rboyd/fpv-drone-racing-gate/reference/picture_frame/ATTRIBUTION.md

# User-supplied picture-frame reference

Tony Youngblood, **Snap-Together Modular Picture Frame – Fits Any Size Picture**.

Source: https://printables.com/model/150138-snap-together-modular-picture-frame-fits-any-size

License stated in supplied PDF: **Creative Commons Attribution–ShareAlike 4.0 International**.
https://creativecommons.org/licenses/by-sa/4.0/

Extracted from the user-provided `~/Downloads/snap-together-modular-picture-frame-fits-any-size-picture-model_files.zip`. Only the three STL references used in Blender and the supplied documentation PDF are retained here. STL files are unchanged. In the study Blender scene 10, they are converted from millimetres to metres, repositioned, and given a display material. That reference scene/render is shared under CC BY-SA 4.0 with this attribution. The exported gate test coupons use newly constructed geometry; they are not dimensionally compatible with this reference model.

Design observations: repeated snap teeth and lengths, plus a small calibrator. Source print instructions require supports under some frame edges. Therefore the source meshes are reference-only, excluded from our A1 Mini support-free test plates.

The complete unmodified CC BY-SA 4.0 license is included in [LICENSE](LICENSE). The project's CC BY-NC-SA and PolyForm licenses do not restrict the permissions granted for this reference material.
