rboyd/fpv-drone-racing-gate/studies/posterboard_hybrid.html

# Posterboard + printed framing

Same 2700 × 2700 mm gate, 1500 mm opening and existing PVC backing. The two strongest candidates to test are 600 × 450 mm sheets with a middle support rib for low cost, and 300 × 250 mm inserts for smaller replaceable panels. Nominal panel sizes; a few end fillers preserve the exact gate dimensions.

Study, not a finished frame design. Shared rails avoid two separate frames along every seam. PETG figures include a 20% rail allowance for joints/nodes, 250 g for PVC mounts, and 10% printing waste. Existing PVC, brace connectors, bases and anchors are excluded.

Rail plastic cross-section: mm²
Filament price: $/kg
Posterboard price: $/sheet

## Material and effort comparison

Click a size to see its face layout and a verified sheet-cut pattern. Costs are for the new face system only.

Nominal panels | Pieces | Sheets | Rail length | PETG | 1 kg spools | Consumed material | Whole-spool purchase

## One 22 × 28 inch stock sheet

## What changes the result?

Paper size: a 300 mm square is just too wide to get two across the 558.8 mm stock width. A 300 × 250 rectangle yields four per sheet; mixed orientation yields five 300 × 200 rectangles. The true area-only minimum is 13 sheets, but these repeatable layouts need 17–28.

Panel support: smaller bays should flex less, but more rail joints do not automatically make the whole gate stronger. The middle-rib option retains 20 paper pieces while supporting each large panel as two roughly 300 × 450 mm bays. Ribs need light retainers to work under wind from both directions.

Printer size: use rail bodies up to 150 mm long plus compact connectors, within an approximately 170 mm envelope. Several rails can print together; rail piece counts are not print-job counts. One-piece 150 mm panel frames are possible, but duplicate the shared edges and use more material.

Outdoor use: the $0.99 listing describes cardstock and gives no wet-weather rating. Treat it as a replaceable dry-weather insert; framing does not waterproof it. Wind area remains approximately 5.04 m², so existing guying/ballast remains relevant.

Detailed study · Calculation table · Exact layouts and assumptions

Sources: Hobby Lobby $0.99 cardstock (https://www.hobbylobby.com/Art-Supplies/Project-Supplies/Poster-Projects/Poster-Board---22-x-28/p/81118411); PETG density 1.28 g/cm³. Prices exclude tax/shipping and are scenario assumptions except the listed posterboard price. No stiffness or wind rating is claimed.
