rboyd/fpv-drone-racing-gate/output/pvc_paper_gate/index.html

# PVC does the spanning / printed parts do the joining

One outer PVC perimeter and a PVC ring around each opening. Paper conceals the pipes and fittings from the front; magnets sit 18 mm inside the edges. The shared divider enables a 2700 × 4790.4 mm two-level obstacle.

Open Blender · Design and assembly PDF · Full guide · Download kit

Configuration | Pieces | PETG kg | Print h | $6 PVC sticks | Subtotal*
Basic single, long pipes | 64 | 1.370 | 56.6 | 7 | $69.40
Recommended single | 62 | 1.759 | 71.0 | 6 | $71.17
Two-level Split-S | 108 | 2.814 | 114.5 | 10 | $116.27

*PVC + PETG at $20/kg. Face skeleton only; add magnets, cord, paper, adhesive, base, guys and anchoring. Actual local A1 Mini slicing estimates. Five production part types for the recommended single and double.

First print: FIRST_FIT for the A1 Mini — 124.59 g / 4.95 hours. One outer corner, sleeve, cord saddle, bore gauge and optional front pad. Check actual pipe and magnet fit before printing the gate.

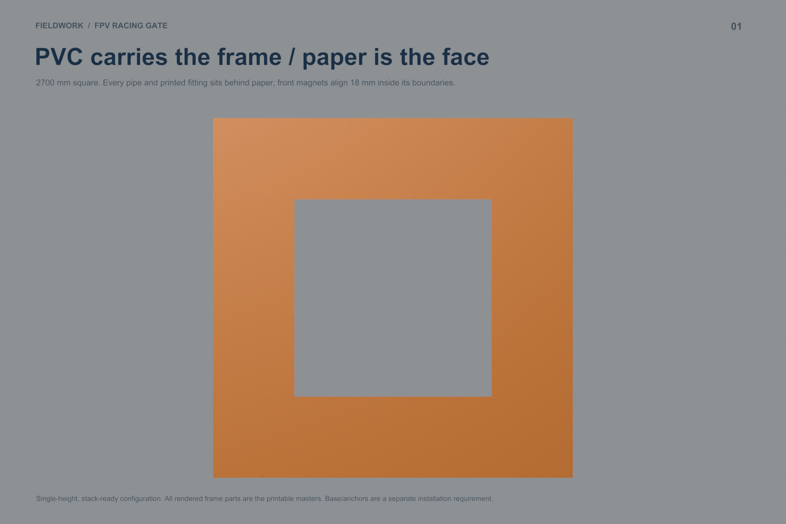
[picture p11: output/pvc_paper_gate/renders/01_SINGLE_FRONT.png]
01_SINGLE_FRONT


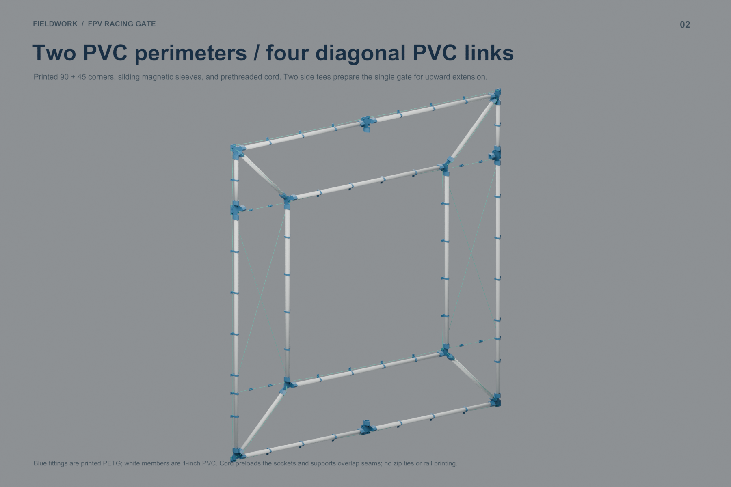
[picture p12: output/pvc_paper_gate/renders/02_SINGLE_BACK.png]
02_SINGLE_BACK


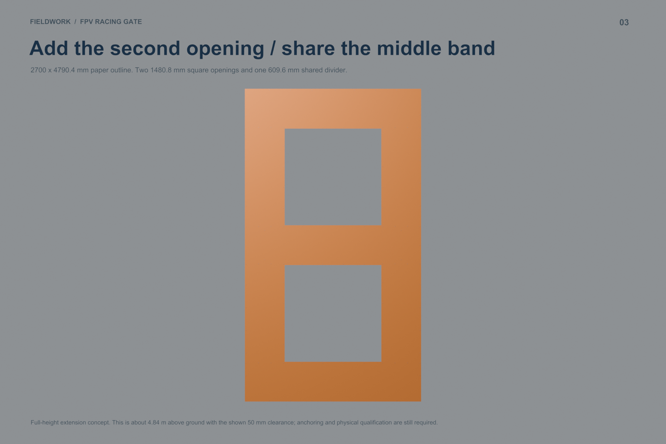
[picture p13: output/pvc_paper_gate/renders/03_SPLIT_S_FRONT.png]
03_SPLIT_S_FRONT


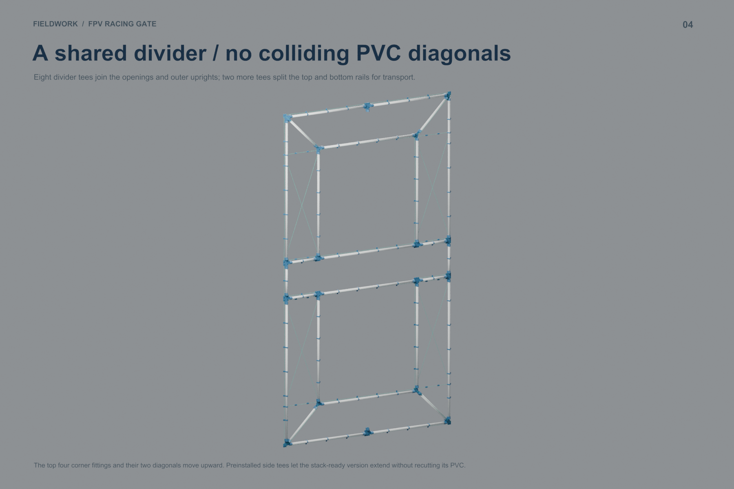
[picture p14: output/pvc_paper_gate/renders/04_SPLIT_S_BACK.png]
04_SPLIT_S_BACK


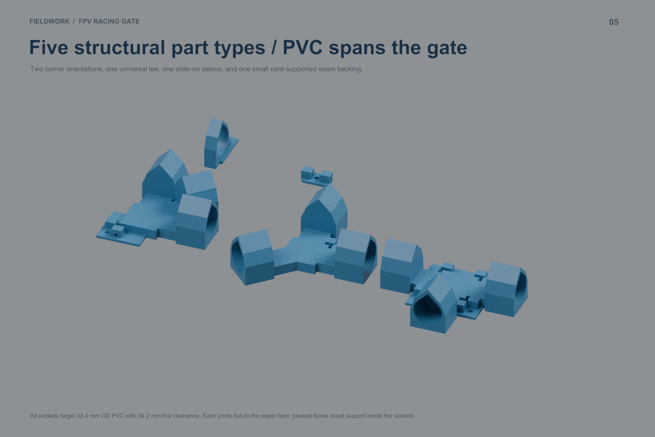
[picture p15: output/pvc_paper_gate/renders/05_PRINTED_PARTS.png]
05_PRINTED_PARTS


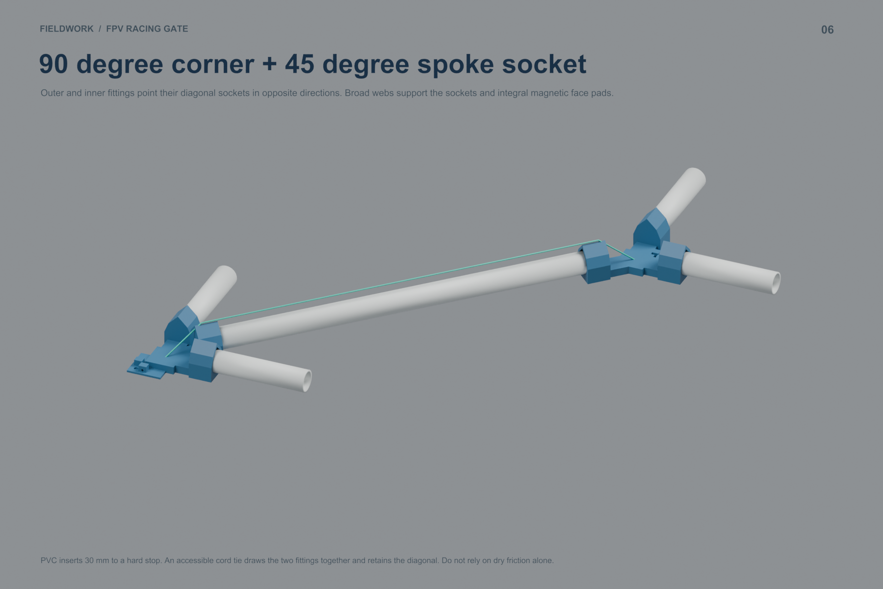
[picture p16: output/pvc_paper_gate/renders/06_CORNER_AND_DIAGONAL.png]
06_CORNER_AND_DIAGONAL


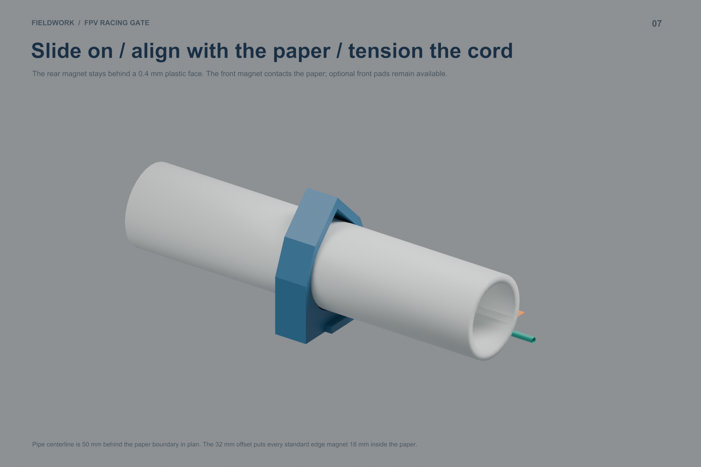
[picture p17: output/pvc_paper_gate/renders/07_MAGNET_SLEEVE.png]
07_MAGNET_SLEEVE


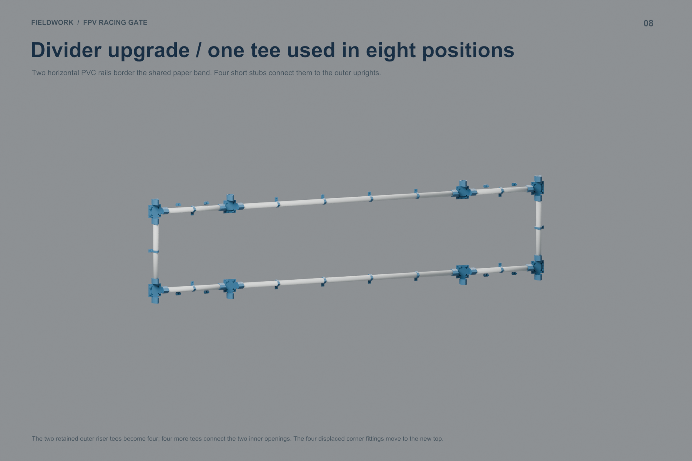
[picture p18: output/pvc_paper_gate/renders/08_SHARED_DIVIDER.png]
08_SHARED_DIVIDER


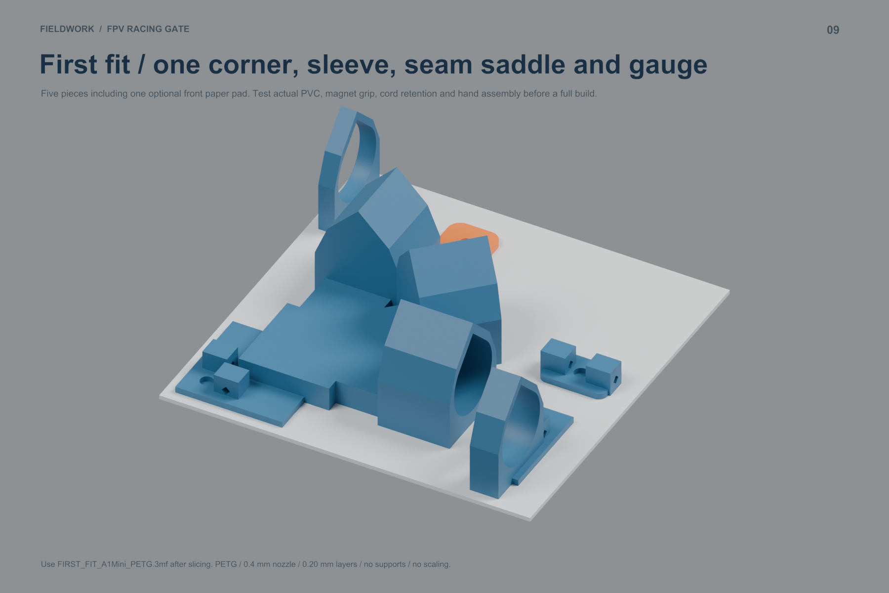
[picture p19: output/pvc_paper_gate/renders/09_FIRST_FIT_PLATE.png]
09_FIRST_FIT_PLATE


## Fabrication ledgers

### stack_ready

Parts · Print queue · PVC cuts · Stock nesting · Sleeve positions · Magnet positions · Paper cuts · Cord cuts · Face map

### split_s

Parts · Print queue · PVC cuts · Stock nesting · Sleeve positions · Magnet positions · Paper cuts · Cord cuts · Face map

### basic

Parts · Print queue · PVC cuts · Stock nesting · Sleeve positions · Magnet positions · Paper cuts · Cord cuts · Face map

Comparison · Upgrade parts · Upgrade PVC · Digital checks

All supplied plates fit with at least 5 mm bed clearance and slice without supports or warnings. Front pads are optional; the frame-side plastic skins and peaked sleeve roofs remain. Physical load testing and a qualified base/anchoring design remain outstanding, particularly at the 4.79 m stacked height. No printer job was submitted.
