rboyd/fpv-drone-racing-gate/output/paper_roll_study/index.html

FPV RACING GATE / EXPERIMENTAL ITERATION

# Paper face, click frame and magnetic clamps

Four identical 2090.4 × 609.6 mm strips. One PVC back. Compare three bracing layouts, reversible joints and diagonal break-apart print stacks.

Open Blender model · Visual study PDF · Assembly and test guide · Download study kit

Preferred trial: mechanical click joints + alternating diagonal webs + magnetic paper pads. Magnets can dominate cost: 336 discs at the pictured spacing. See the guide for wider spacing and magnet-free retention.

Experimental parts, not a production gate kit. Gate rails and full-gate dock sites are schematic. The exact exported interfaces fit the A1 Mini and have been sliced, but physical strength, latch fatigue, magnet grip and PETG stack separation have not been tested. The source picture-frame meshes are reference-only.

## Start with the seven-piece D-lug and PVC dock plate

Use plate 05 for the latest concept. A second optional test is the small stack plate. Do not print all 25 variants: they include clearance comparisons and alternative processes.

Sliced A1 Mini / PETG project | Material | Time | Notes
05_D_MAGNET_AND_DOCK | 33.2 g | 113 min | No slicing warning
01_CLICK_AND_MAGNET_JOINTS | 23.9 g | 65 min | No slicing warning
02_PAPER_CLAMP_TESTS | 32.9 g | 124 min | No slicing warning
03_STACK_SEPARATION_TESTS | 33.3 g | 94 min | No slicing warning
04_PVC_COLLAR_TEST | 23.4 g | 71 min | No slicing warning
DIAGONAL_1x220 | 15.9 g | 43 min | No slicing warning
DIAGONAL_8x220 | 104.3 g | 259 min | No slicing warning
06_OVERNIGHT_26_RAILS | 301.4 g | 714 min | No slicing warning

0.4 mm nozzle, 0.2 mm layers, 3 walls, 15% infill, textured PEI; supports off. No job has been sent to a printer. Source STLs/3MFs: printable folder. Digital checks · Stack findings · Research.

## Explore the Blender views

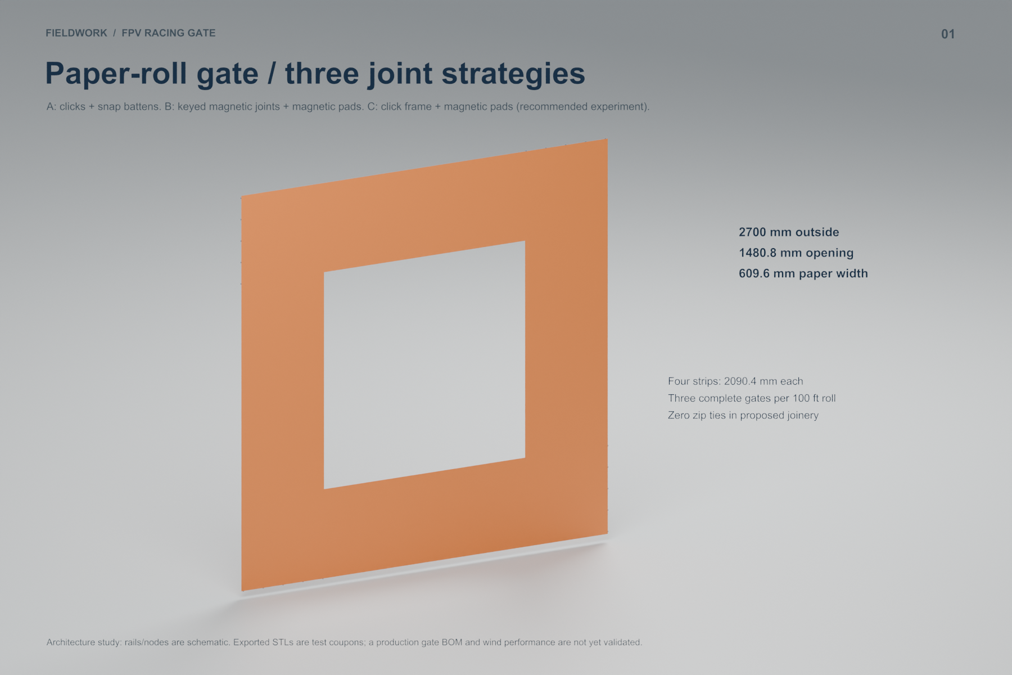
[picture p35: output/paper_roll_study/renders/01_PAPER_GATE.png]
Paper layout and three retention strategies


Paper layout and three retention strategies

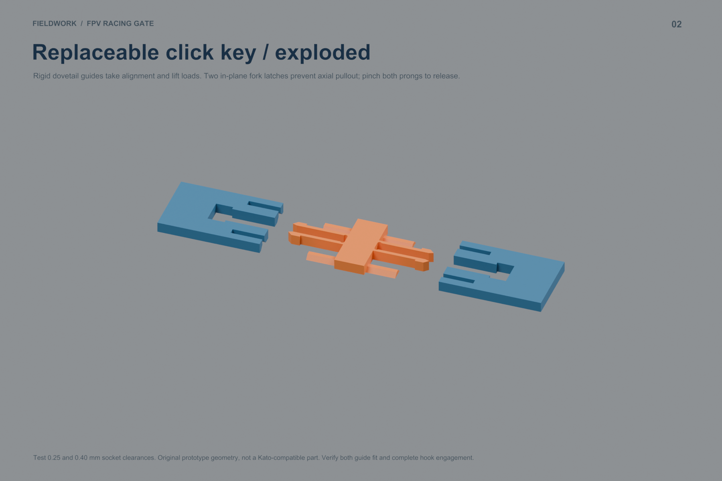
[picture p36: output/paper_roll_study/renders/02_CLICK_JOINT.png]
Replaceable click key and clearance samples


Replaceable click key and clearance samples

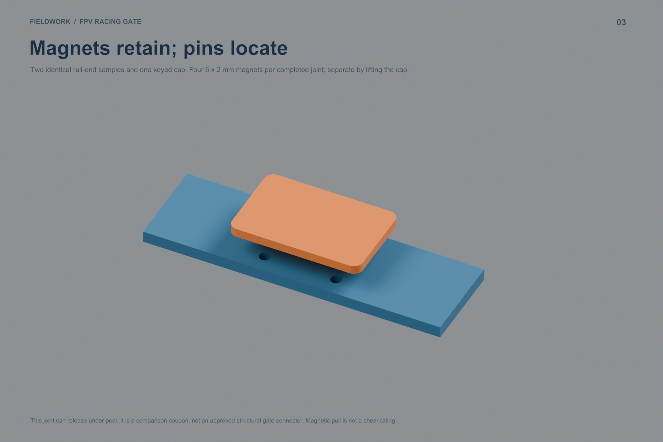
[picture p37: output/paper_roll_study/renders/03_MAGNETIC_SPLICE.png]
Magnet-held structural splice alternative


Magnet-held structural splice alternative

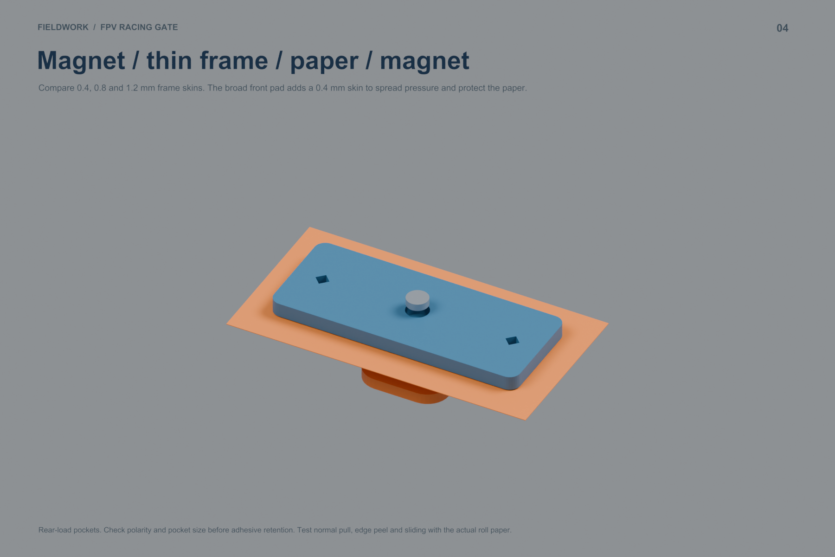
[picture p38: output/paper_roll_study/renders/04_PAPER_MAGNET_STACK.png]
Magnetic paper sandwich and skin thickness


Magnetic paper sandwich and skin thickness

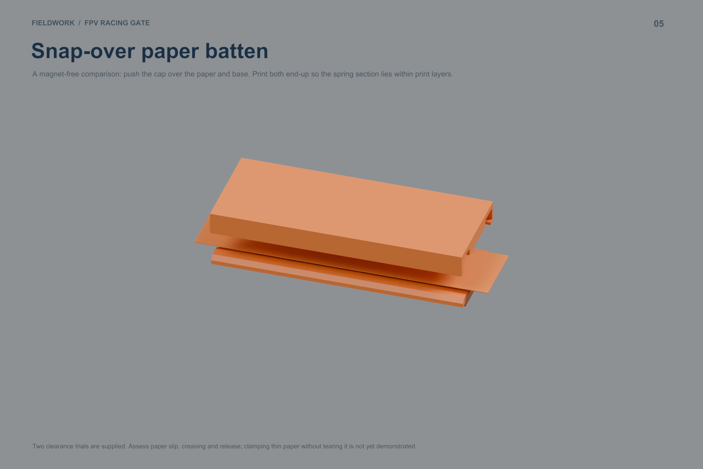
[picture p39: output/paper_roll_study/renders/05_MECHANICAL_PAPER_CLAMP.png]
Magnet-free snap-over batten


Magnet-free snap-over batten

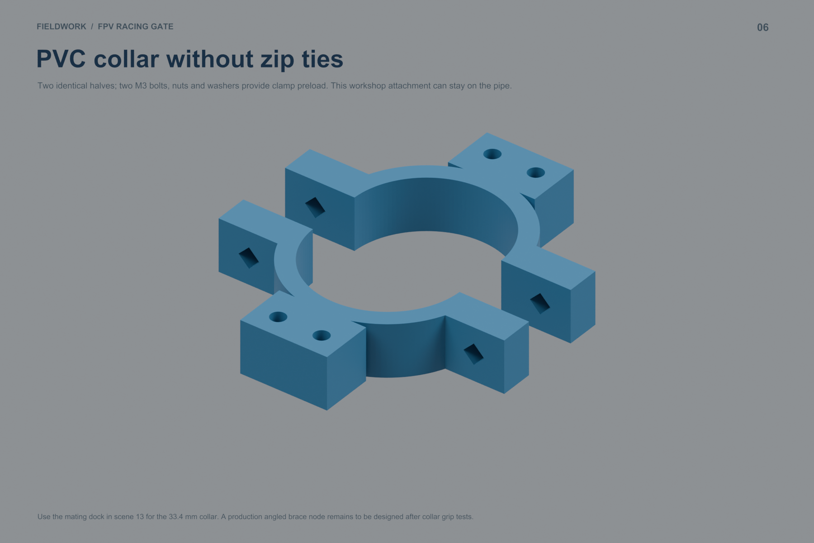
[picture p40: output/paper_roll_study/renders/06_NO_TIE_PVC_COLLAR.png]
Bolted PVC collar halves


Bolted PVC collar halves

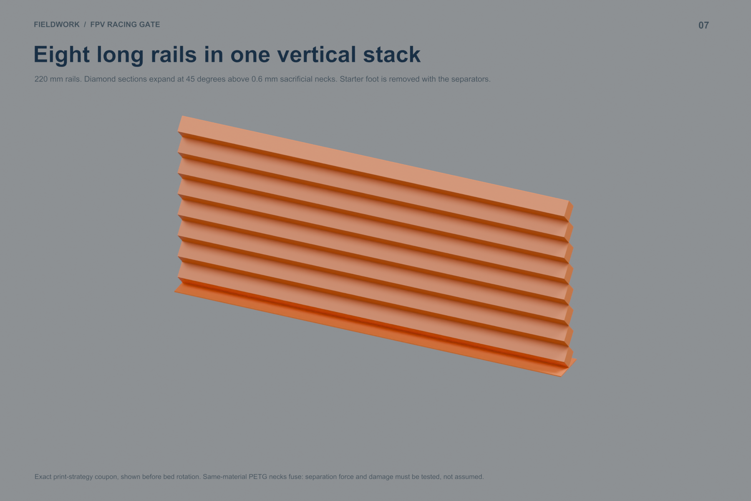
[picture p41: output/paper_roll_study/renders/07_DIAGONAL_STACK.png]
Eight 220 mm rails stacked vertically


Eight 220 mm rails stacked vertically

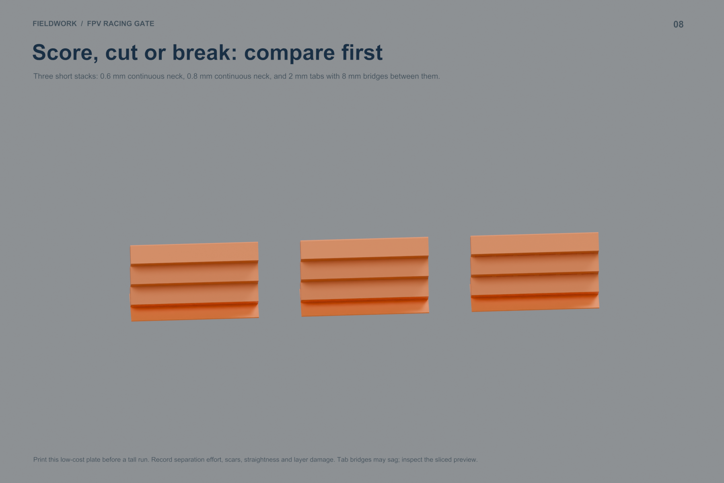
[picture p42: output/paper_roll_study/renders/08_STACK_COUPONS.png]
Short separation tests


Short separation tests

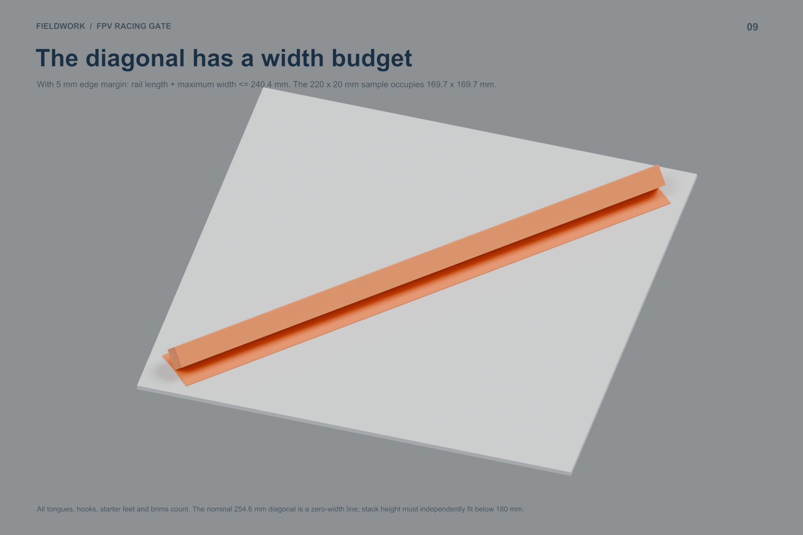
[picture p43: output/paper_roll_study/renders/09_A1_DIAGONAL_ENVELOPE.png]
Diagonal bed-fit calculation


Diagonal bed-fit calculation

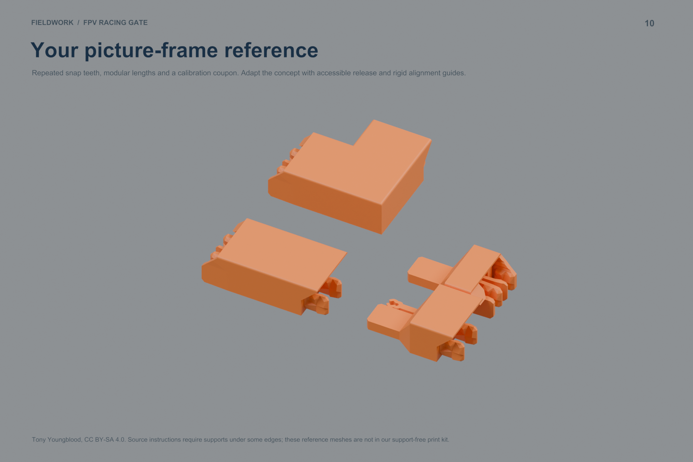
[picture p44: output/paper_roll_study/renders/10_PICTURE_FRAME_REFERENCE.png]
Tony Youngblood picture-frame reference


Tony Youngblood picture-frame reference

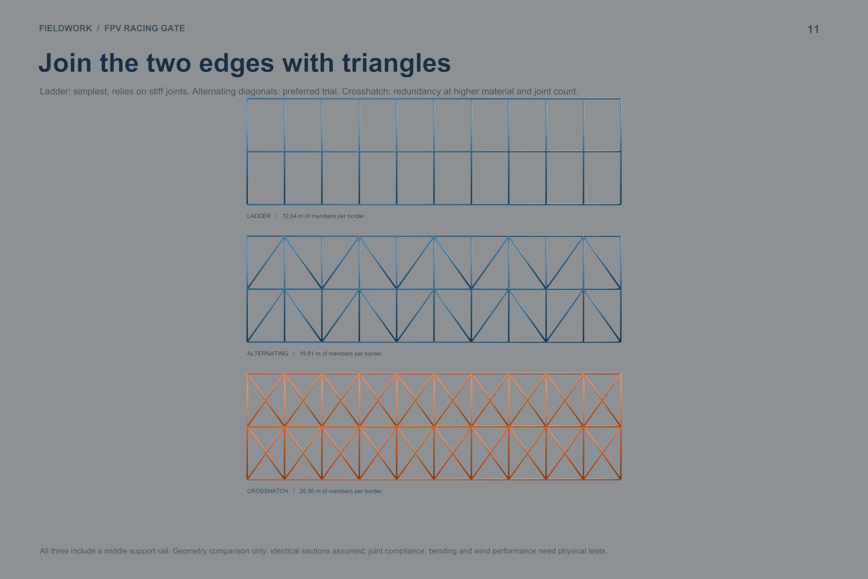
[picture p45: output/paper_roll_study/renders/11_BRACING_COMPARISON.png]
Ladder, alternating diagonals and crosshatch


Ladder, alternating diagonals and crosshatch

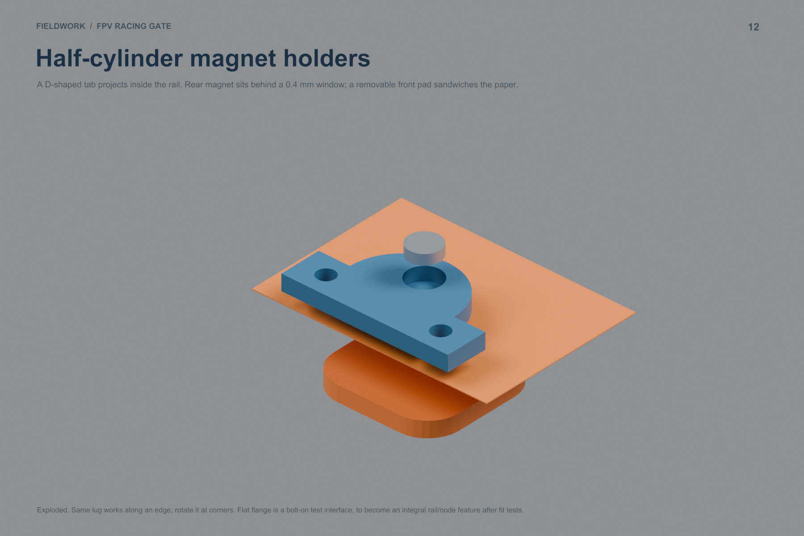
[picture p46: output/paper_roll_study/renders/12_HALF_CYLINDER_LUG.png]
Half-cylinder magnet holder


Half-cylinder magnet holder

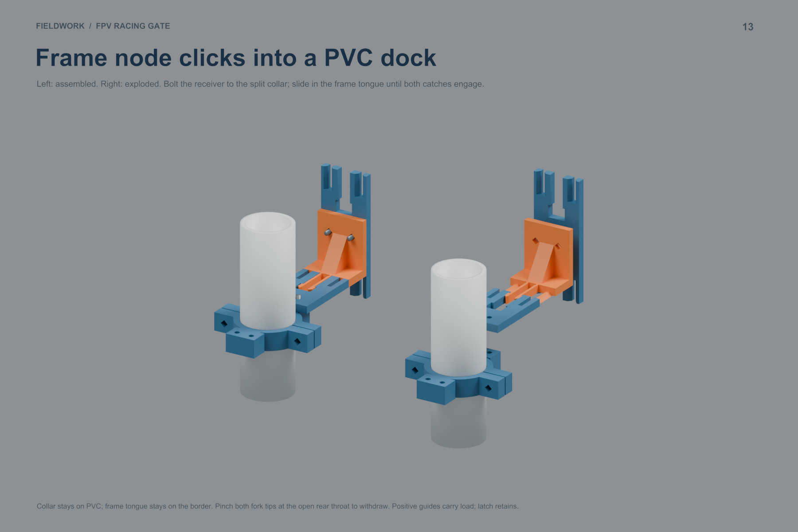
[picture p47: output/paper_roll_study/renders/13_FRAME_TO_PVC.png]
Assembled and exploded PVC quick-release dock


Assembled and exploded PVC quick-release dock

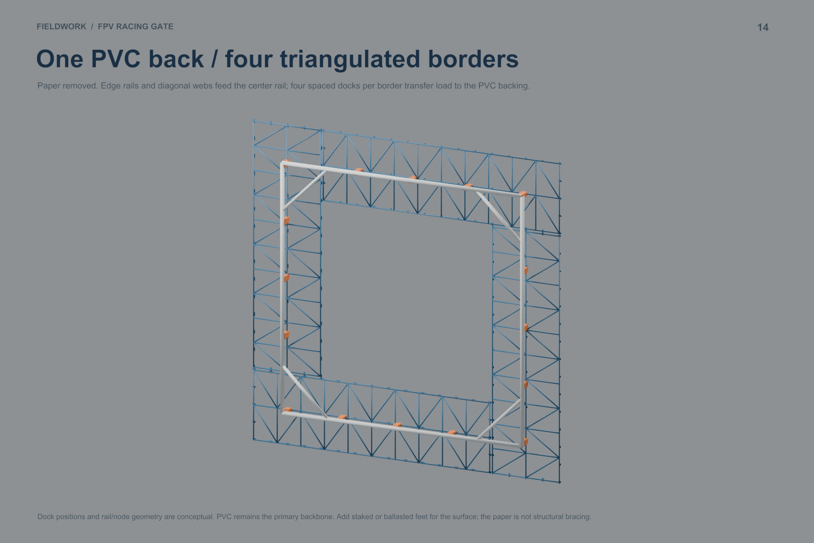
[picture p48: output/paper_roll_study/renders/14_GATE_BACKING_AND_LOAD_PATH.png]
Rear frame, triangulation and proposed docks


Rear frame, triangulation and proposed docks

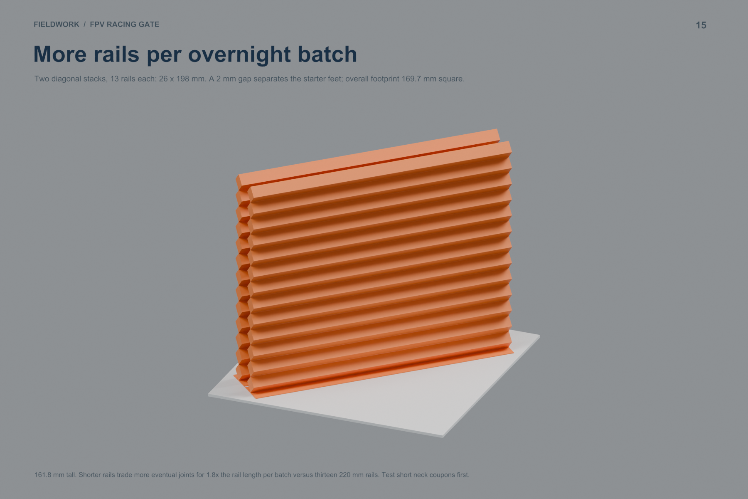
[picture p49: output/paper_roll_study/renders/15_TWO_STACKS_OVERNIGHT.png]
26-rail overnight manufacturing trial


26-rail overnight manufacturing trial

Baseline committed as 732f592; new work on iteration/paper-roll-click-magnet. The embedded picture-frame reference is by Tony Youngblood, CC BY-SA 4.0; attribution and license. Test-coupon geometry is newly modeled.
