rboyd/fpv-drone-racing-gate/output/posterboard_concepts/index.html

# Four folding FPV gate options

Uniform slide-in posterboard. One PVC backing frame. Four loaded face bundles under 1.2 m long.

Recommended: B / half sheets. One cut per 22 × 28 in sheet; 24 identical 14 × 22 in inserts. Four book-fold bundles about 1079 × 563 × 40 mm. Opening 1595 mm; outside 2720 mm.

Option | Insert, mm | Cuts / gate | Folded L × W, mm | PETG | Face materials
A / Quarter sheets | 355.6 × 279.4 | 36 | 1079 × 567 | 3.12 kg | $74
B / Half sheets | 355.6 × 558.8 | 12 | 1079 × 563 | 2.55 kg | $63
C / Whole sheets | 711.2 × 558.8 | 0 | 715 × 563 | 2.37 kg | $59
D / Exact-size metric | 346 × 196 | 90 | 1050 × 600 | 3.82 kg | $94

Planning quantities at $20/kg PETG and $0.99 per sheet; includes joint/waste allowances. Excludes PVC, bases, brace clamps, anchors, labor and tax. These are not slicer-derived bills of materials.

Concept and fit-test package. Seven manifold coupon meshes fit the A1 Mini and target support-free printing. Full rail nodes, twin bridge keys, hinge adapters, PVC keeper and mounting interfaces still require detail and physical fit testing. No wind, fatigue or impact rating is claimed. Posterboard is a dry-weather, replaceable face.

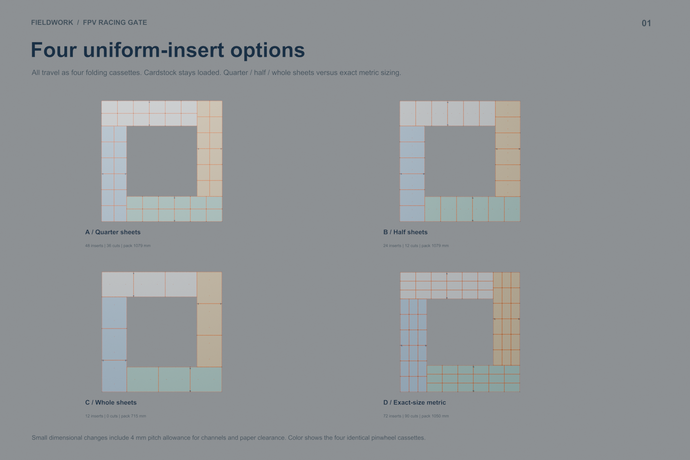
[picture p50: output/posterboard_concepts/renders/01_OPTIONS.png]
01 OPTIONS


Scene 01: Options

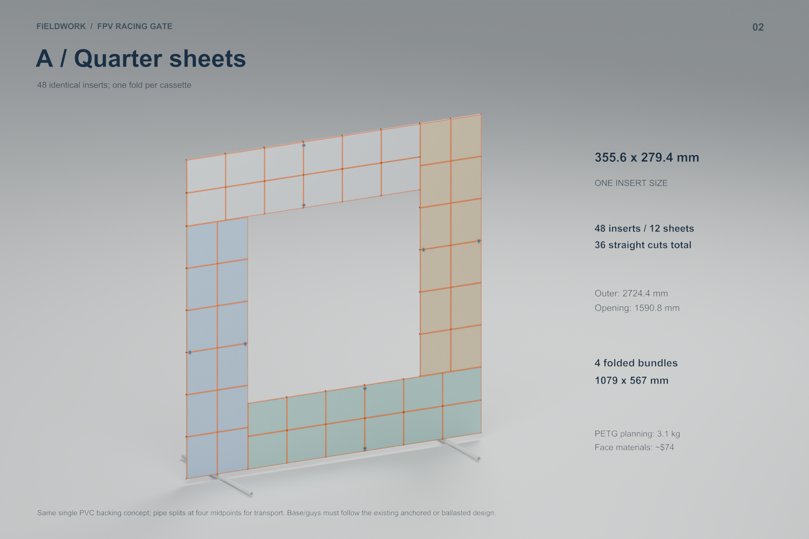
[picture p51: output/posterboard_concepts/renders/02_A_ASSEMBLED.png]
02 A ASSEMBLED


Scene 02: A Assembled

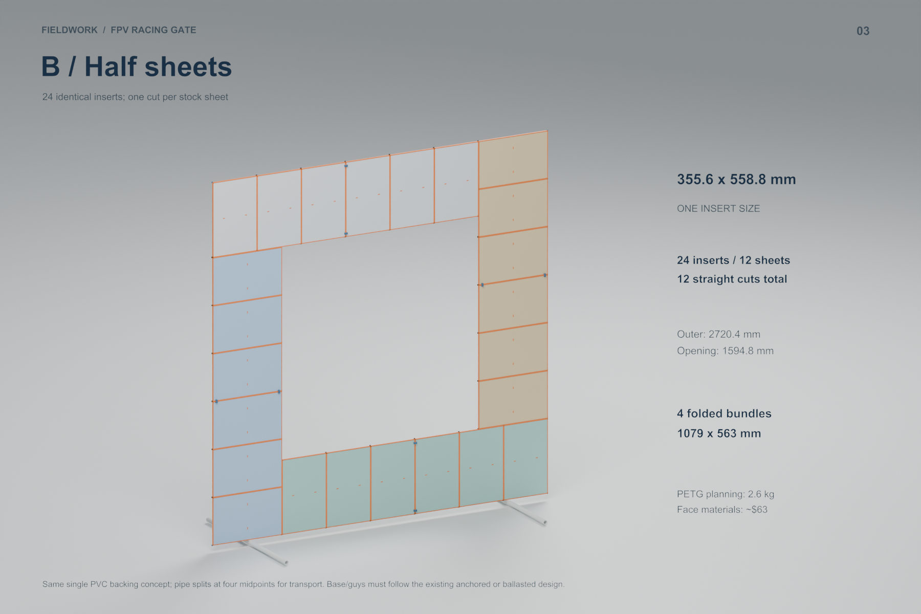
[picture p52: output/posterboard_concepts/renders/03_B_ASSEMBLED.png]
03 B ASSEMBLED


Scene 03: B Assembled

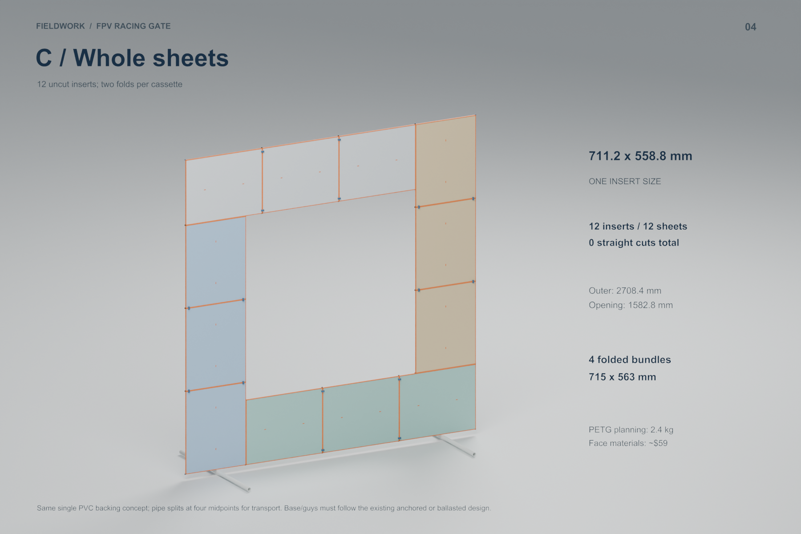
[picture p53: output/posterboard_concepts/renders/04_C_ASSEMBLED.png]
04 C ASSEMBLED


Scene 04: C Assembled

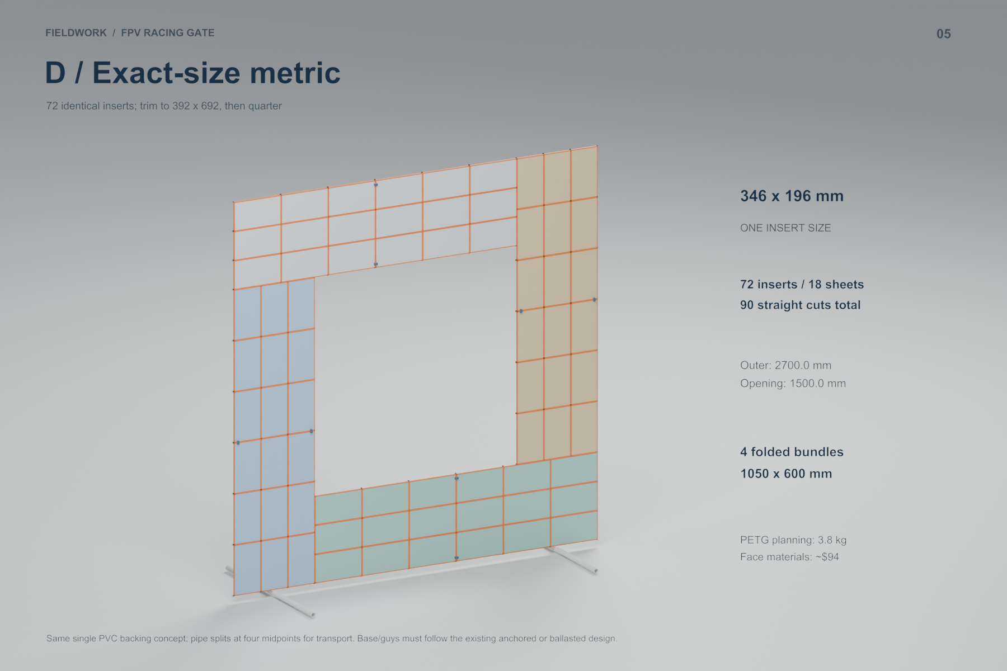
[picture p54: output/posterboard_concepts/renders/05_D_ASSEMBLED.png]
05 D ASSEMBLED


Scene 05: D Assembled

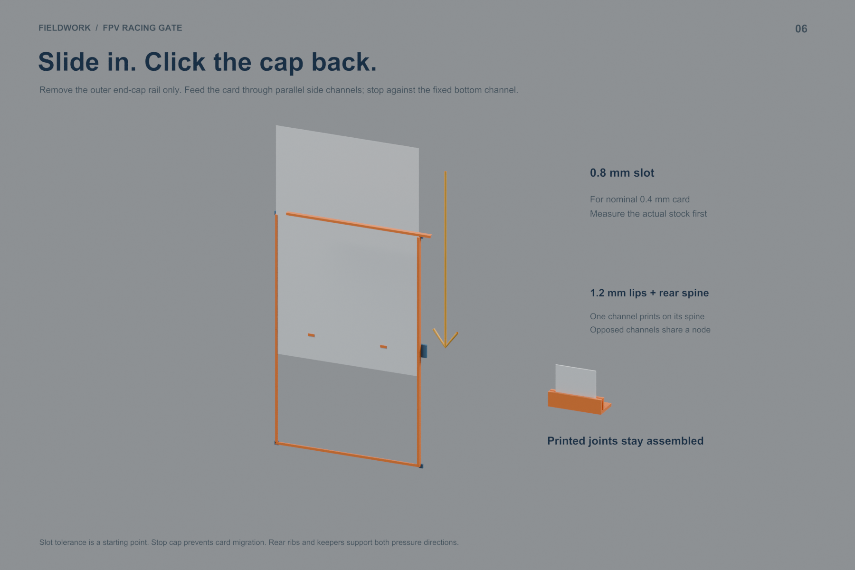
[picture p55: output/posterboard_concepts/renders/06_SLIDE_IN.png]
06 SLIDE IN


Scene 06: Slide In

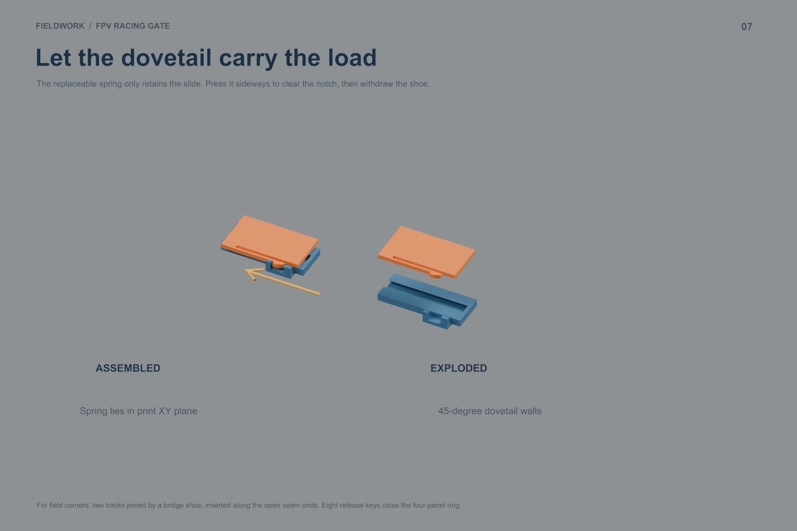
[picture p56: output/posterboard_concepts/renders/07_CLICK_JOINERY.png]
07 CLICK JOINERY


Scene 07: Click Joinery

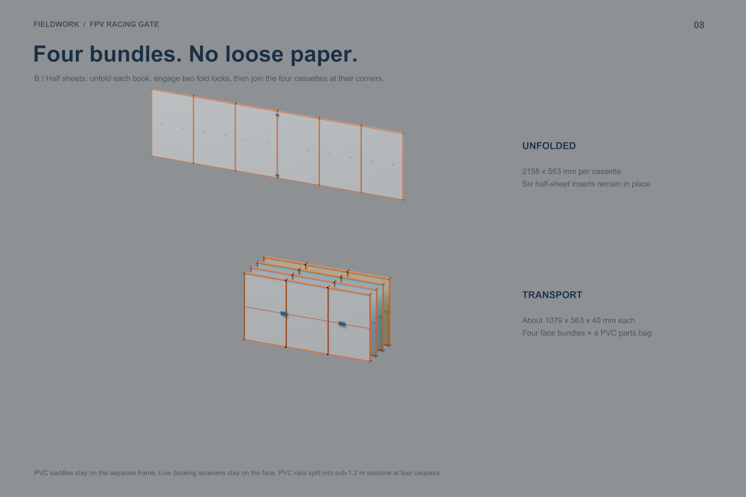
[picture p57: output/posterboard_concepts/renders/08_FOUR_PACKS.png]
08 FOUR PACKS


Scene 08: Four Packs

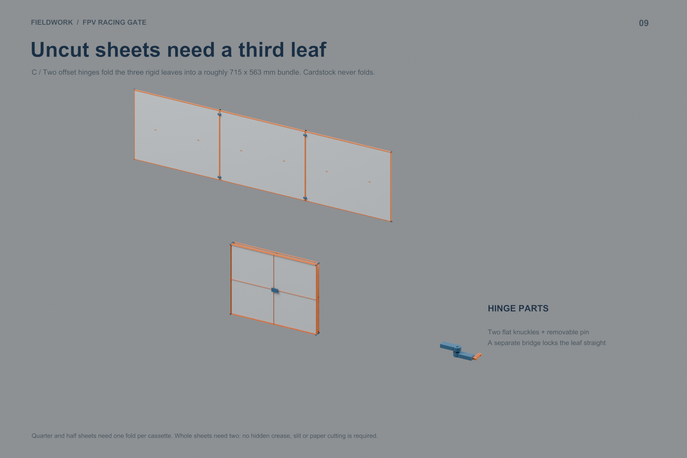
[picture p58: output/posterboard_concepts/renders/09_TRIFOLD_AND_HINGE.png]
09 TRIFOLD AND HINGE


Scene 09: Trifold And Hinge

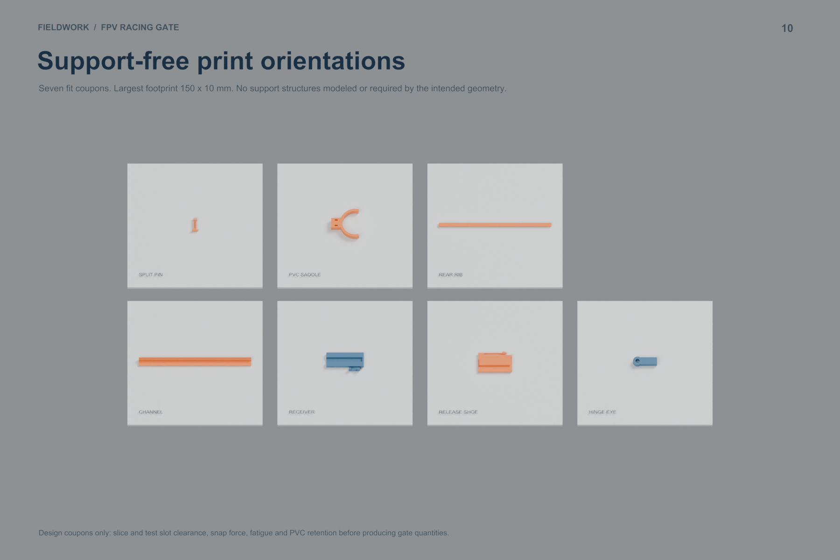
[picture p59: output/posterboard_concepts/renders/10_PRINT_ORIENTATIONS.png]
10 PRINT ORIENTATIONS


Scene 10: Print Orientations

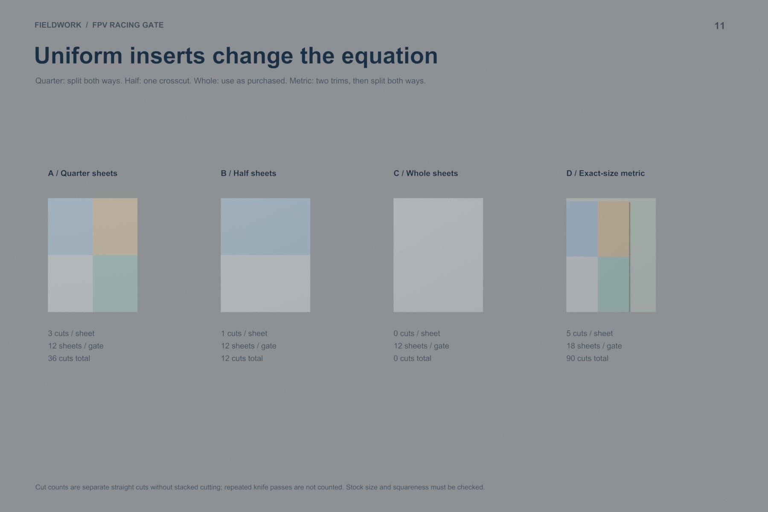
[picture p60: output/posterboard_concepts/renders/11_STOCK_CUTS.png]
11 STOCK CUTS


Scene 11: Stock Cuts

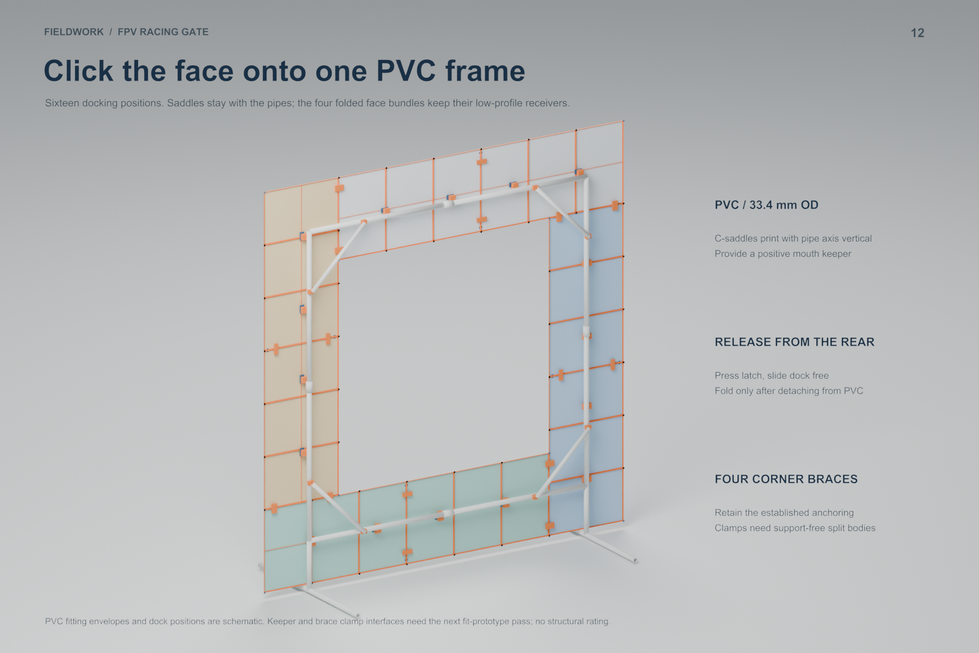
[picture p61: output/posterboard_concepts/renders/12_REAR_DOCKING.png]
12 REAR DOCKING


Scene 12: Rear Docking

## Printable fit coupons

Print and test one joint/channel first. These files do not constitute a complete gate kit.

- PVC_C_saddle_OD33p4_mm.stl
- channel_150_on_spine_mm.stl
- dovetail_receiver_50_mm.stl
- dovetail_shoe_release_spring_mm.stl
- hinge_knuckle_flat_mm.stl
- hinge_split_pin_flat_mm.stl
- support_rib_150_mm.stl

## Review / assembly

Select scenes 01–12 in Blender's scene selector. Objects and collections remain editable; the guide is also embedded in Blender's text blocks. The face docks detach from PVC before folding. The frame splits at its four midpoints, and travels separately.

Model checks: exact ring coverage, non-overlapping stock cuts, uniform inserts, transport leaf lengths, coupon manifoldness and print-bed envelopes. See layout validation and coupon geometry.
