rboyd/fpv-drone-racing-gate/output/paper_roll_study/Paper_Roll_Study.pdf

# Paper-roll gate / design comparison

Baseline commit 732f592 | New experimental branch: iteration/paper-roll-click-magnet

Preferred trial: positive mechanical click joints, alternating diagonal webs, and removable magnetic paper pads. One PVC backing square and four corner braces remain the backbone.

Approved layout: four identical 2090.4 x 609.6 mm paper strips, 2700 mm outside and 1480.8 mm opening. Three gates plus spare paper per 100-foot roll. Four rigid borders travel with their paper attached.

Arrangement | Members per border | Main tradeoff
Ladder | 12.64 m | Lowest material; depends on joint stiffness
Alternating diagonals | 19.81 m | Triangles resist racking; preferred trial
Full crosshatch | 26.98 m | 36% more length than alternating; crossing nodes

Cost caution: at 150 mm maximum edge-pad spacing plus middle pads, the gate uses 168 clamp pairs / 336 magnets. At an assumed $0.20 per magnet that is $67.20, before plastic and PVC. At 300 mm spacing the trial count is 192 magnets. Holding and paper flutter need testing.

The heavy 12 mm diamond sample would use roughly 4.5 kg for all members in the alternating layout, before nodes. Lighter webs and a sparser structure need testing; a one- or two-spool finished gate is not established.

Detailed assembly, costs, sources and limitations: STUDY_AND_TEST_GUIDE.md, RESEARCH.md, PRINT_STRATEGY.md

# Print the interfaces before the gate

25 experimental STL variants, not 25 required production part types. No printer job has been sent.

Start with plate 05: seven pieces test the D-shaped magnetic holder and complete PVC dock. Add a paper scrap, two 6 x 2 mm magnets and actual 33.4 mm OD PVC. The dock needs four M3x25 and two M3x16 bolts, six nuts and twelve washers.

Plate / experiment | PETG | Slicer estimate
05_D_MAGNET_AND_DOCK | 33.2 g | 1 h 53 min
01_CLICK_AND_MAGNET_JOINTS | 23.9 g | 1 h 05 min
03_STACK_SEPARATION_TESTS | 33.3 g | 1 h 34 min
DIAGONAL_8x220 | 104.3 g | 4 h 19 min
06_OVERNIGHT_26_RAILS | 301.4 g | 11 h 54 min

Diagonal batch: two stacks of thirteen 198 mm rails fit 169.7 x 169.7 x 161.8 mm. They are plain manufacturing samples, without final rail-end joints. Test short stacks before the overnight plate.

Stack findings: 0.4 mm necks vanished in the standard slicer profile. Current continuous trials use 0.6 and 0.8 mm; every neck layer has extrusion. End tabs removed an initial cantilever warning. All current slices have supports off and no warnings; physical bridging and PETG separation remain untested.

Verified digitally: 25 manifold masters, 31 actual A1 Mini/PETG slices and 20 assembled-pair interference checks. The gate overview is schematic; production corner/diagonal nodes and brace interfaces remain to be integrated after measured fit tests.

Source picture-frame scene: Tony Youngblood, CC BY-SA 4.0. See reference/picture_frame/ATTRIBUTION.md.
