rboyd/fpv-drone-racing-gate/output/drone_clearance_study/Drone_Clearance_Study.pdf

# One drone, four opening sizes

The imported MK4 assembly has a 401.3 mm full propeller-sweep width. A 1000 mm opening is the suggested next trial, with 299 mm per side on a centered straight approach. The current opening gives 540 mm per side. The 800 mm option is tighter at 199 mm per side.

Opening (mm) | Outer (mm) | Side gap (mm) | Vertical gap (mm)
1480.8 | 2700.0 | 540 | 656
1200.0 | 2419.2 | 399 | 515
1000.0 | 2219.2 | 299 | 415
800.0 | 2019.2 | 199 | 315

All gaps are per edge, at 20-degree forward pitch, zero yaw and roll. The projected envelope is centered. Battery dimensions (110 x 40 x 45 mm) are assumed; confirm against your build. These are geometric gaps, not guaranteed flight margins.

Keep the existing printed fittings and 24-inch paper bands. Replace eight long PVC members: 1560.8 mm current, 1280 mm for 1200 opening, 1080 mm for 1000, or 880 mm for 800. Sixteen short 389.6 mm members remain. Dry-fit before batch cutting. Full methods and paper cuts: accompanying README.md.

Drone reference: Dendy / Printables 1515387, CC BY-NC 4.0; the uploader disclaims original authorship of the included MK4 frame. Original gate material retains the separate project license. Cyan rings are prop-sweep envelopes, not physical guards.

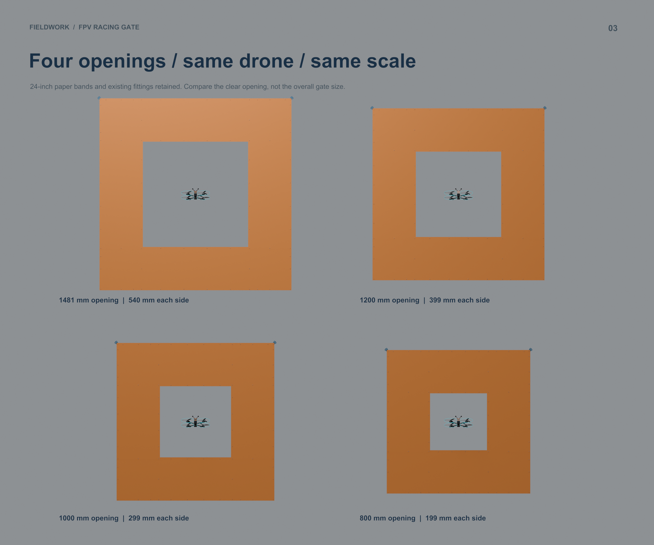
[picture p64: page 4]

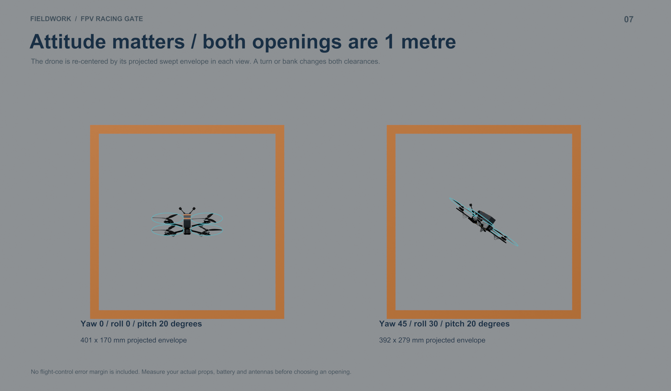
[picture p65: page 8]
