rboyd/fpv-drone-racing-gate/LICENSING.md

# Licensing and commercial permissions

Copyright © 2026 Robert Boyd ([@rboyd](https://github.com/rboyd)) for original project material, to the extent the relevant rights subsist and are held by the licensor. These are public licenses, not a transfer of ownership or a public-domain dedication of the project.

## Designs, documentation and other original project content

Original gate designs, CAD geometry, drawings, STL models, model content in 3MF projects, Blender scenes, renders, PDFs, assembly guides, original tables and other original non-software content are licensed under **Creative Commons Attribution-NonCommercial-ShareAlike 4.0 International (CC BY-NC-SA 4.0)**, except for the third-party material identified below.

The complete, unmodified license is in [LICENSE](LICENSE); the [official summary](https://creativecommons.org/licenses/by-nc-sa/4.0/) explains its main terms. This scope includes original project content in earlier iteration directories; embedded third-party components remain separately licensed.

You may copy, share and adapt the licensed material for noncommercial purposes. When sharing, credit the creator, retain applicable notices, link the license and indicate changes. Shared adaptations must use CC BY-NC-SA 4.0 or another license allowed by its ShareAlike clause. The public license does not authorize commercial exploitation of protected project material; request separate permission for uses such as selling copies of the design files or selling printed copies that require the licensor's permission.

[NOTICE](NOTICE) supplies the attribution details. Reasonable attribution appropriate to the medium is sufficient; no particular logo, label placement or physical engraving is required by this notice.

## Python scripts and other original project software

Original source code in `scripts/` is licensed under **PolyForm Noncommercial License 1.0.0**. Read the complete, unmodified [scripts/LICENSE](scripts/LICENSE) and retain [scripts/NOTICE](scripts/NOTICE) when distributing it as required by that license.

PolyForm permits use, modification and distribution for its permitted purposes. Its text defines noncommercial purposes and expressly permits certain personal and noncommercial-organization uses. It is not a software ShareAlike license. It grants the software patent rights described in its Patent License clause; this notice does not take those rights back.

This software-specific license was selected because [Creative Commons recommends against using CC licenses for software](https://creativecommons.org/faq/#can-i-apply-a-creative-commons-license-to-software). It does not replace the separate license on the design assets generated or processed by the scripts. These noncommercial releases are source-available, rather than unrestricted open-source/open-hardware releases.

## Third-party material is excluded from these grants

The repository's default license does **not** relicense rights belonging to others:

- **Tony Youngblood's picture-frame model:** the three source STLs and supplied PDF in `reference/picture_frame/`, together with their adapted reference presentation in `output/paper_roll_study/Paper_Roll_Joinery_Study.blend` scene `10_PICTURE_FRAME_REFERENCE` and its render, retain **CC BY-SA 4.0**. Reproductions of that reference scene in study PDFs retain those terms too. See [the attribution](reference/picture_frame/ATTRIBUTION.md) and [full license](reference/picture_frame/LICENSE). The noncommercial restriction on the original gate designs does not apply to these separately licensed components.
- **GEPRC MK4 drone reference:** the user-supplied Dendy / Printables model 1515387 and imported drone geometry in the clearance and compact-gate studies retain **CC BY-NC 4.0**, with the original frame authorship qualification. See [its attribution](reference/geprc_mk4/ATTRIBUTION.md). This exception includes the reference geometry embedded in Blender and reproduced in study renders/PDFs.
- **Fonts, manufacturer presets and application data:** third-party fonts embedded in Blender/PDF files, Bambu Studio machine/filament/process settings in `slicer_profiles/` or 3MF files, and other third-party components retain their respective rights and applicable terms. Neither project license grants ownership of or additional rights to those components.
- **Supplied reference content:** third-party contributions in `WIP-design.md`, source screenshots, logos and other reference material remain subject to their owners' rights. Inclusion is not a claim of ownership or a new license from those owners.

For a file containing both original and third-party material, each grant applies only to the components within its stated scope. Existing third-party permissions, including commercial permissions under CC BY-SA, remain intact.

## Commercial permission and retained rights

For commercial use beyond the public licenses, contact **Robert Boyd via [@rboyd](https://github.com/rboyd)** or [open a commercial-licensing request](https://github.com/rboyd/fpv-drone-racing-gate/issues/new?title=Commercial%20licensing%20request). No commercial permission is granted merely by making a request or by receiving no response. A separate agreement can specify the permitted products, services, compensation and other terms.

The licensor retains the ability to use and commercially license the rights they own. Rights not granted by the applicable public license are reserved. CC BY-NC-SA does not grant patent or trademark rights; the software patent grant is governed by PolyForm as described above. No endorsement is implied.

The CC grant is irrevocable for recipients who comply with it; a later license change cannot withdraw rights already granted to those recipients. License conditions apply only where the licensor holds rights that the proposed use requires. They do not create exclusive rights over unprotected functional ideas, dimensions or independently created designs, and they do not override statutory exceptions. Accordingly, this is not a guarantee against every possible commercial manufacture of a functional object. Warranty and liability terms are in the full licenses.

## License text provenance

The standard license texts were copied without alteration from:

- [Creative Commons CC BY-NC-SA 4.0 plain text](https://creativecommons.org/licenses/by-nc-sa/4.0/legalcode.txt)
- [PolyForm Project's official Noncommercial 1.0.0 text](https://github.com/polyformproject/polyform-licenses/blob/1.0.0/PolyForm-Noncommercial-1.0.0.md)
- [Creative Commons CC BY-SA 4.0 plain text](https://creativecommons.org/licenses/by-sa/4.0/legalcode.txt)

This document identifies scope and summarizes the licenses. It does not modify their legal text or impose extra restrictions on permissions they grant.
