rboyd/fpv-drone-racing-gate/output/a1_full_size/renders/01_FULL_GATE.png

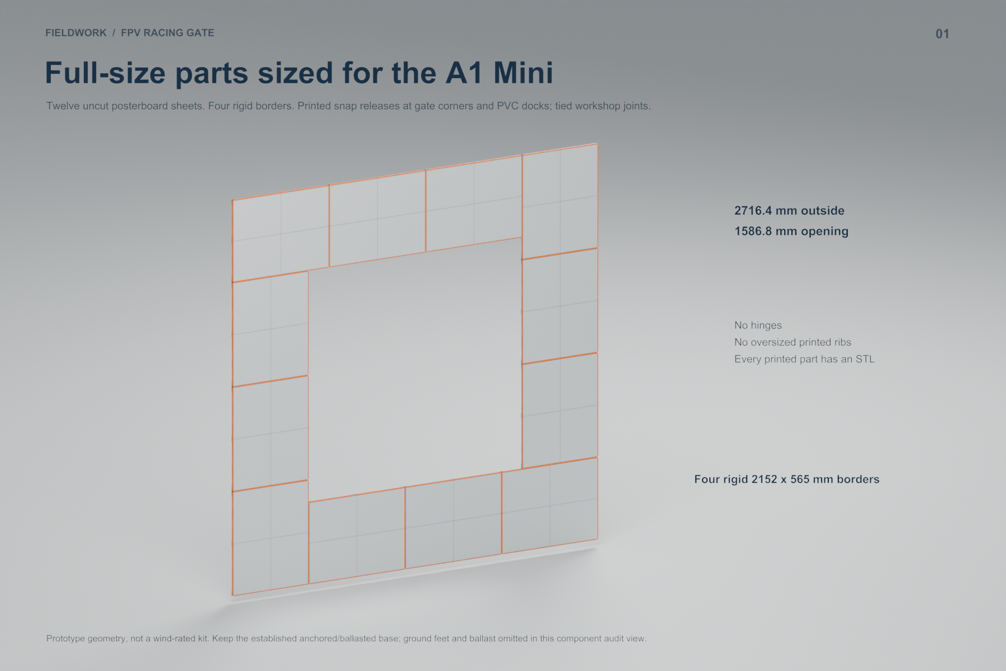
output/a1_full_size/renders/01_FULL_GATE.png
