rboyd/fpv-drone-racing-gate/output/a1_full_size/renders/05_TWO_CHANNELS.png

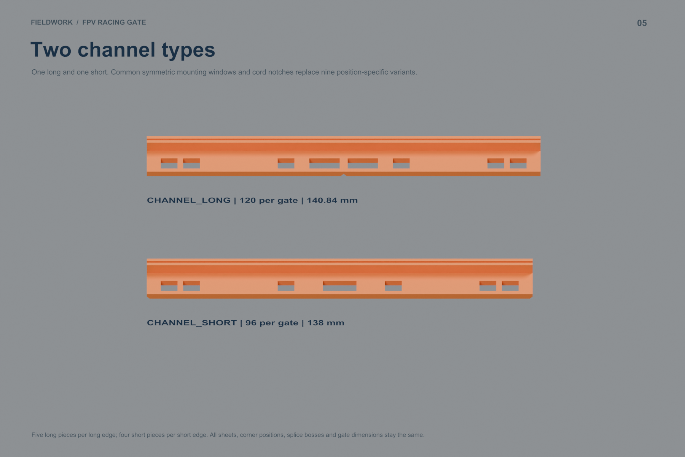
output/a1_full_size/renders/05_TWO_CHANNELS.png
