rboyd/fpv-drone-racing-gate/output/a1_full_size/renders/06_REAR_FRAME.png

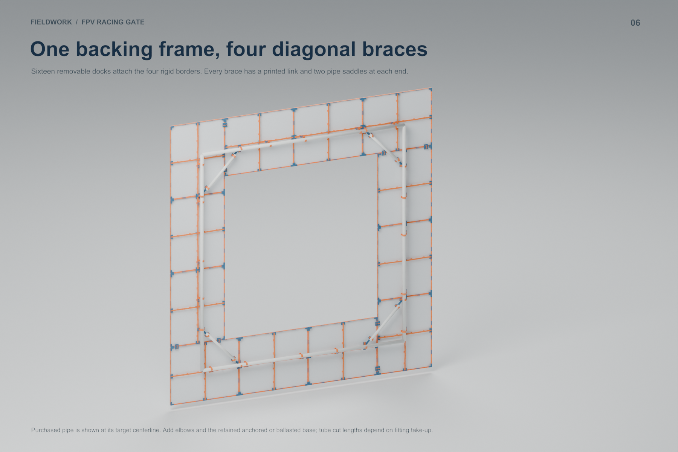
output/a1_full_size/renders/06_REAR_FRAME.png
