rboyd/fpv-drone-racing-gate/output/a1_full_size/renders/07_CHANNEL_JOINT.png

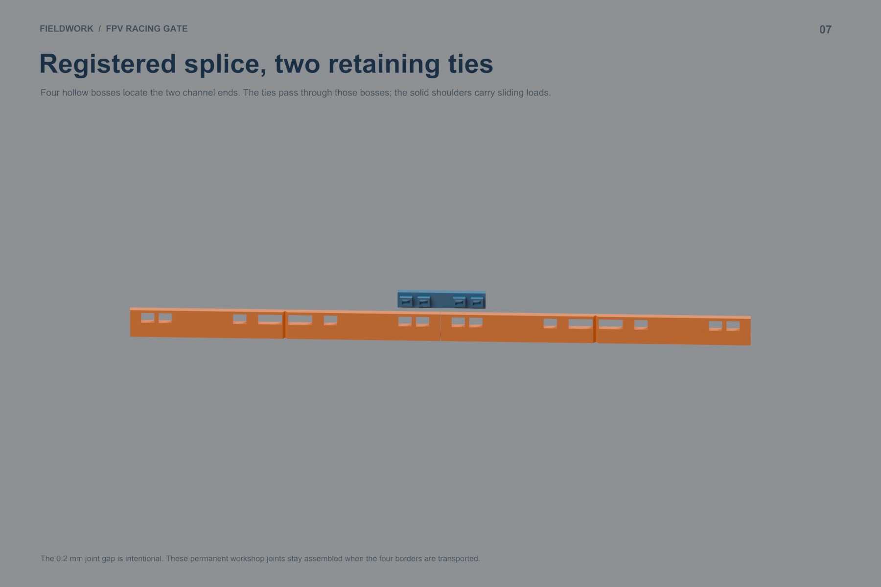
output/a1_full_size/renders/07_CHANNEL_JOINT.png
