rboyd/fpv-drone-racing-gate/output/a1_full_size/renders/08_SNAP_RELEASE.png

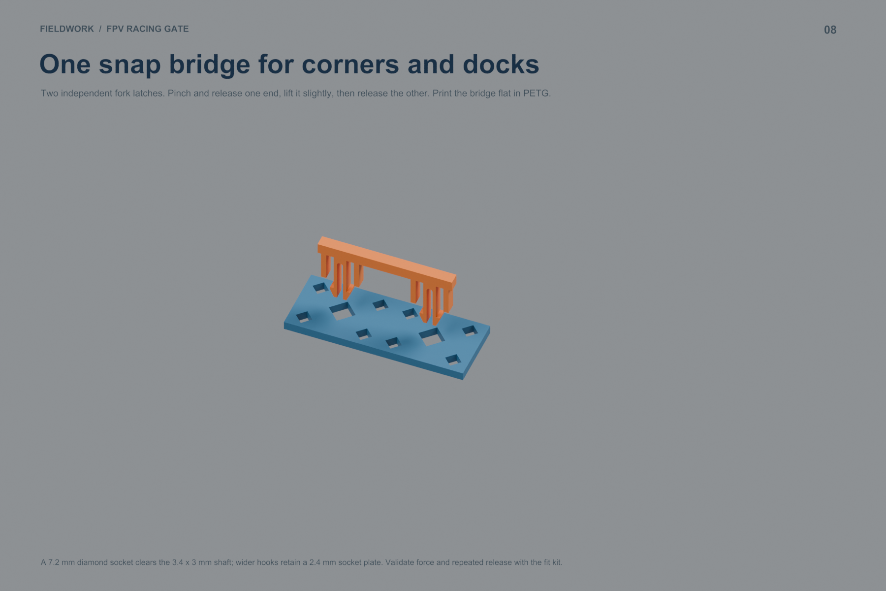
output/a1_full_size/renders/08_SNAP_RELEASE.png
