rboyd/fpv-drone-racing-gate/output/a1_full_size/renders/09_REAR_BAY.png

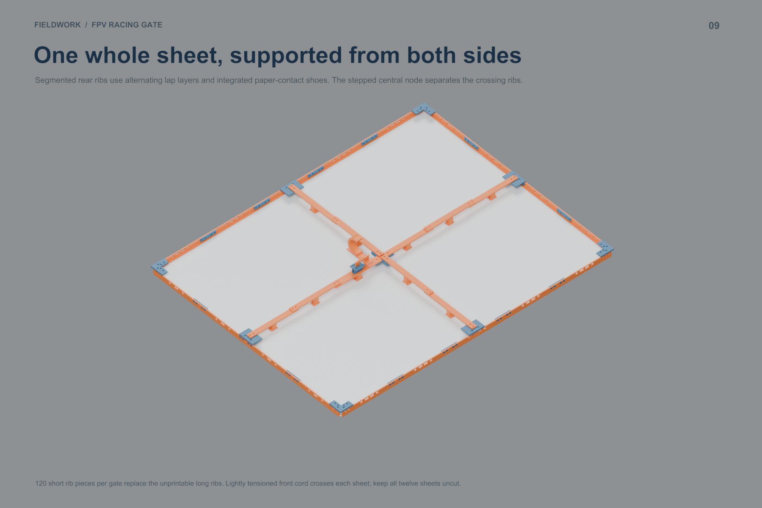
output/a1_full_size/renders/09_REAR_BAY.png
