rboyd/fpv-drone-racing-gate/output/a1_full_size/renders/10_DOCK_AND_BRACE.png

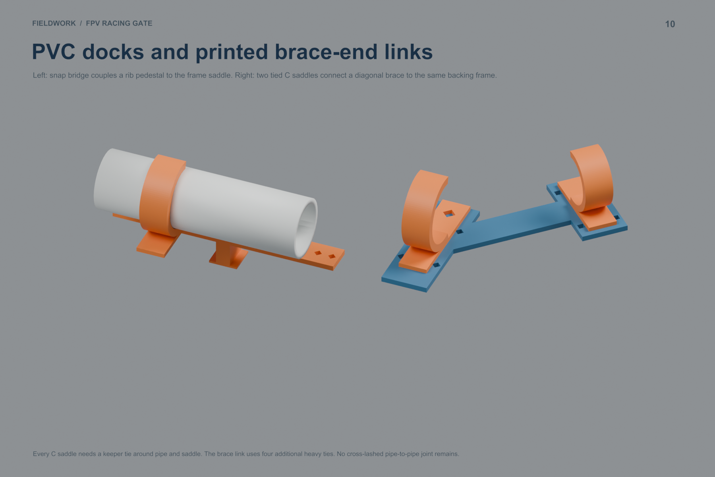
output/a1_full_size/renders/10_DOCK_AND_BRACE.png
