rboyd/fpv-drone-racing-gate/output/drone_clearance_study/renders/02_CURRENT_CLEARANCE.png

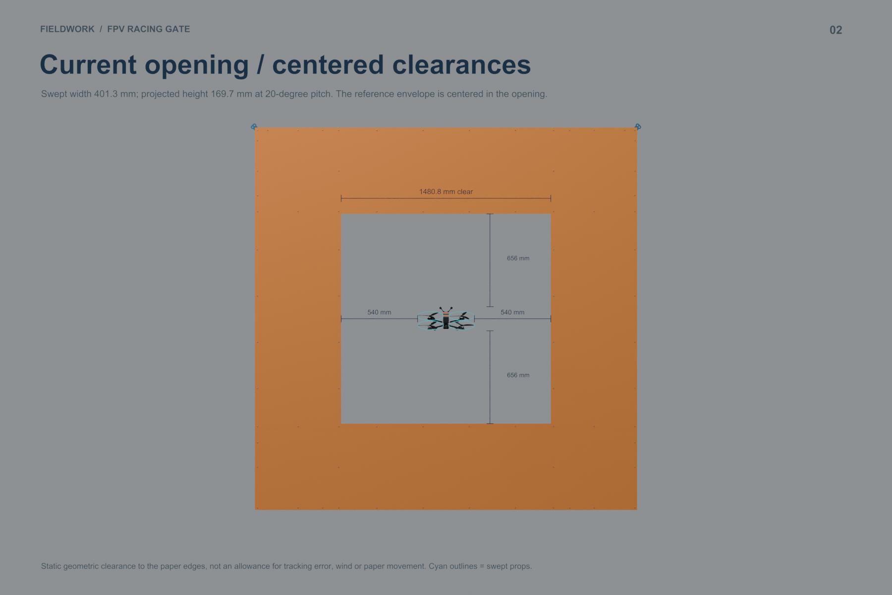
output/drone_clearance_study/renders/02_CURRENT_CLEARANCE.png
