rboyd/fpv-drone-racing-gate/output/drone_clearance_study/renders/05_DRONE_REFERENCE.png

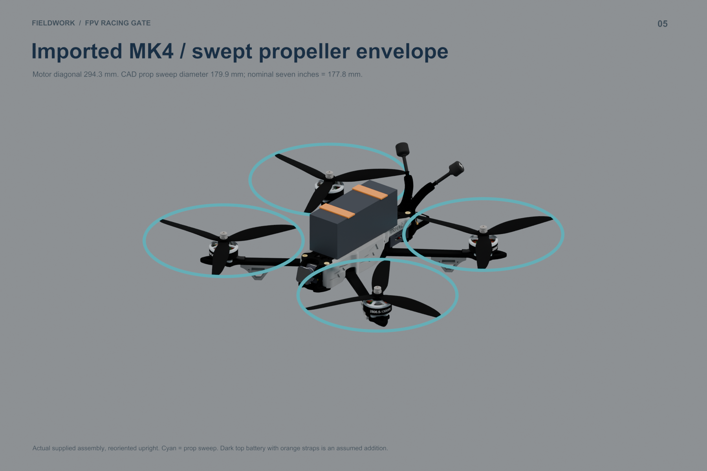
output/drone_clearance_study/renders/05_DRONE_REFERENCE.png
