rboyd/fpv-drone-racing-gate/output/drone_clearance_study/renders/06_SMALLER_GATE_PASS.png

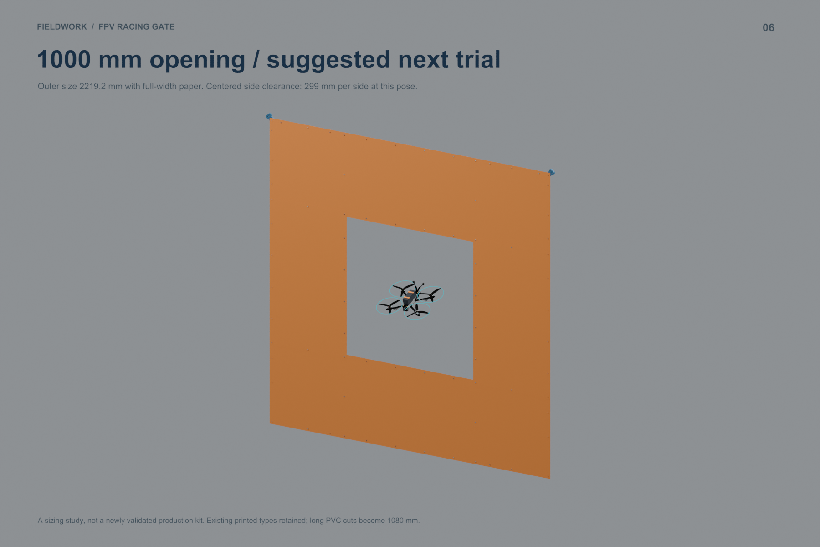
output/drone_clearance_study/renders/06_SMALLER_GATE_PASS.png
