rboyd/fpv-drone-racing-gate/output/dual_guy_gate/renders/01_DUAL_GUY_PART.png

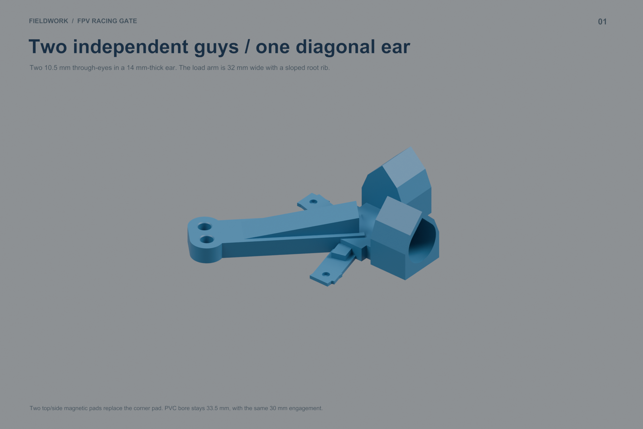
output/dual_guy_gate/renders/01_DUAL_GUY_PART.png
