rboyd/fpv-drone-racing-gate/output/dual_guy_gate/renders/02_FRONT_AND_REAR.png

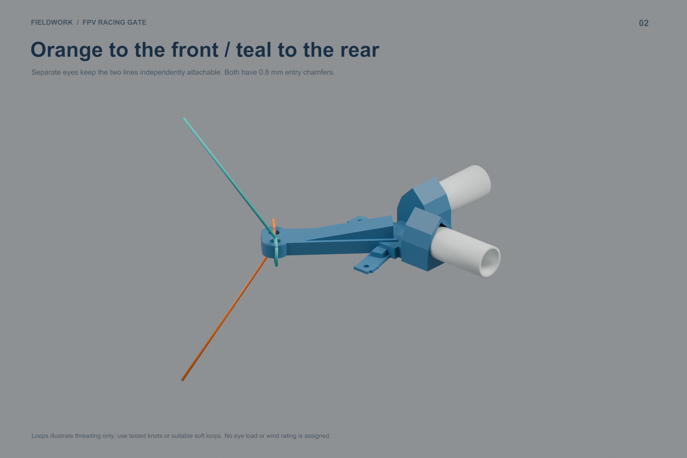
output/dual_guy_gate/renders/02_FRONT_AND_REAR.png
