rboyd/fpv-drone-racing-gate/output/dual_guy_gate/renders/03_PAPER_FRONT.png

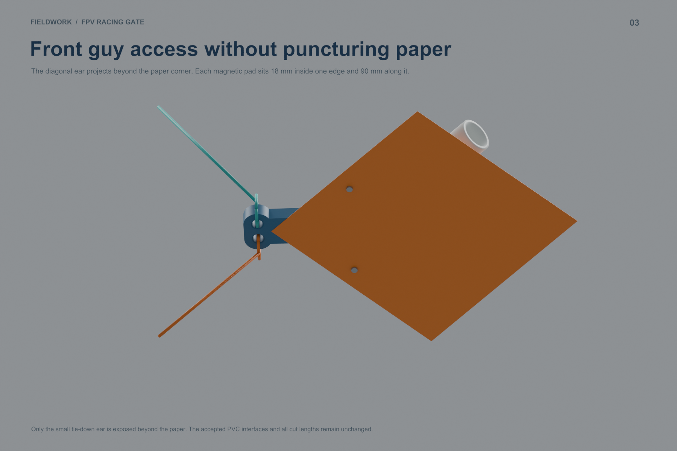
output/dual_guy_gate/renders/03_PAPER_FRONT.png
