rboyd/fpv-drone-racing-gate/output/dual_guy_gate/renders/04_PAPER_REAR.png

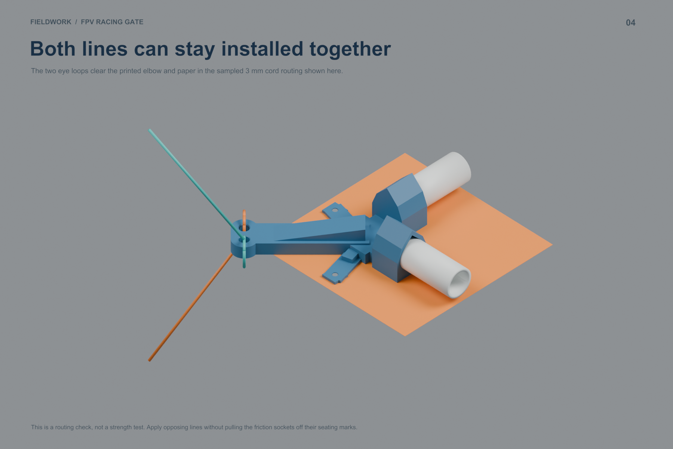
output/dual_guy_gate/renders/04_PAPER_REAR.png
