rboyd/fpv-drone-racing-gate/output/dual_guy_gate/renders/05_SINGLE_FRONT.png

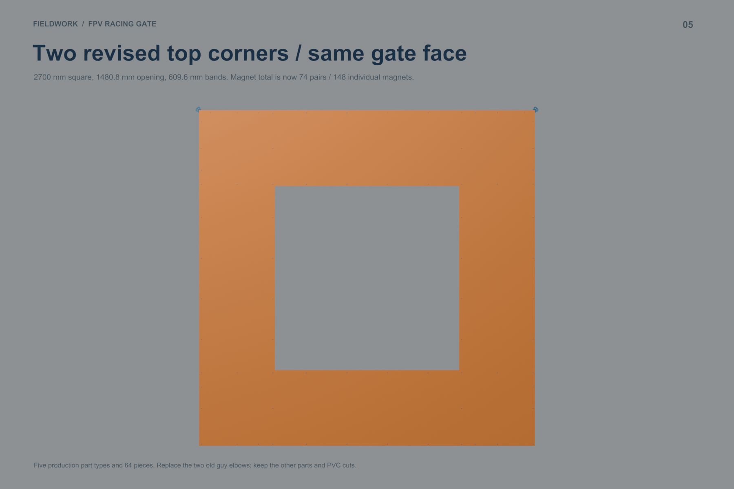
output/dual_guy_gate/renders/05_SINGLE_FRONT.png
