rboyd/fpv-drone-racing-gate/output/dual_guy_gate/renders/07_A1_MINI_PLATE.png

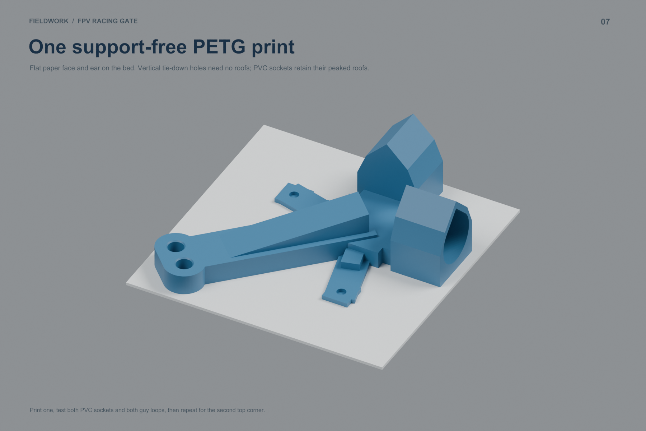
output/dual_guy_gate/renders/07_A1_MINI_PLATE.png
