rboyd/fpv-drone-racing-gate/output/full_width_demo/renders/01_FULL_WIDTH_FRAME.png

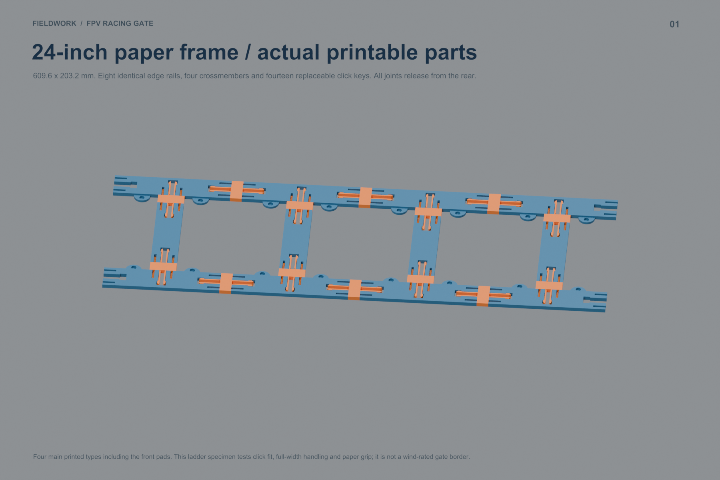
output/full_width_demo/renders/01_FULL_WIDTH_FRAME.png
