rboyd/fpv-drone-racing-gate/output/full_width_demo/renders/02_PAPER_AND_MAGNETS.png

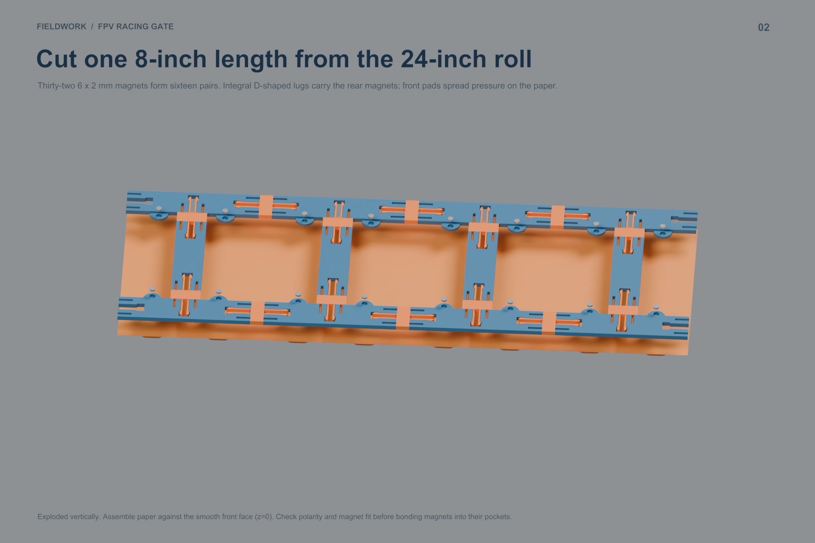
output/full_width_demo/renders/02_PAPER_AND_MAGNETS.png
