rboyd/fpv-drone-racing-gate/output/orthogonal_pvc_gate/renders/01_SINGLE_FRONT.png

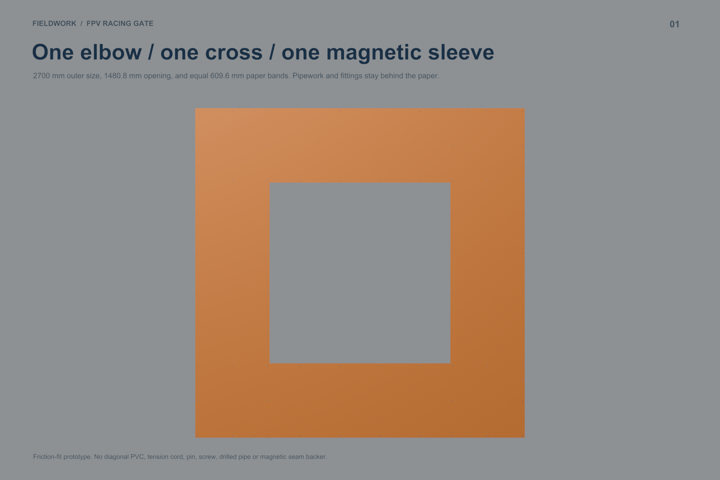
output/orthogonal_pvc_gate/renders/01_SINGLE_FRONT.png
