rboyd/fpv-drone-racing-gate/output/orthogonal_pvc_gate/renders/02_SINGLE_FRAME.png

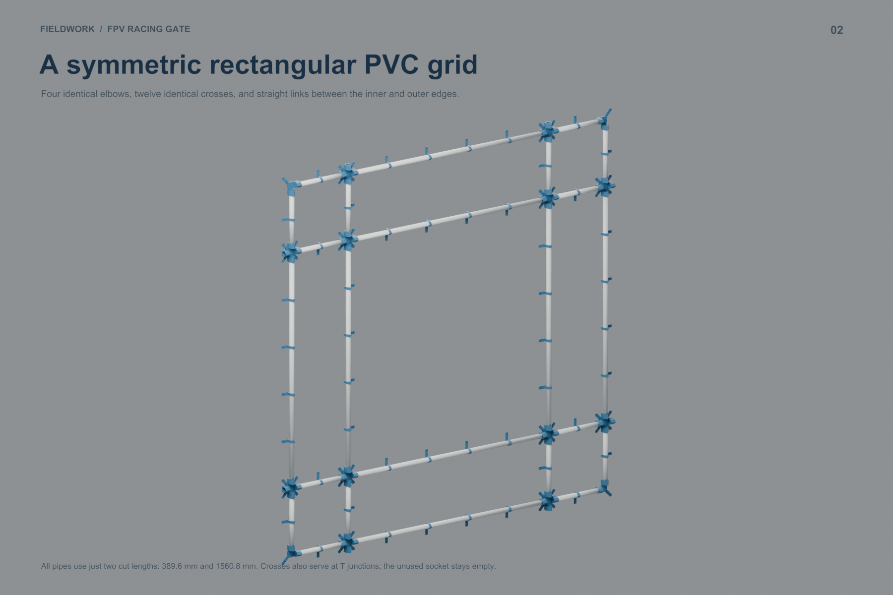
output/orthogonal_pvc_gate/renders/02_SINGLE_FRAME.png
