rboyd/fpv-drone-racing-gate/output/orthogonal_pvc_gate/renders/03_SPLIT_S_FRONT.png

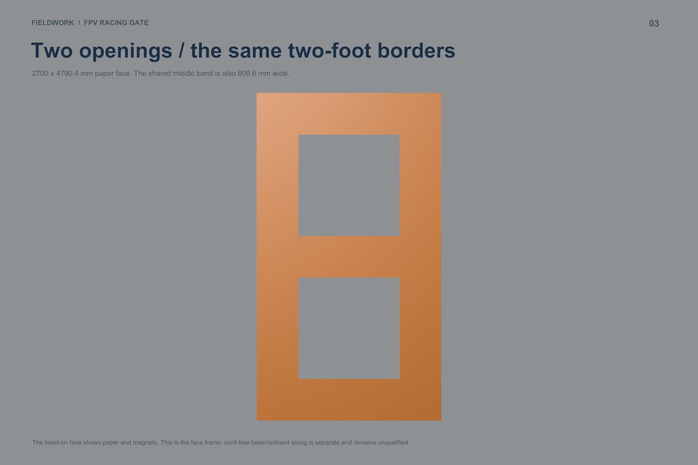
output/orthogonal_pvc_gate/renders/03_SPLIT_S_FRONT.png
