rboyd/fpv-drone-racing-gate/output/orthogonal_pvc_gate/renders/05_THREE_PART_TYPES.png

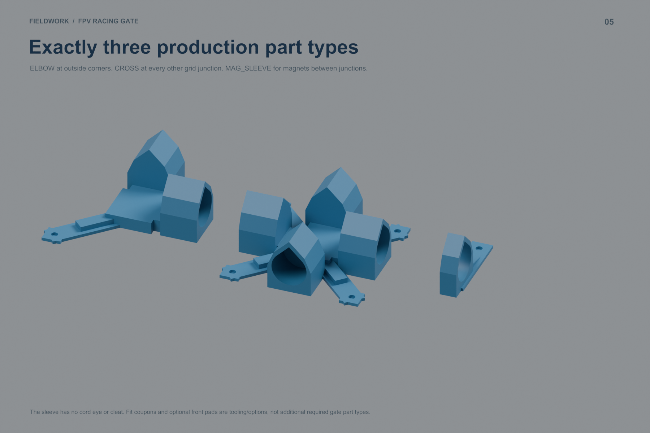
output/orthogonal_pvc_gate/renders/05_THREE_PART_TYPES.png
