rboyd/fpv-drone-racing-gate/output/orthogonal_pvc_gate/renders/06_ELBOW_CROSS_DETAIL.png

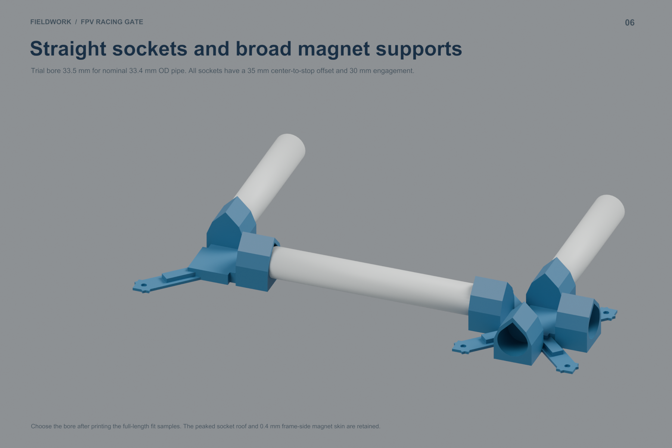
output/orthogonal_pvc_gate/renders/06_ELBOW_CROSS_DETAIL.png
