rboyd/fpv-drone-racing-gate/output/orthogonal_pvc_gate/renders/07_SLEEVE_AND_PAPER.png

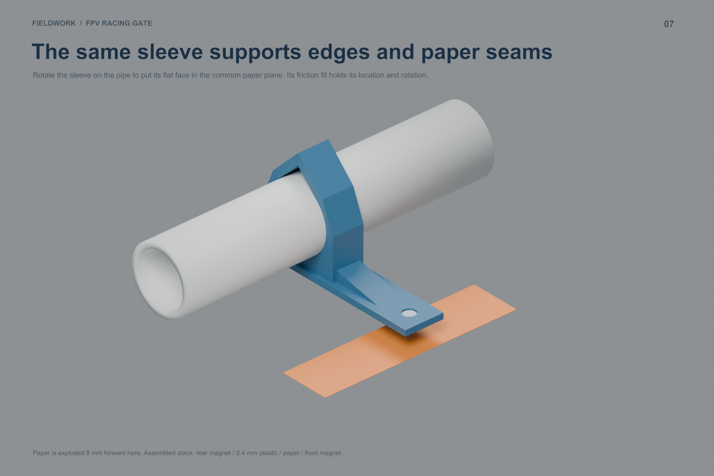
output/orthogonal_pvc_gate/renders/07_SLEEVE_AND_PAPER.png
