rboyd/fpv-drone-racing-gate/output/orthogonal_pvc_gate/renders/08_FIRST_FRICTION_FIT.png

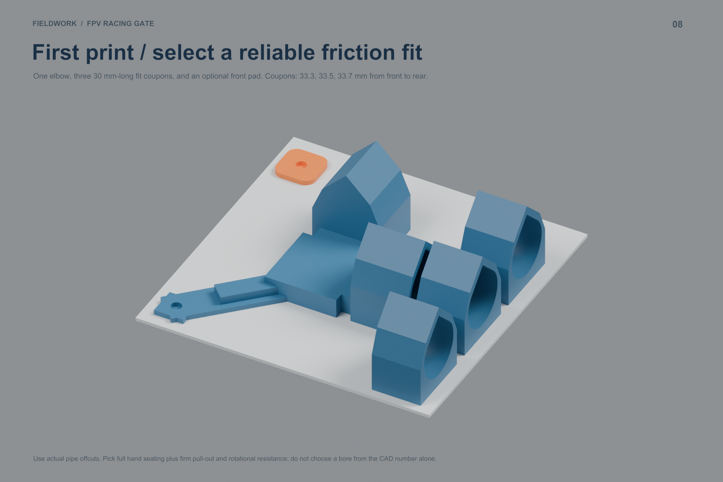
output/orthogonal_pvc_gate/renders/08_FIRST_FRICTION_FIT.png
