rboyd/fpv-drone-racing-gate/output/orthogonal_pvc_gate/renders/09_SHARED_MIDDLE.png

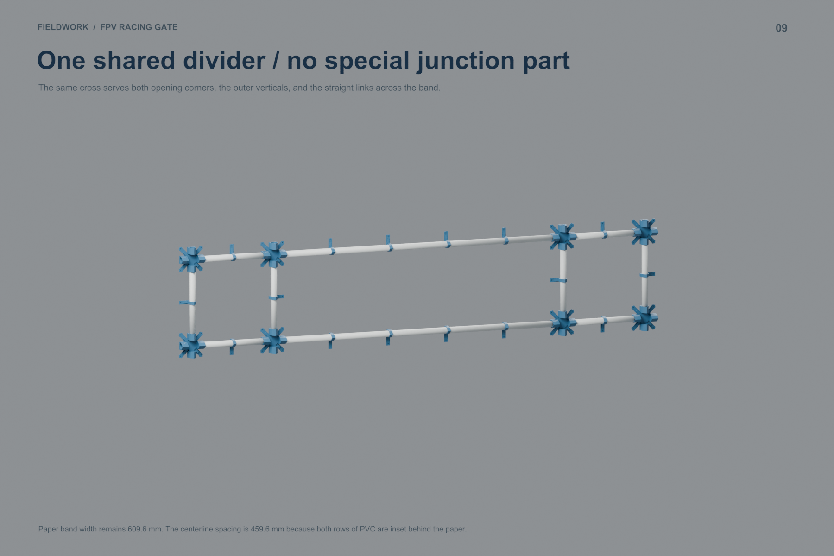
output/orthogonal_pvc_gate/renders/09_SHARED_MIDDLE.png
