rboyd/fpv-drone-racing-gate/output/pvc_paper_gate/renders/10_SPLIT_S_ANCHORING.png

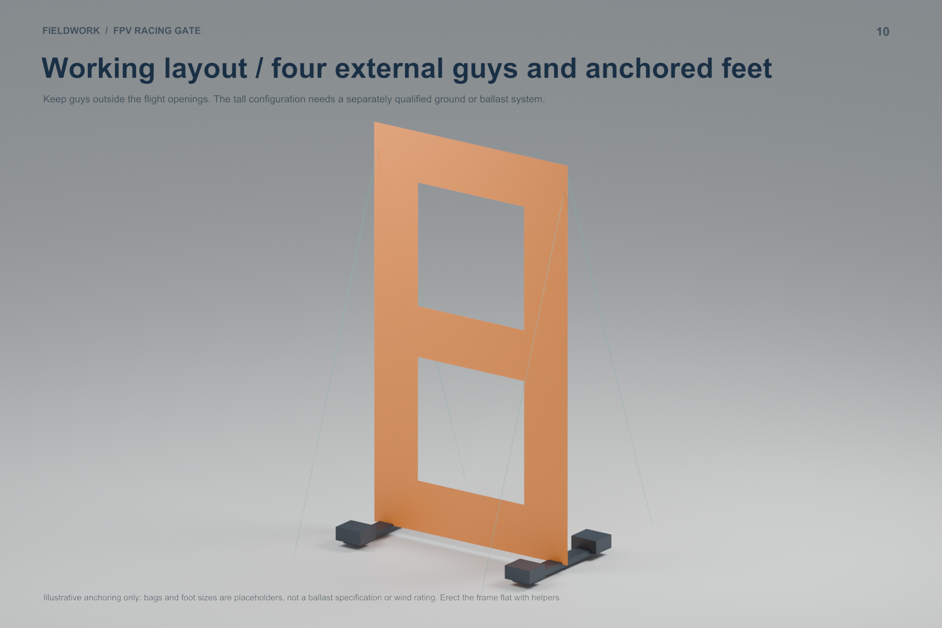
output/pvc_paper_gate/renders/10_SPLIT_S_ANCHORING.png
