rboyd/fpv-drone-racing-gate/output/renders/02_REAR_STRUCTURE.png

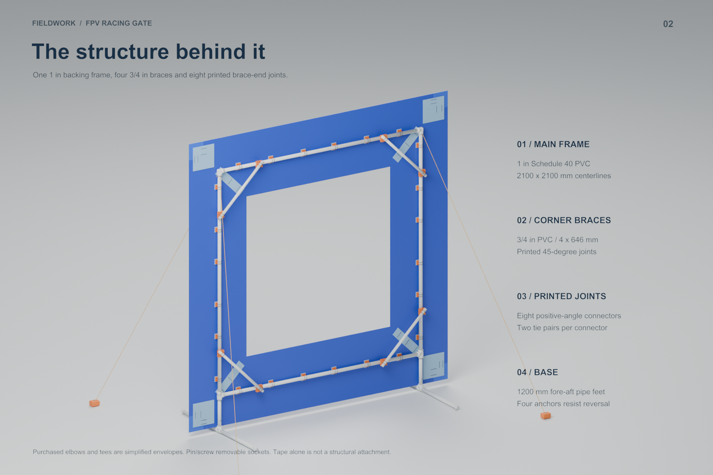
output/renders/02_REAR_STRUCTURE.png
