rboyd/fpv-drone-racing-gate/output/renders/03_EXPLODED.png

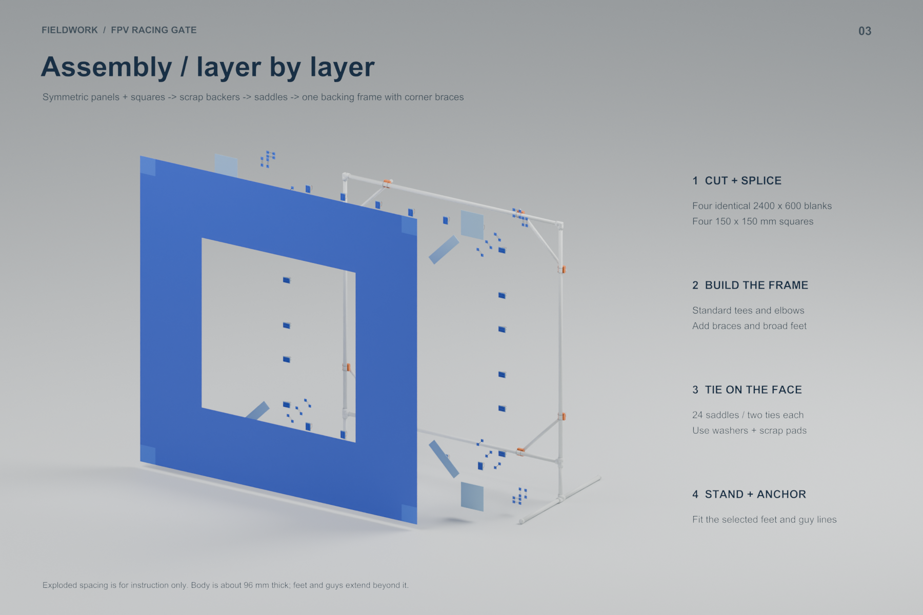
output/renders/03_EXPLODED.png
