rboyd/fpv-drone-racing-gate/output/renders/04_SHEET_LAYOUT.png

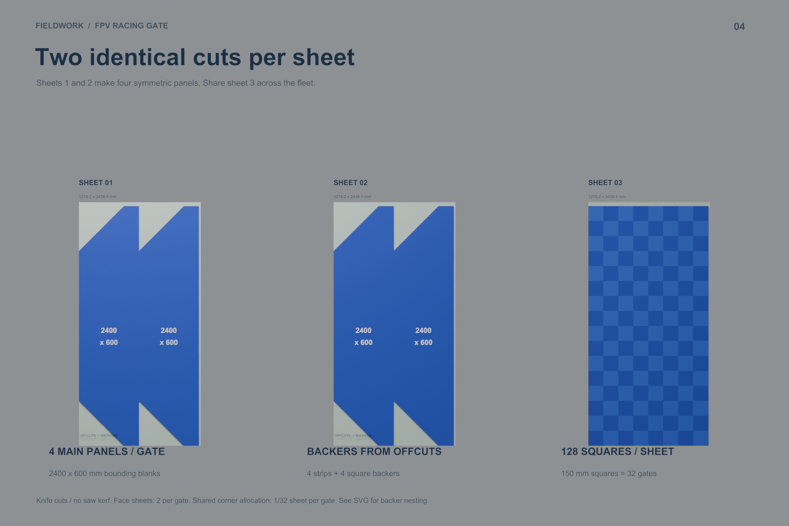
output/renders/04_SHEET_LAYOUT.png
