rboyd/fpv-drone-racing-gate/output/renders/05_CLIP_DETAIL.png

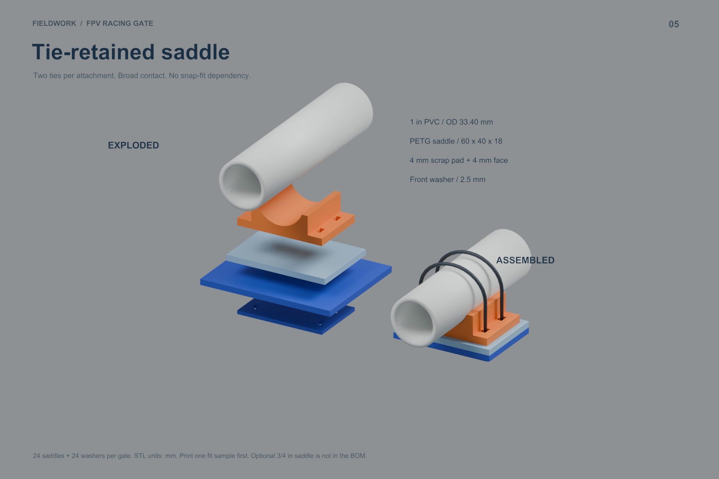
output/renders/05_CLIP_DETAIL.png
