rboyd/fpv-drone-racing-gate/output/renders/06_DIMENSIONS.png

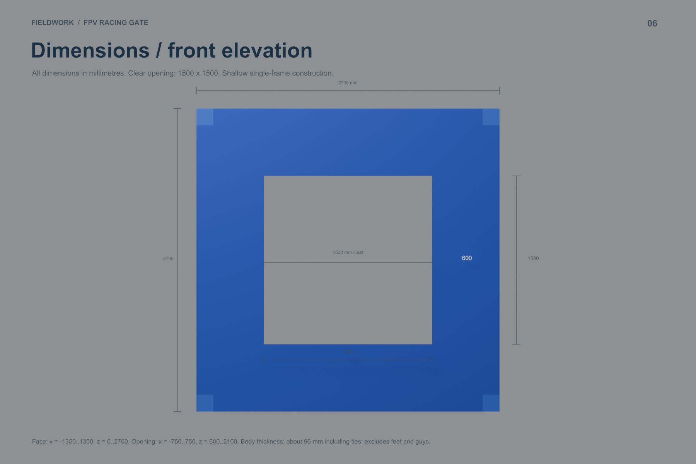
output/renders/06_DIMENSIONS.png
