rboyd/fpv-drone-racing-gate/output/renders/07_HARD_SURFACE.png

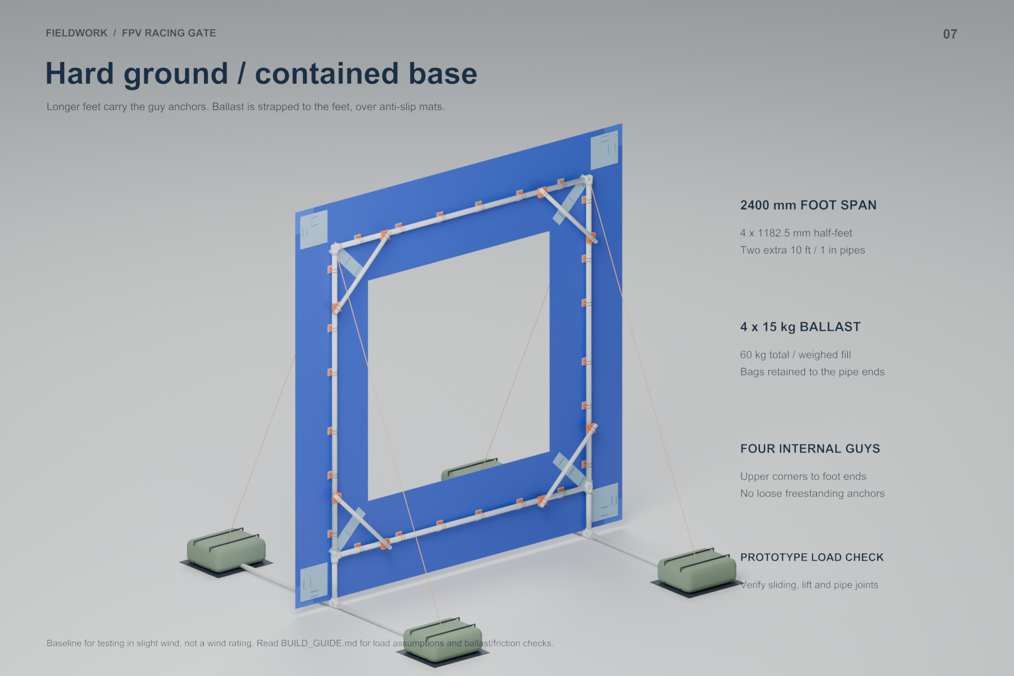
output/renders/07_HARD_SURFACE.png
