rboyd/fpv-drone-racing-gate/output/renders/08_BRACE_JOINT.png

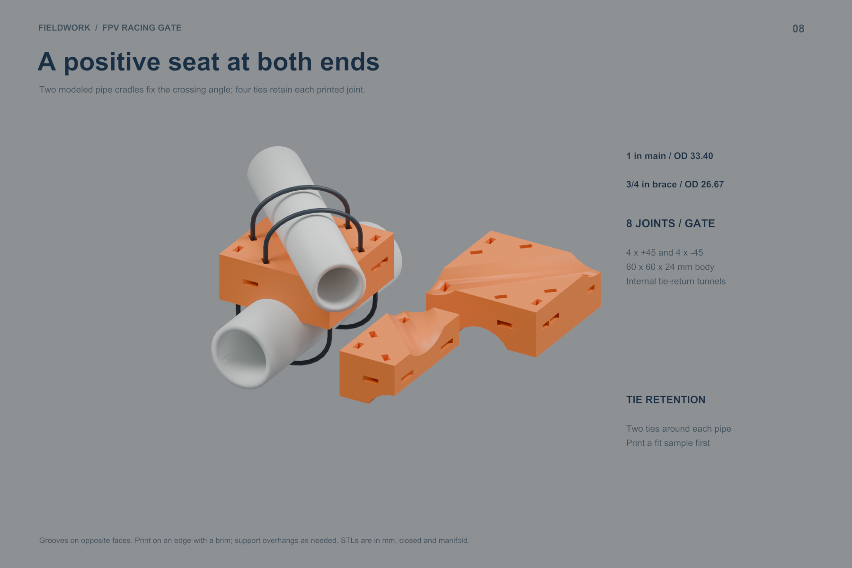
output/renders/08_BRACE_JOINT.png
