rboyd/fpv-drone-racing-gate/output/renders/10_CUTTING_JIGS.png

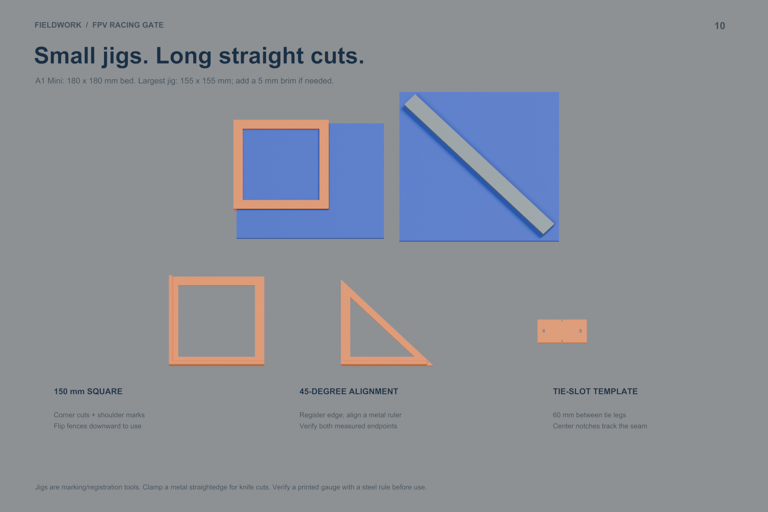
output/renders/10_CUTTING_JIGS.png
