rboyd/fpv-drone-racing-gate/output/rigid_whole_sheet/renders/01_RIGID_GATE.png

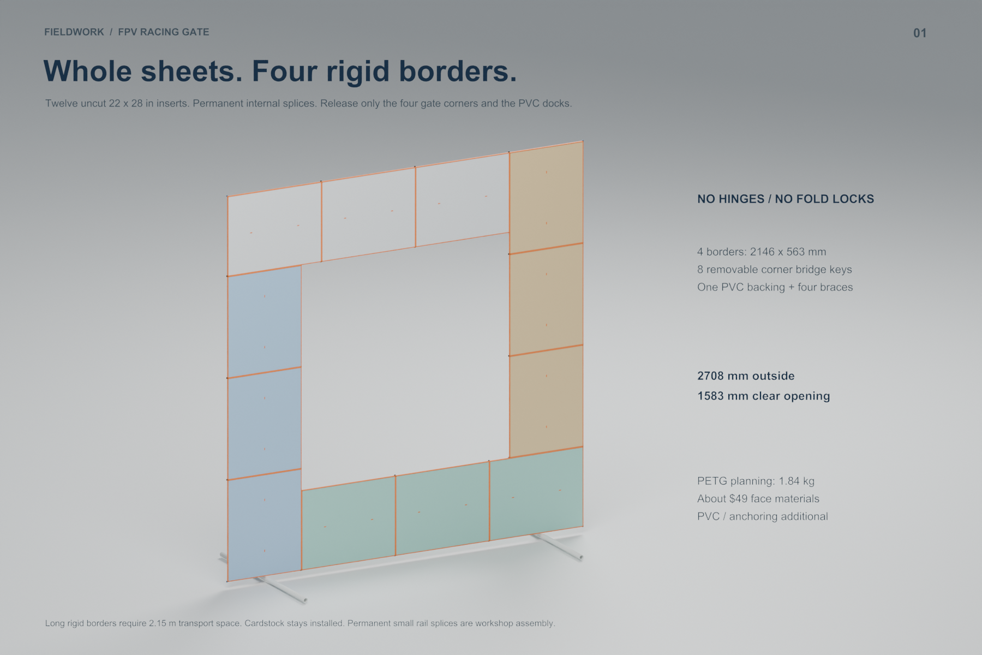
output/rigid_whole_sheet/renders/01_RIGID_GATE.png
