rboyd/fpv-drone-racing-gate/output/rigid_whole_sheet/renders/02_FOUR_RIGID_BORDERS.png

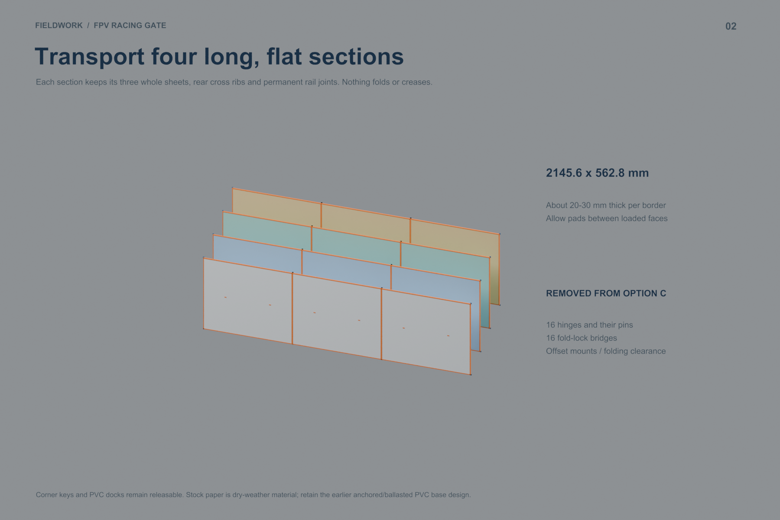
output/rigid_whole_sheet/renders/02_FOUR_RIGID_BORDERS.png
