rboyd/fpv-drone-racing-gate/output/rigid_whole_sheet/renders/03_RIGID_SPLICES.png

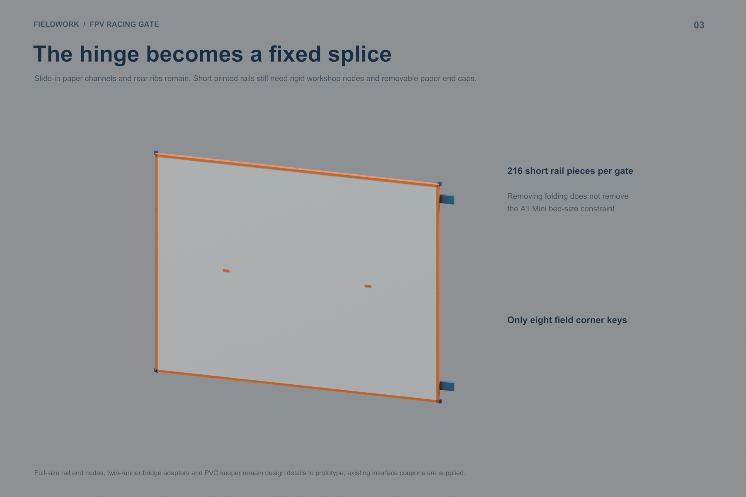
output/rigid_whole_sheet/renders/03_RIGID_SPLICES.png
