rboyd/fpv-drone-racing-gate/output/sleeve_paper_gate/renders/03_ONE_BORDER.png

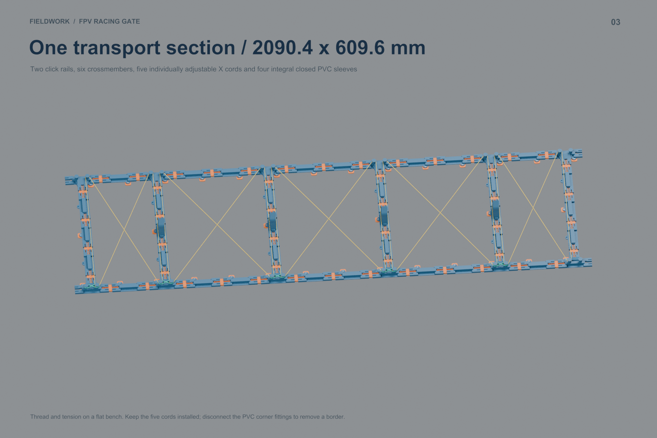
output/sleeve_paper_gate/renders/03_ONE_BORDER.png
