rboyd/fpv-drone-racing-gate/output/tee_pvc_gate/renders/01_SINGLE_FRONT.png

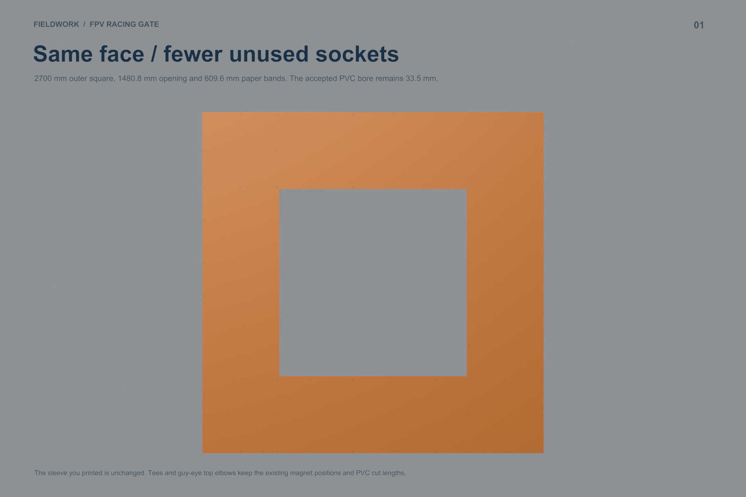
output/tee_pvc_gate/renders/01_SINGLE_FRONT.png
