rboyd/fpv-drone-racing-gate/output/tee_pvc_gate/renders/02_SINGLE_FRAME.png

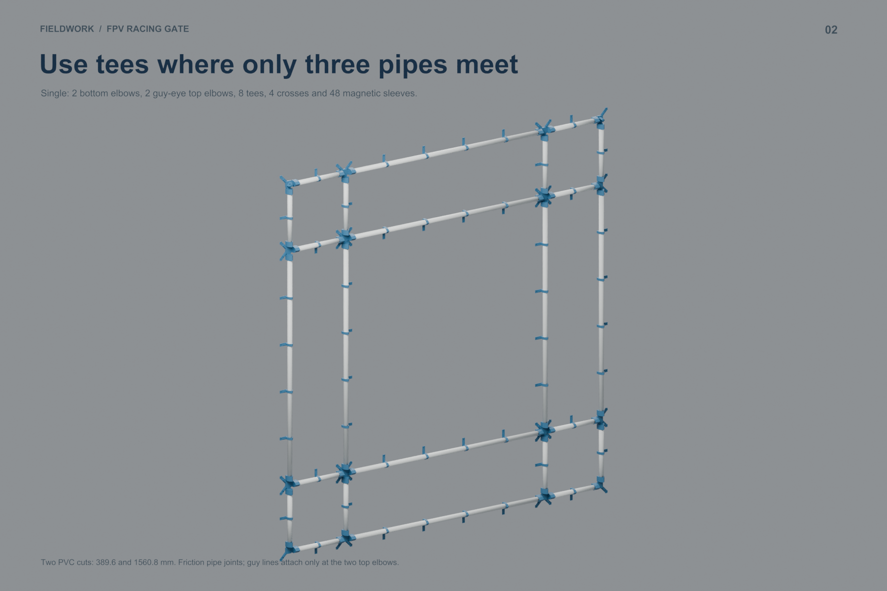
output/tee_pvc_gate/renders/02_SINGLE_FRAME.png
