rboyd/fpv-drone-racing-gate/output/tee_pvc_gate/renders/05_PART_FAMILY.png

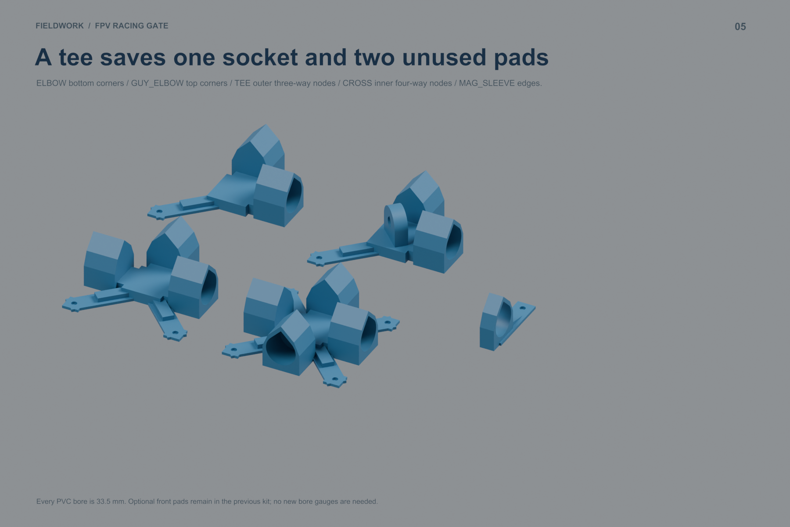
output/tee_pvc_gate/renders/05_PART_FAMILY.png
