rboyd/fpv-drone-racing-gate/output/tee_pvc_gate/renders/06_TEE_DETAIL.png

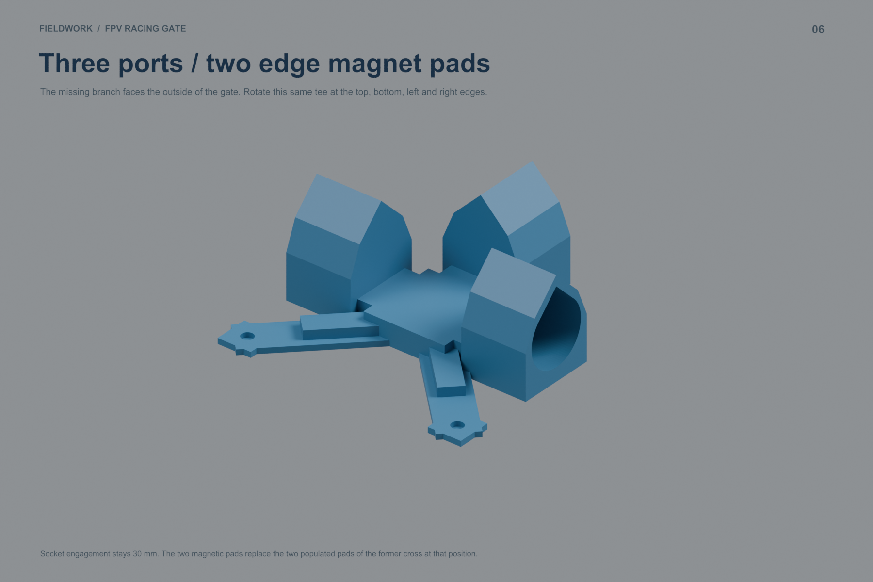
output/tee_pvc_gate/renders/06_TEE_DETAIL.png
