rboyd/fpv-drone-racing-gate/output/tee_pvc_gate/renders/07_GUY_ELBOW.png

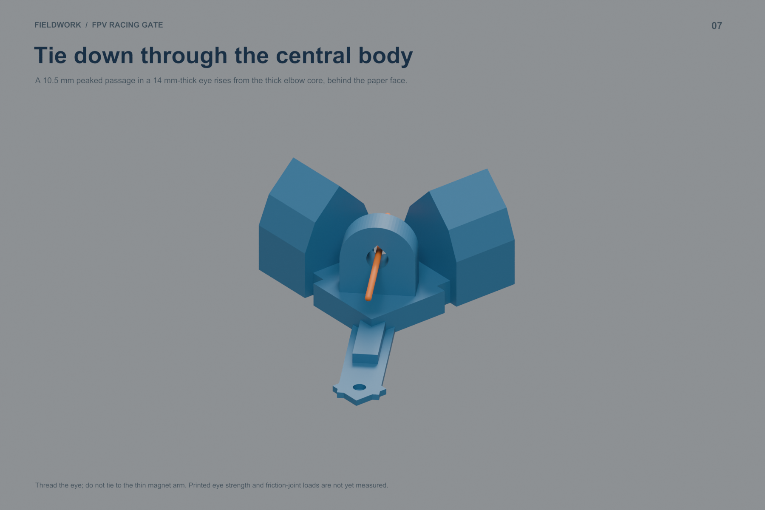
output/tee_pvc_gate/renders/07_GUY_ELBOW.png
