rboyd/fpv-drone-racing-gate/output/tee_pvc_gate/renders/08_MEASURING_HEADS.png

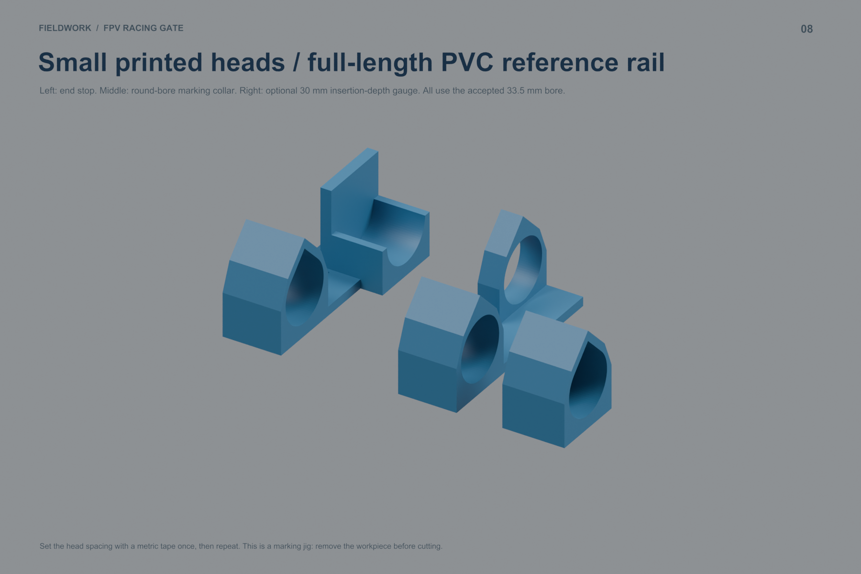
output/tee_pvc_gate/renders/08_MEASURING_HEADS.png
