rboyd/fpv-drone-racing-gate/output/tee_pvc_gate/renders/09_LONG_LENGTH_JIG.png

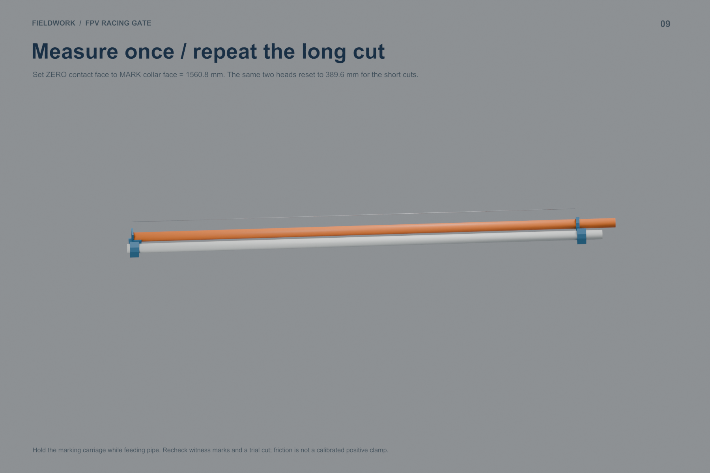
output/tee_pvc_gate/renders/09_LONG_LENGTH_JIG.png
