rboyd/fpv-drone-racing-gate/output/tee_pvc_gate/renders/10_JIG_DATUM_DETAIL.png

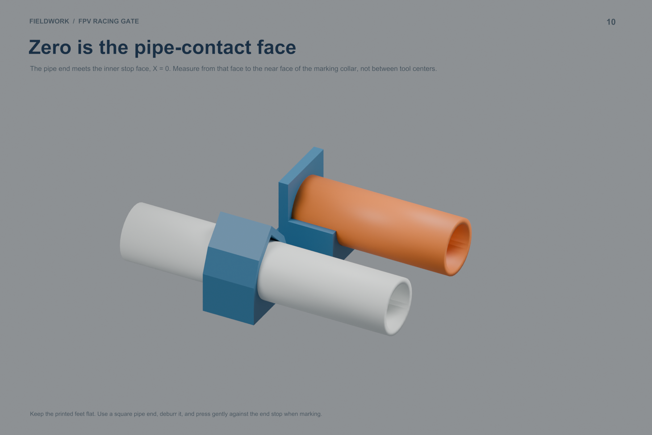
output/tee_pvc_gate/renders/10_JIG_DATUM_DETAIL.png
