rboyd/fpv-drone-racing-gate/output/tee_pvc_gate/renders/11_MEASURING_KIT.png

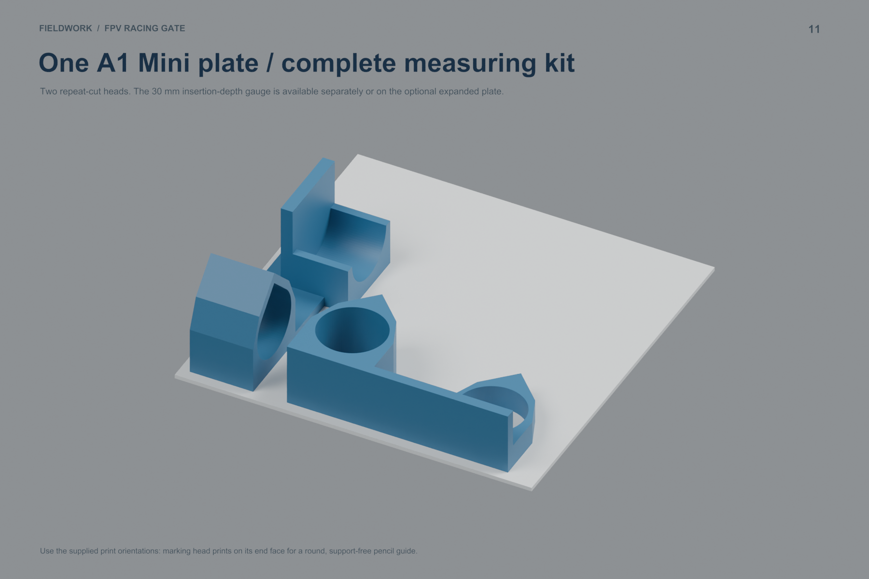
output/tee_pvc_gate/renders/11_MEASURING_KIT.png
