rboyd/fpv-drone-racing-gate/output/a1_full_size/MINIMAL_TEST_PARTS.csv

part | quantity
CHANNEL_LONG | 1
CHANNEL_SHORT | 1
SPLINT | 1
SNAP_BRIDGE | 1
DOCK_CAP | 1
PIPE_33 | 1
CORNER_NODE | 1
DOCK_PEDESTAL | 1
RIB_H_LOW_DOCK | 1
