rboyd/fpv-drone-racing-gate/output/a1_full_size/renders/02_PRINT_PARTS_1.png

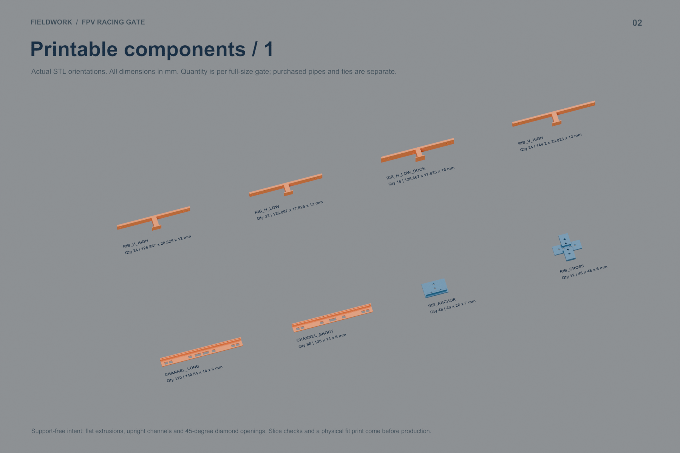
output/a1_full_size/renders/02_PRINT_PARTS_1.png
