rboyd/fpv-drone-racing-gate/output/a1_full_size/renders/03_PRINT_PARTS_2.png

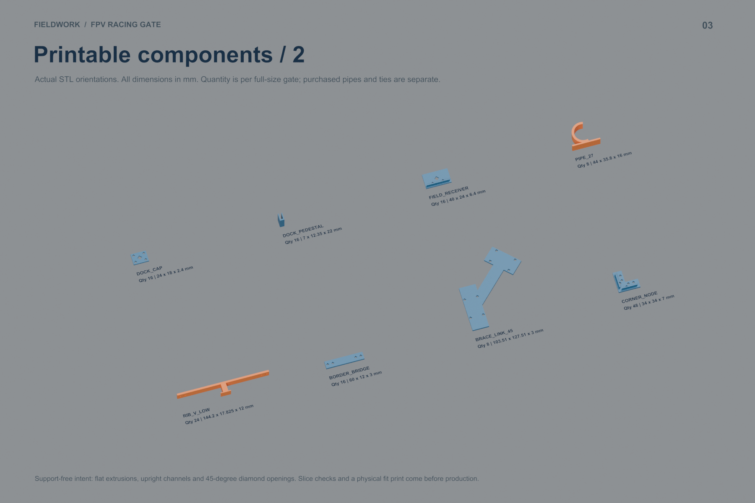
output/a1_full_size/renders/03_PRINT_PARTS_2.png
