rboyd/fpv-drone-racing-gate/output/a1_full_size/renders/04_PRINT_PARTS_3.png

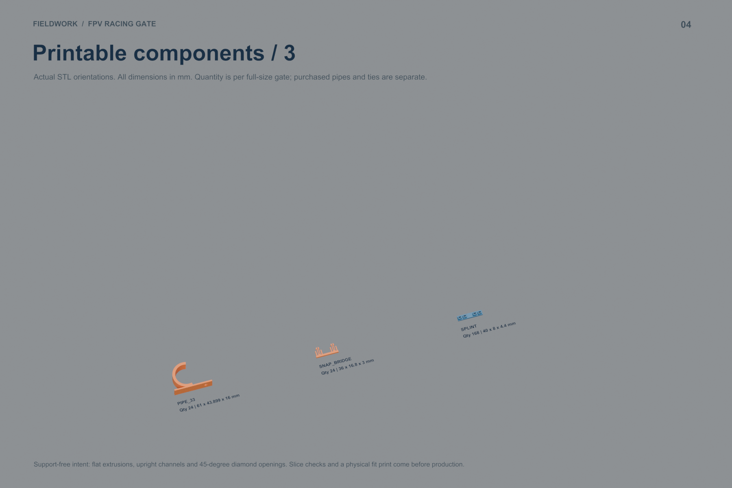
output/a1_full_size/renders/04_PRINT_PARTS_3.png
