rboyd/fpv-drone-racing-gate/output/full_paper_gate/printable/Q_CLICK_KEY_FULL.3mf

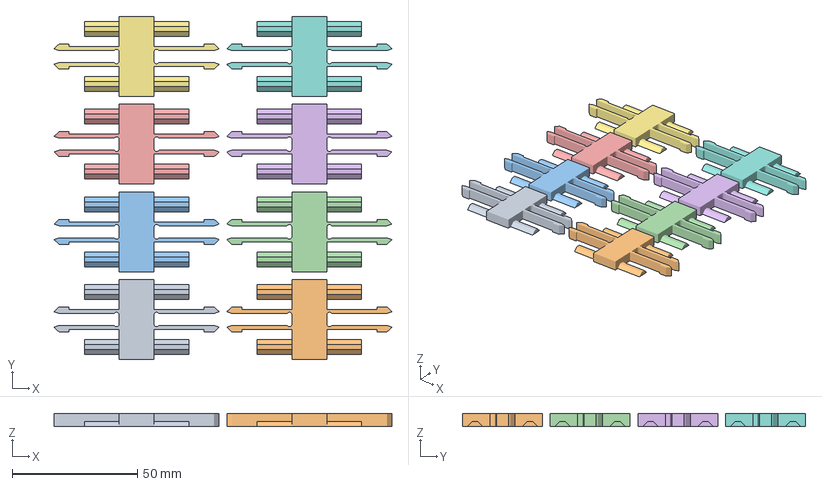
[picture p131: CAD file, 2026-09-18]
output/full_paper_gate/printable/Q_CLICK_KEY_FULL.3mf
135.0 x 137.0 x 5.00 mm
CLICK_KEY x 8
