rboyd/fpv-drone-racing-gate/output/a1_full_size/printable/RIB_H_HIGH.3mf

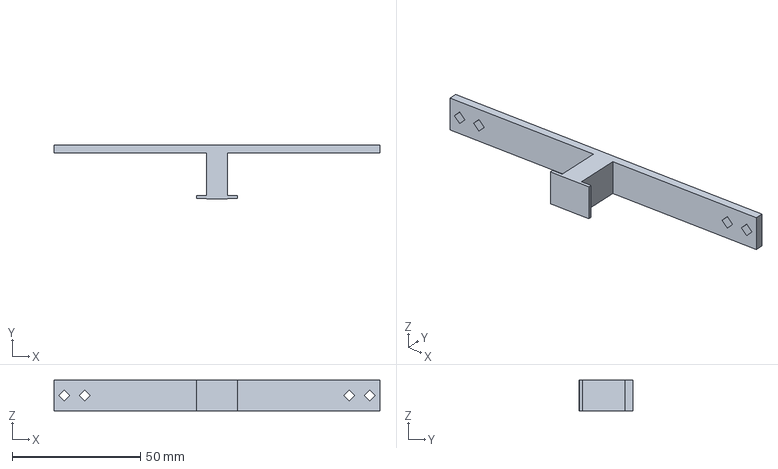
[picture p132: CAD file, 2026-09-18]
output/a1_full_size/printable/RIB_H_HIGH.3mf
126.9 x 20.8 x 12.0 mm
