rboyd/fpv-drone-racing-gate/output/a1_full_size/sliced/BORDER_BRIDGE/BORDER_BRIDGE_A1Mini_PETG.3mf

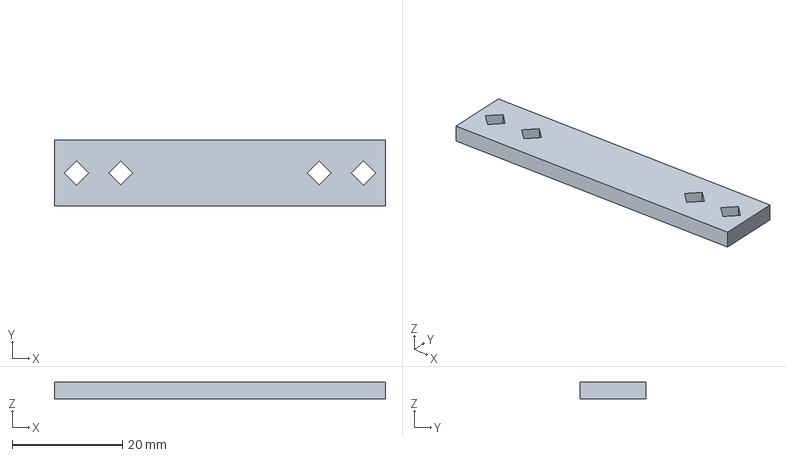
[picture p133: CAD file, 2026-09-18]
output/a1_full_size/sliced/BORDER_BRIDGE/BORDER_BRIDGE_A1Mini_PETG.3mf
60.0 x 12.0 x 3.00 mm
