rboyd/fpv-drone-racing-gate/output/a1_full_size/sliced/BRACE_LINK_45/BRACE_LINK_45_A1Mini_PETG.3mf

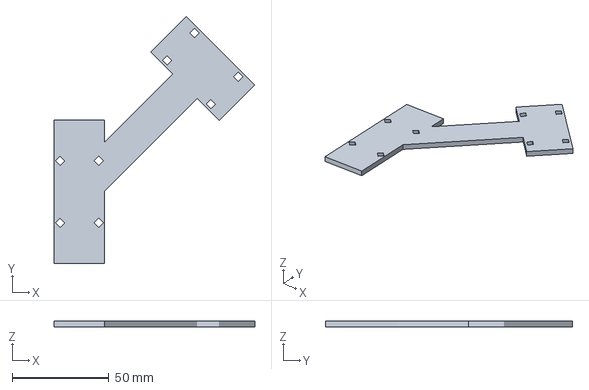
[picture p134: CAD file, 2026-09-18]
output/a1_full_size/sliced/BRACE_LINK_45/BRACE_LINK_45_A1Mini_PETG.3mf
103.5 x 127.5 x 3.00 mm
