rboyd/fpv-drone-racing-gate/output/a1_full_size/sliced/CHANNEL_LONG/CHANNEL_LONG_A1Mini_PETG.3mf

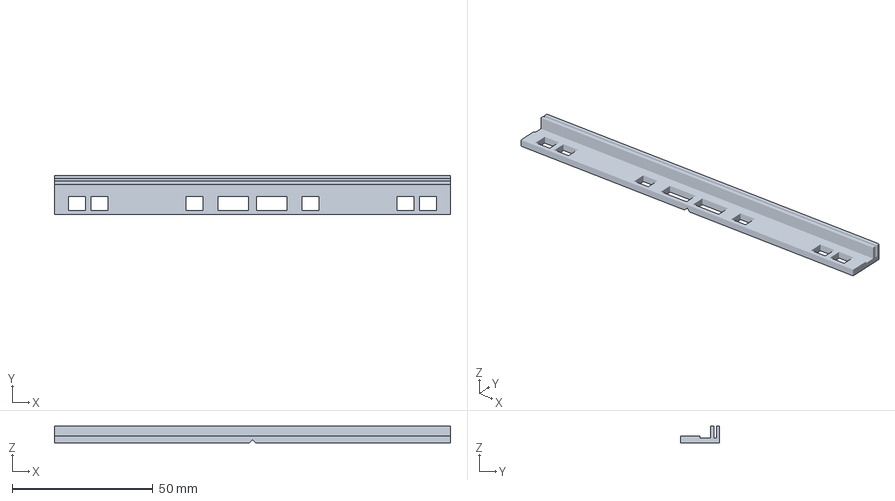
[picture p135: CAD file, 2026-09-18]
output/a1_full_size/sliced/CHANNEL_LONG/CHANNEL_LONG_A1Mini_PETG.3mf
140.8 x 14.0 x 6.00 mm
