rboyd/fpv-drone-racing-gate/output/a1_full_size/sliced/CORNER_NODE/CORNER_NODE_A1Mini_PETG.3mf

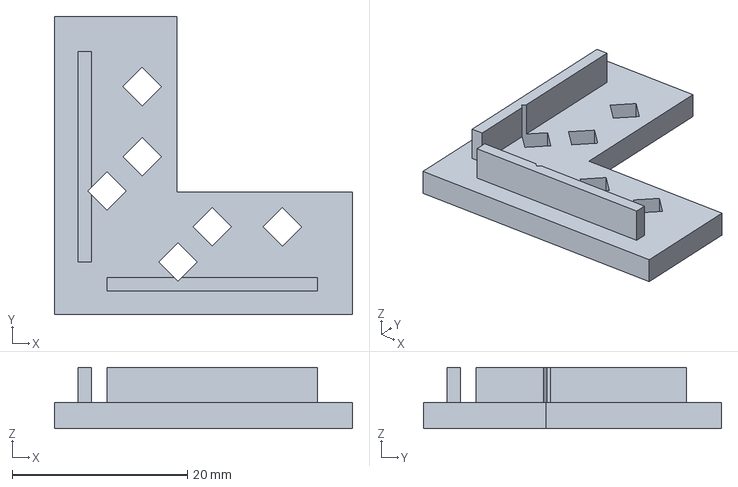
[picture p137: CAD file, 2026-09-18]
output/a1_full_size/sliced/CORNER_NODE/CORNER_NODE_A1Mini_PETG.3mf
34.0 x 34.0 x 7.00 mm
