rboyd/fpv-drone-racing-gate/output/a1_full_size/sliced/DOCK_CAP/DOCK_CAP_A1Mini_PETG.3mf

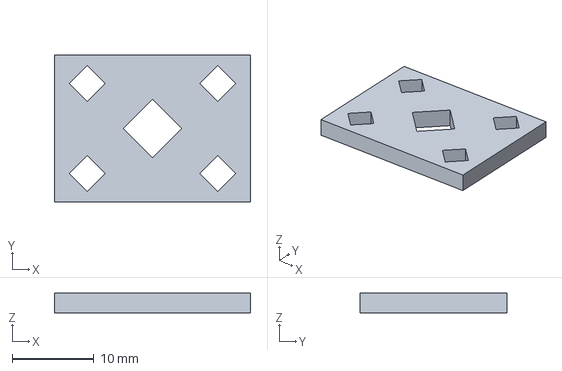
[picture p138: CAD file, 2026-09-18]
output/a1_full_size/sliced/DOCK_CAP/DOCK_CAP_A1Mini_PETG.3mf
24.0 x 18.0 x 2.40 mm
