rboyd/fpv-drone-racing-gate/output/a1_full_size/sliced/DOCK_PEDESTAL/DOCK_PEDESTAL_A1Mini_PETG.3mf

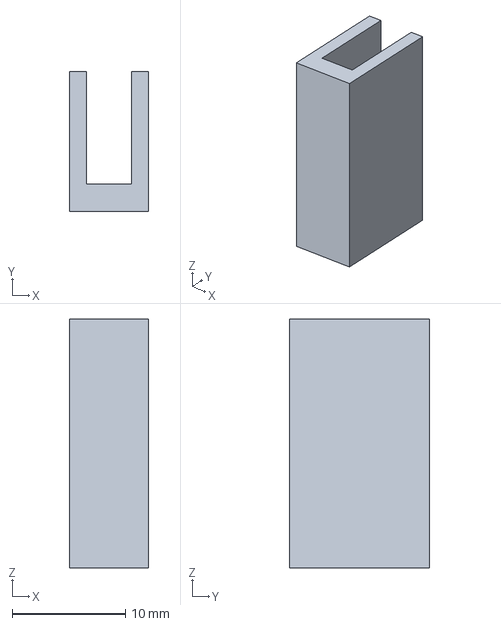
[picture p139: CAD file, 2026-09-18]
output/a1_full_size/sliced/DOCK_PEDESTAL/DOCK_PEDESTAL_A1Mini_PETG.3mf
7.00 x 12.4 x 22.0 mm
