rboyd/fpv-drone-racing-gate/output/a1_full_size/sliced/FIELD_RECEIVER/FIELD_RECEIVER_A1Mini_PETG.3mf

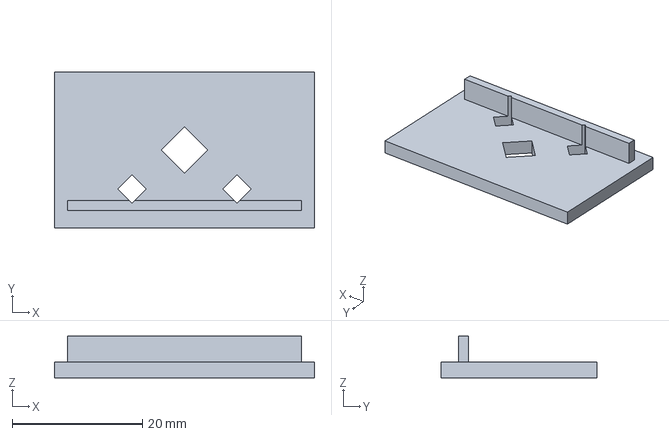
[picture p140: CAD file, 2026-09-18]
output/a1_full_size/sliced/FIELD_RECEIVER/FIELD_RECEIVER_A1Mini_PETG.3mf
40.0 x 24.0 x 6.40 mm
