rboyd/fpv-drone-racing-gate/output/a1_full_size/sliced/Fit_Kit_1to1_LAYOUT/Fit_Kit_1to1_LAYOUT_A1Mini_PETG.3mf

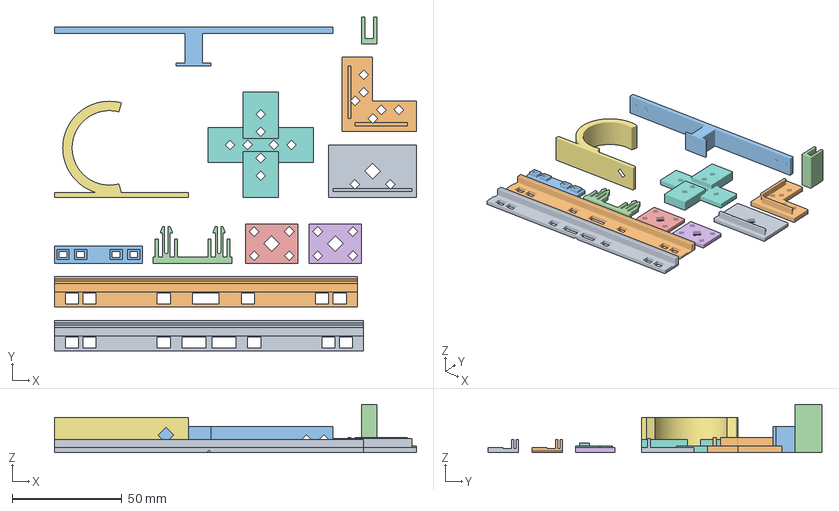
[picture p141: CAD file, 2026-09-18]
output/a1_full_size/sliced/Fit_Kit_1to1_LAYOUT/Fit_Kit_1to1_LAYOUT_A1Mini_PETG.3mf
165.0 x 152.4 x 22.0 mm
CHANNEL_LONG
CHANNEL_SHORT
SPLINT
SNAP_BRIDGE
DOCK_CAP x 2
PIPE_33
RIB_CROSS
FIELD_RECEIVER
CORNER_NODE
RIB_H_LOW
DOCK_PEDESTAL
