rboyd/fpv-drone-racing-gate/output/a1_full_size/sliced/Minimal_Concept_Test_9_Parts/Minimal_Concept_Test_9_Parts_A1Mini_PETG.3mf

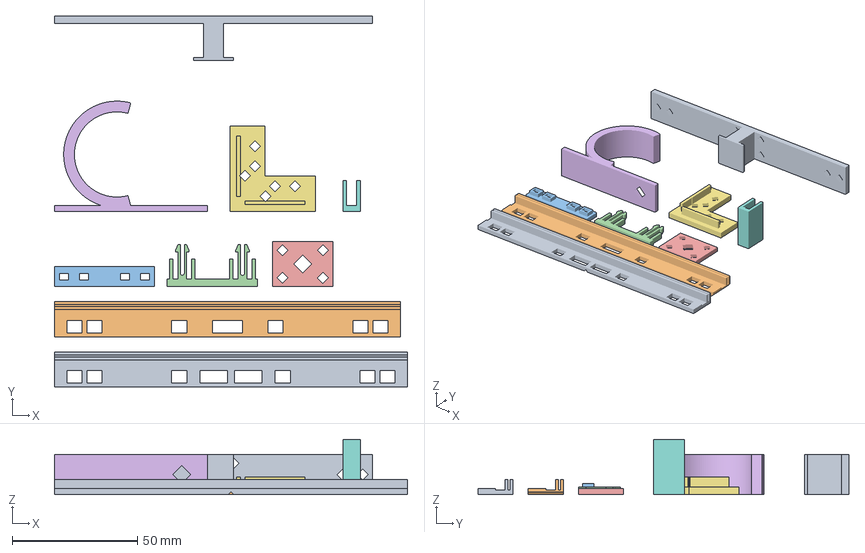
[picture p142: CAD file, 2026-09-18]
output/a1_full_size/sliced/Minimal_Concept_Test_9_Parts/Minimal_Concept_Test_9_Parts_A1Mini_PETG.3mf
140.8 x 147.8 x 22.0 mm
CHANNEL_LONG
CHANNEL_SHORT
SPLINT
SNAP_BRIDGE
DOCK_CAP
PIPE_33
CORNER_NODE
DOCK_PEDESTAL
RIB_H_LOW_DOCK
