rboyd/fpv-drone-racing-gate/output/a1_full_size/sliced/PIPE_27/PIPE_27_A1Mini_PETG.3mf

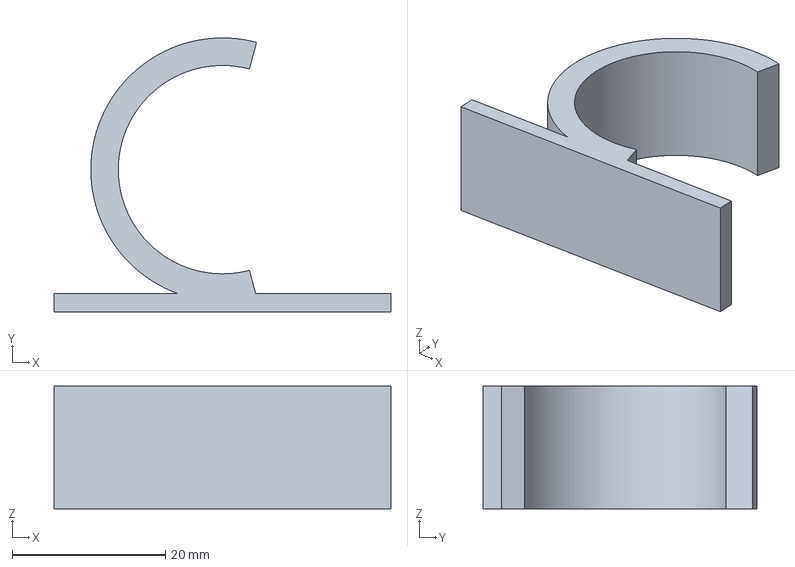
[picture p143: CAD file, 2026-09-18]
output/a1_full_size/sliced/PIPE_27/PIPE_27_A1Mini_PETG.3mf
44.0 x 35.8 x 16.0 mm
