rboyd/fpv-drone-racing-gate/output/a1_full_size/sliced/PIPE_33/PIPE_33_A1Mini_PETG.3mf

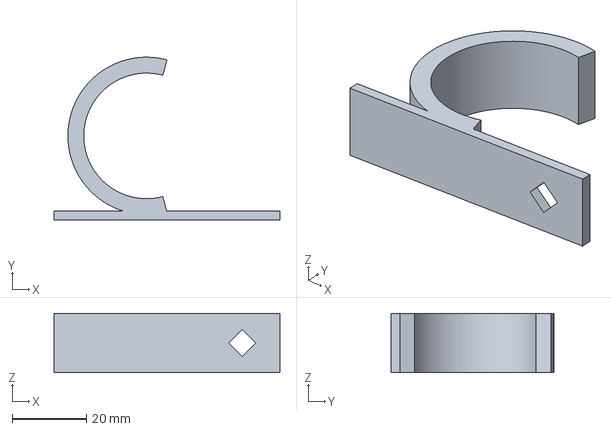
[picture p144: CAD file, 2026-09-18]
output/a1_full_size/sliced/PIPE_33/PIPE_33_A1Mini_PETG.3mf
61.0 x 43.9 x 16.0 mm
