rboyd/fpv-drone-racing-gate/output/a1_full_size/sliced/RIB_ANCHOR/RIB_ANCHOR_A1Mini_PETG.3mf

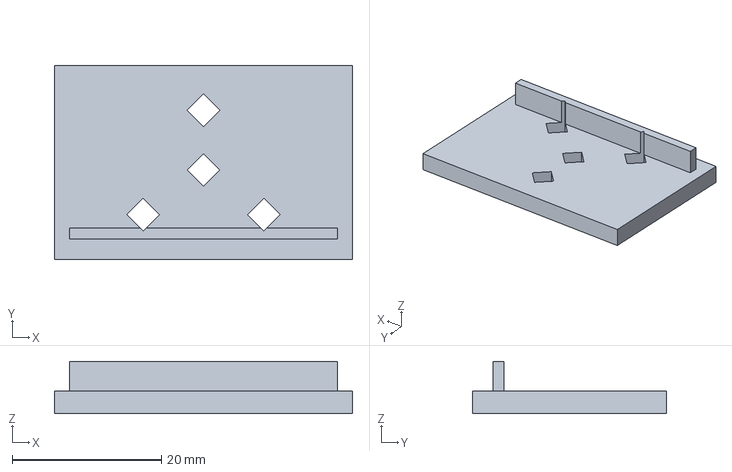
[picture p145: CAD file, 2026-09-18]
output/a1_full_size/sliced/RIB_ANCHOR/RIB_ANCHOR_A1Mini_PETG.3mf
40.0 x 26.0 x 7.00 mm
