rboyd/fpv-drone-racing-gate/output/a1_full_size/sliced/RIB_CROSS/RIB_CROSS_A1Mini_PETG.3mf

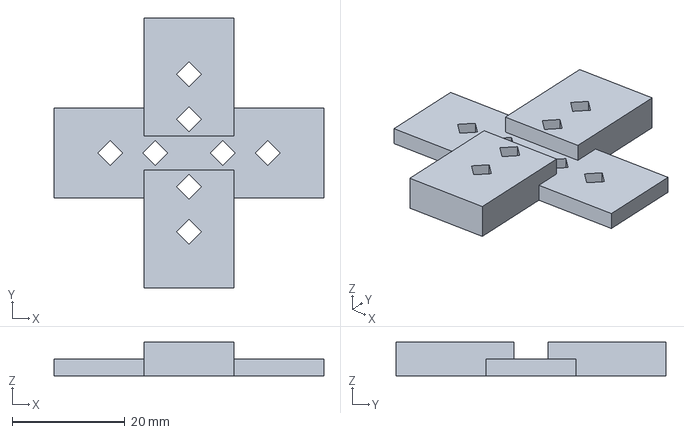
[picture p146: CAD file, 2026-09-18]
output/a1_full_size/sliced/RIB_CROSS/RIB_CROSS_A1Mini_PETG.3mf
48.0 x 48.0 x 6.00 mm
