rboyd/fpv-drone-racing-gate/output/a1_full_size/sliced/RIB_H_LOW_DOCK/RIB_H_LOW_DOCK_A1Mini_PETG.3mf

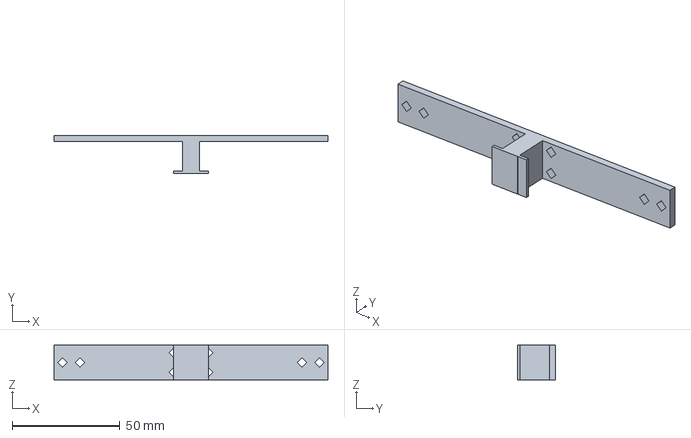
[picture p148: CAD file, 2026-09-18]
output/a1_full_size/sliced/RIB_H_LOW_DOCK/RIB_H_LOW_DOCK_A1Mini_PETG.3mf
126.9 x 17.8 x 16.0 mm
