rboyd/fpv-drone-racing-gate/output/a1_full_size/sliced/RIB_V_HIGH/RIB_V_HIGH_A1Mini_PETG.3mf

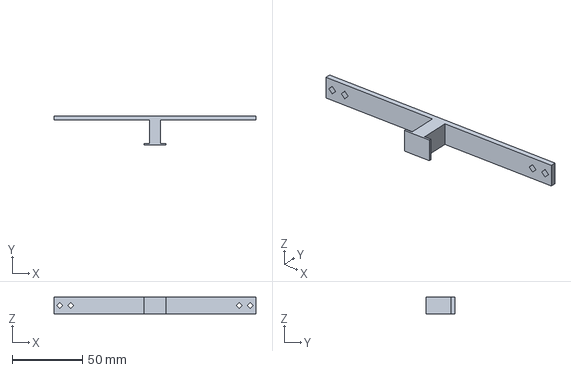
[picture p149: CAD file, 2026-09-18]
output/a1_full_size/sliced/RIB_V_HIGH/RIB_V_HIGH_A1Mini_PETG.3mf
144.2 x 20.8 x 12.0 mm
