rboyd/fpv-drone-racing-gate/output/a1_full_size/sliced/SNAP_BRIDGE/SNAP_BRIDGE_A1Mini_PETG.3mf

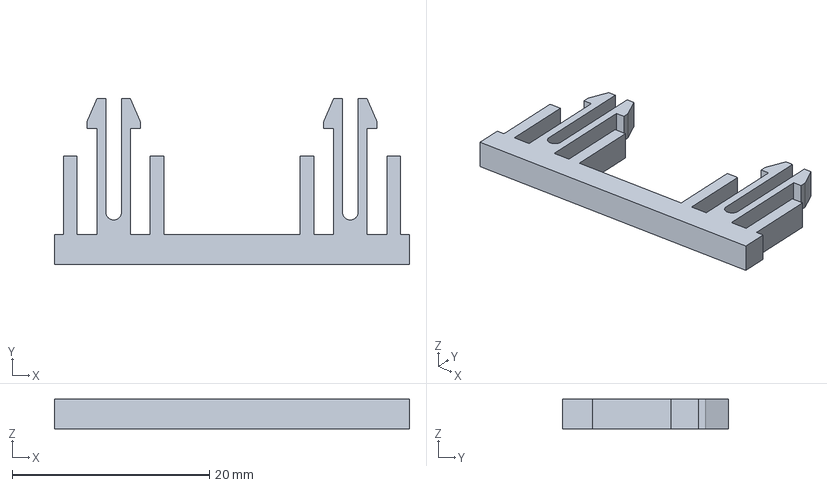
[picture p151: CAD file, 2026-09-18]
output/a1_full_size/sliced/SNAP_BRIDGE/SNAP_BRIDGE_A1Mini_PETG.3mf
36.0 x 16.8 x 3.00 mm
