rboyd/fpv-drone-racing-gate/output/a1_full_size/sliced/SPLINT/SPLINT_A1Mini_PETG.3mf

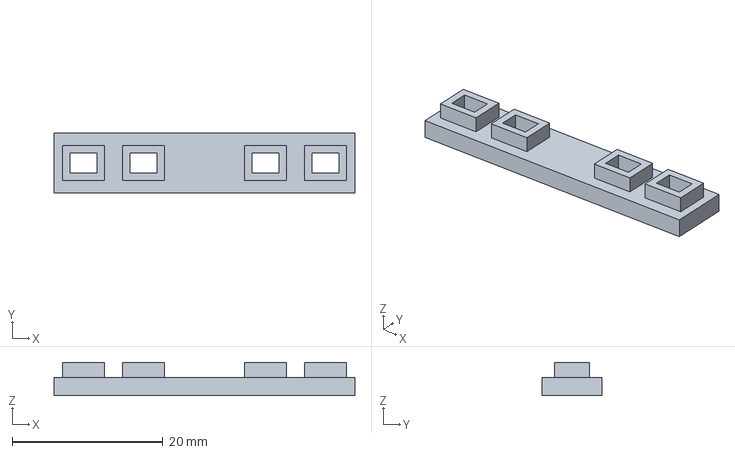
[picture p152: CAD file, 2026-09-18]
output/a1_full_size/sliced/SPLINT/SPLINT_A1Mini_PETG.3mf
40.0 x 8.00 x 4.40 mm
