rboyd/fpv-drone-racing-gate/output/compact_gate_study/printable/TAIL_MAG_SLEEVE_2.3mf

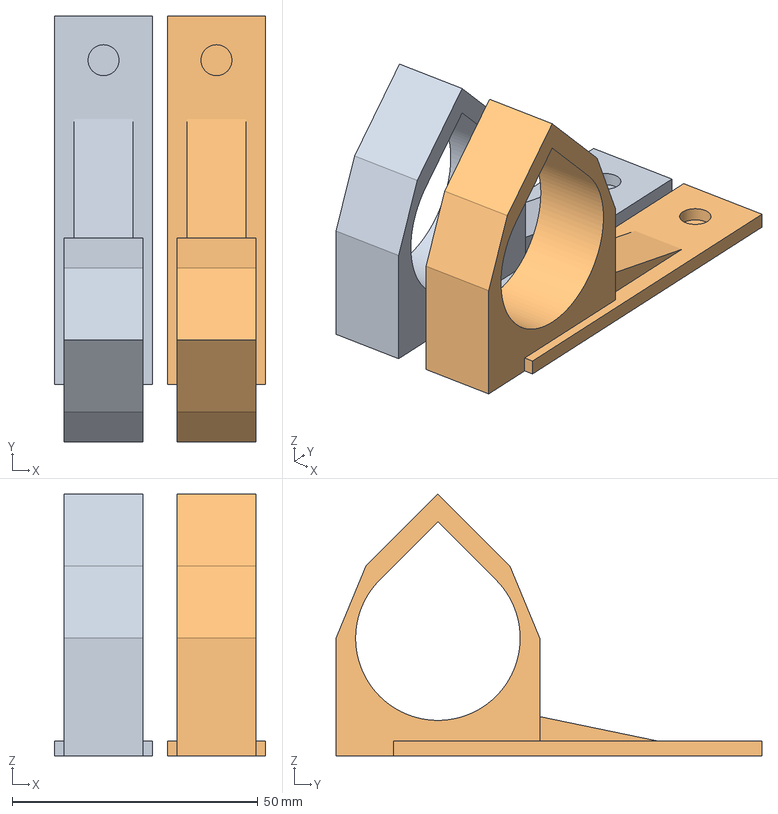
[picture p153: CAD file, 2026-09-19]
output/compact_gate_study/printable/TAIL_MAG_SLEEVE_2.3mf
43.0 x 86.8 x 53.3 mm
MAG_SLEEVE x 2
