rboyd/fpv-drone-racing-gate/output/compact_gate_study/sliced/TAIL_MAG_SLEEVE_4/TAIL_MAG_SLEEVE_4_A1Mini_PETG.3mf

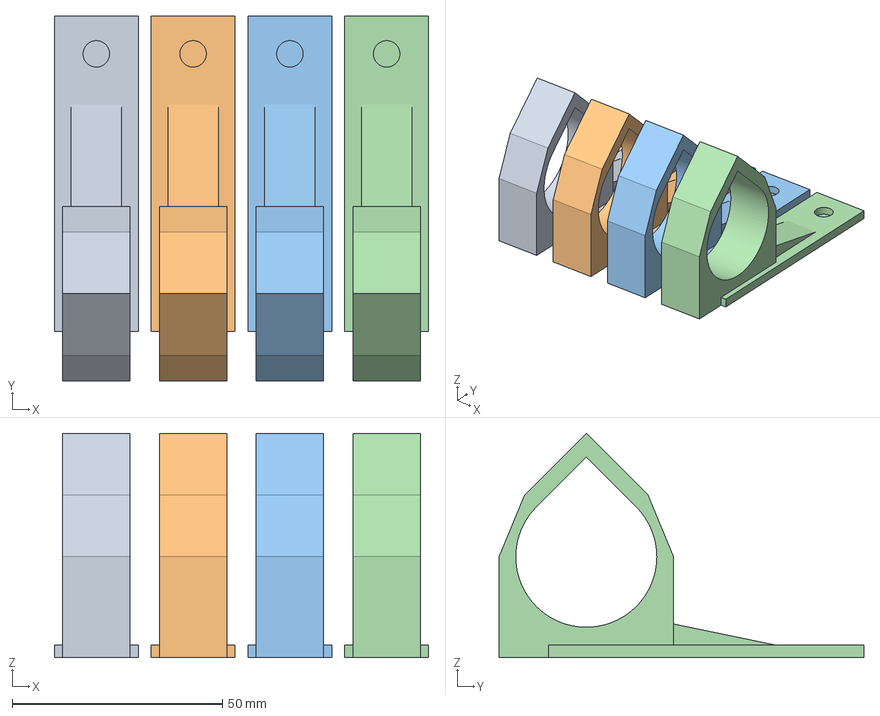
[picture p154: CAD file, 2026-09-19]
output/compact_gate_study/sliced/TAIL_MAG_SLEEVE_4/TAIL_MAG_SLEEVE_4_A1Mini_PETG.3mf
89.0 x 86.8 x 53.3 mm
MAG_SLEEVE x 4
