rboyd/fpv-drone-racing-gate/output/corner_guide_elbow/printable/ONE_DUAL_GUY_ELBOW.3mf

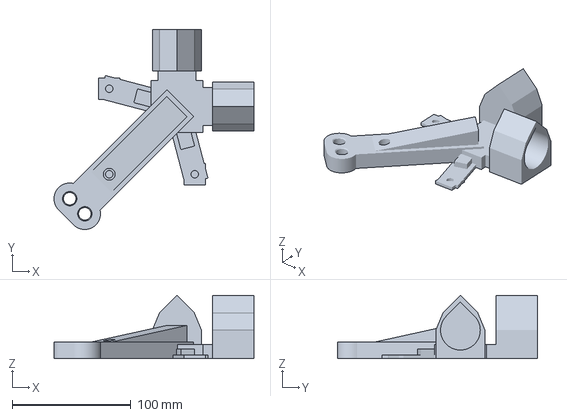
[picture p155: CAD file, 2026-09-19]
output/corner_guide_elbow/printable/ONE_DUAL_GUY_ELBOW.3mf
168.6 x 168.6 x 53.3 mm
