rboyd/fpv-drone-racing-gate/output/corner_guide_elbow/sliced/BATCH_MAG_SLEEVE/BATCH_MAG_SLEEVE_A1Mini_PETG.3mf

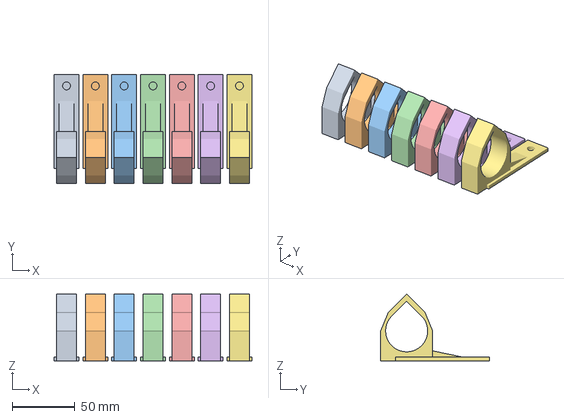
[picture p156: CAD file, 2026-09-19]
output/corner_guide_elbow/sliced/BATCH_MAG_SLEEVE/BATCH_MAG_SLEEVE_A1Mini_PETG.3mf
158.0 x 86.8 x 53.3 mm
MAG_SLEEVE x 7
