rboyd/fpv-drone-racing-gate/output/corner_guide_elbow/sliced/ONE_CROSS/ONE_CROSS_A1Mini_PETG.3mf

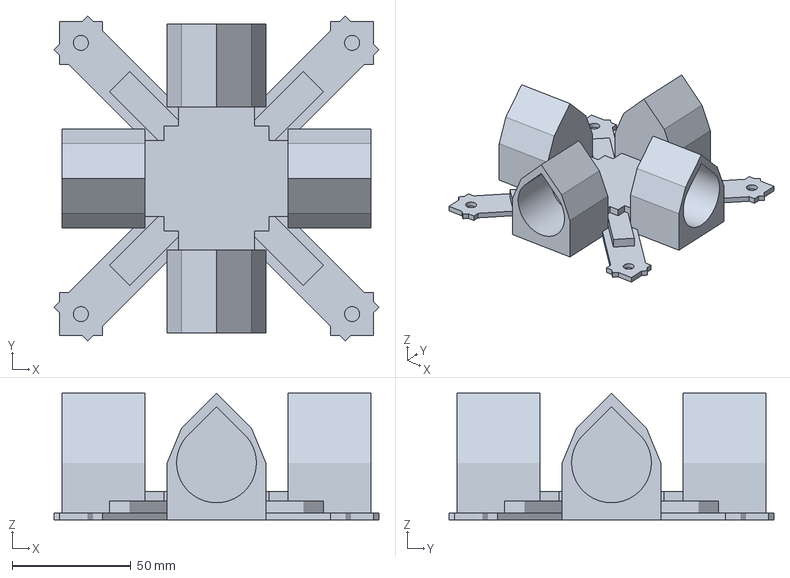
[picture p157: CAD file, 2026-09-19]
output/corner_guide_elbow/sliced/ONE_CROSS/ONE_CROSS_A1Mini_PETG.3mf
136.6 x 136.6 x 53.3 mm
