rboyd/fpv-drone-racing-gate/output/corner_guide_elbow/sliced/ONE_ELBOW/ONE_ELBOW_A1Mini_PETG.3mf

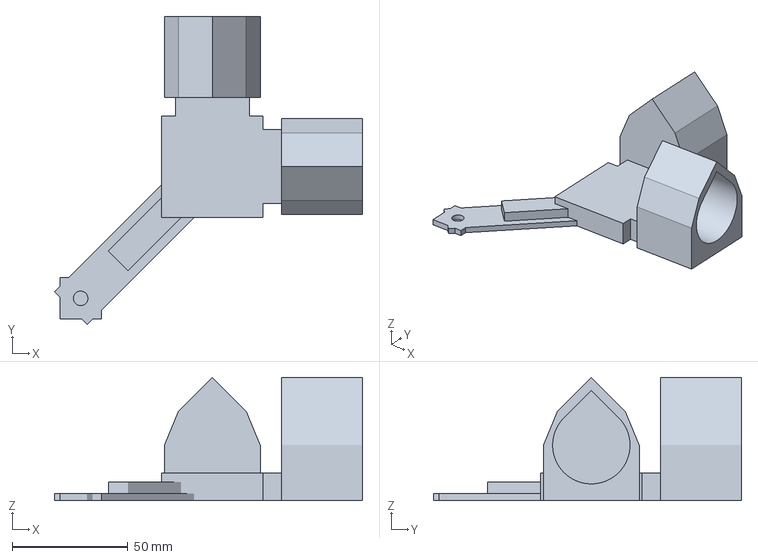
[picture p158: CAD file, 2026-09-19]
output/corner_guide_elbow/sliced/ONE_ELBOW/ONE_ELBOW_A1Mini_PETG.3mf
133.3 x 133.3 x 53.3 mm
