rboyd/fpv-drone-racing-gate/output/corner_guide_elbow/sliced/ONE_MAG_SLEEVE/ONE_MAG_SLEEVE_A1Mini_PETG.3mf

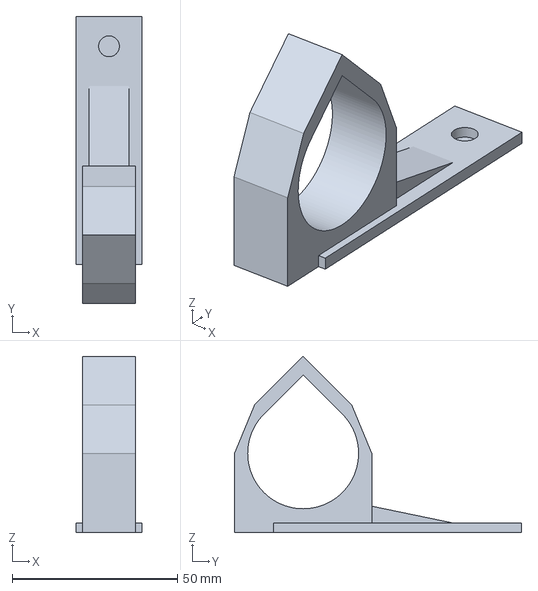
[picture p159: CAD file, 2026-09-19]
output/corner_guide_elbow/sliced/ONE_MAG_SLEEVE/ONE_MAG_SLEEVE_A1Mini_PETG.3mf
20.0 x 86.8 x 53.3 mm
