rboyd/fpv-drone-racing-gate/output/corner_guide_elbow/sliced/TAIL_MAG_SLEEVE_3/TAIL_MAG_SLEEVE_3_A1Mini_PETG.3mf

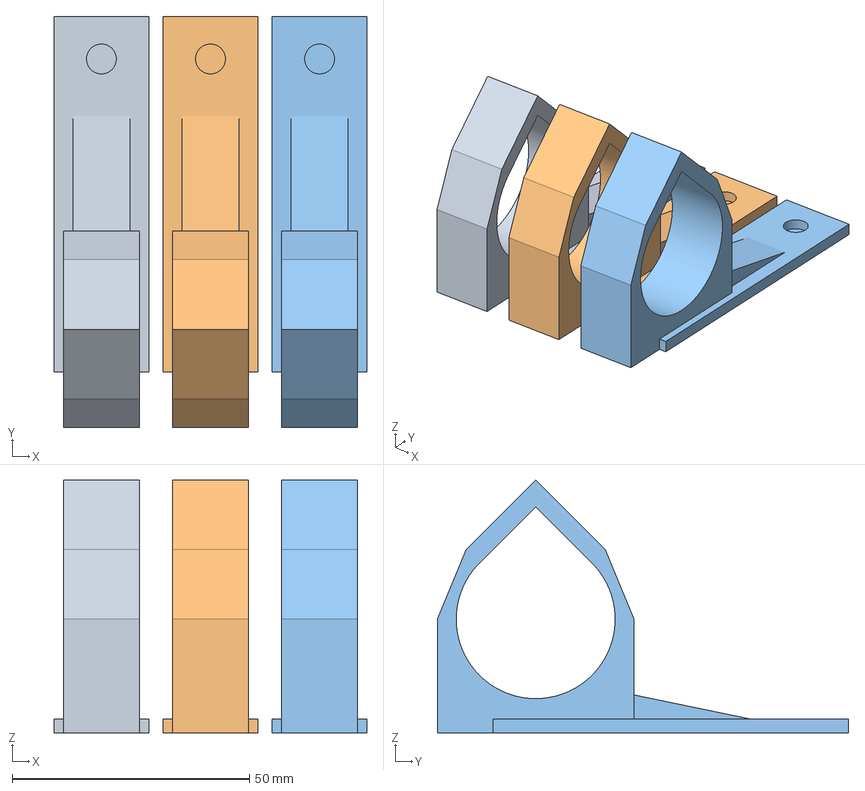
[picture p161: CAD file, 2026-09-19]
output/corner_guide_elbow/sliced/TAIL_MAG_SLEEVE_3/TAIL_MAG_SLEEVE_3_A1Mini_PETG.3mf
66.0 x 86.8 x 53.3 mm
MAG_SLEEVE x 3
