rboyd/fpv-drone-racing-gate/output/dual_guy_gate/printable/ONE_DUAL_GUY_ELBOW.3mf

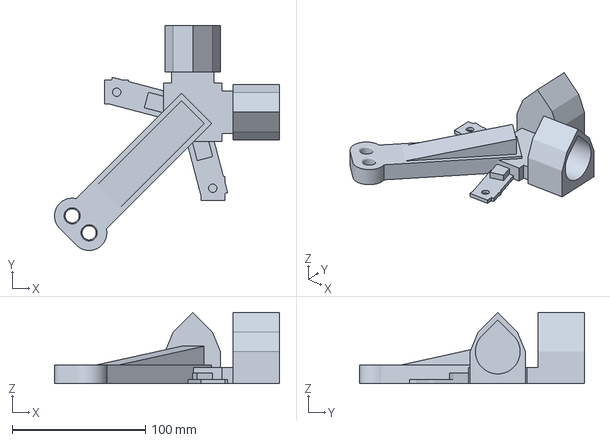
[picture p163: CAD file, 2026-09-19]
output/dual_guy_gate/printable/ONE_DUAL_GUY_ELBOW.3mf
168.6 x 168.6 x 53.3 mm
