rboyd/fpv-drone-racing-gate/output/first_frame_print/printable/FIRST_FRAME_TEST.3mf

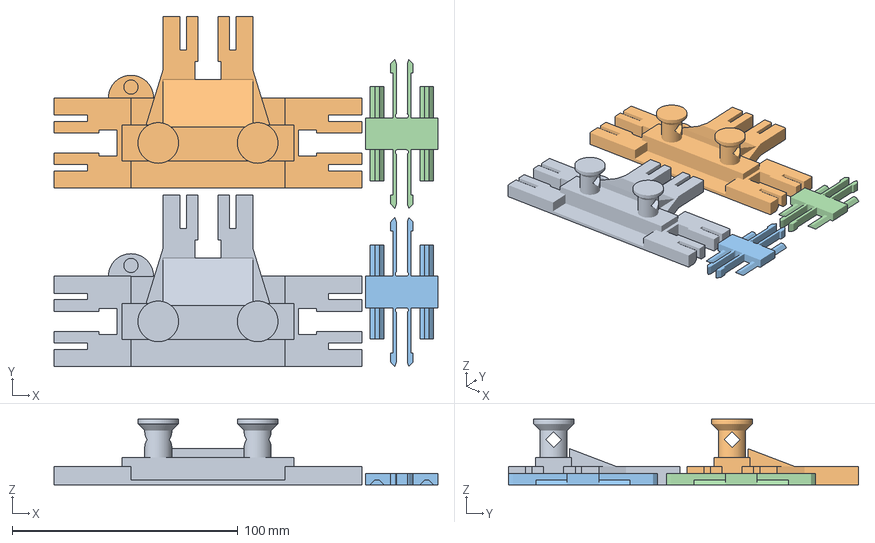
[picture p164: CAD file, 2026-09-18]
output/first_frame_print/printable/FIRST_FRAME_TEST.3mf
170.0 x 155.0 x 29.0 mm
01_EDGE_BRANCH
02_EDGE_BRANCH
03_CLICK_KEY
04_CLICK_KEY
