rboyd/fpv-drone-racing-gate/output/first_frame_print/sliced/FIRST_FRAME_TEST_WITH_PAD/FIRST_FRAME_TEST_WITH_PAD_A1Mini_PETG.3mf

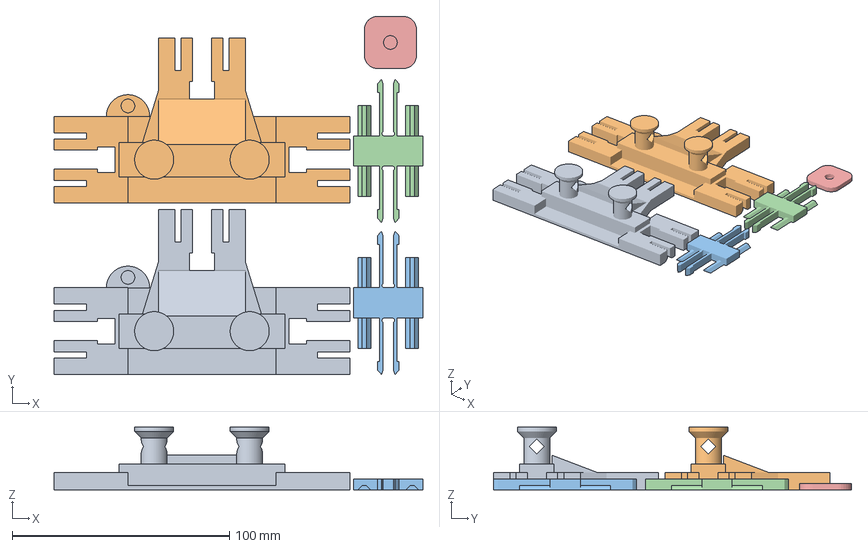
[picture p165: CAD file, 2026-09-18]
output/first_frame_print/sliced/FIRST_FRAME_TEST_WITH_PAD/FIRST_FRAME_TEST_WITH_PAD_A1Mini_PETG.3mf
170.0 x 165.0 x 29.0 mm
01_EDGE_BRANCH
02_EDGE_BRANCH
03_CLICK_KEY
04_CLICK_KEY
05_PAPER_PAD_OPTIONAL
