rboyd/fpv-drone-racing-gate/output/full_paper_gate/sliced/Q_DOCK_SOCKET_TAIL/Q_DOCK_SOCKET_TAIL_A1Mini_PETG.3mf

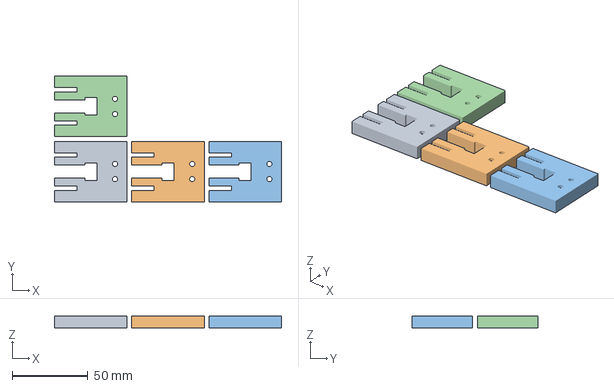
[picture p166: CAD file, 2026-09-18]
output/full_paper_gate/sliced/Q_DOCK_SOCKET_TAIL/Q_DOCK_SOCKET_TAIL_A1Mini_PETG.3mf
150.0 x 83.0 x 8.00 mm
DOCK_SOCKET x 4
