rboyd/fpv-drone-racing-gate/output/full_paper_gate/sliced/Q_DOCK_TONGUE_TAIL/Q_DOCK_TONGUE_TAIL_A1Mini_PETG.3mf

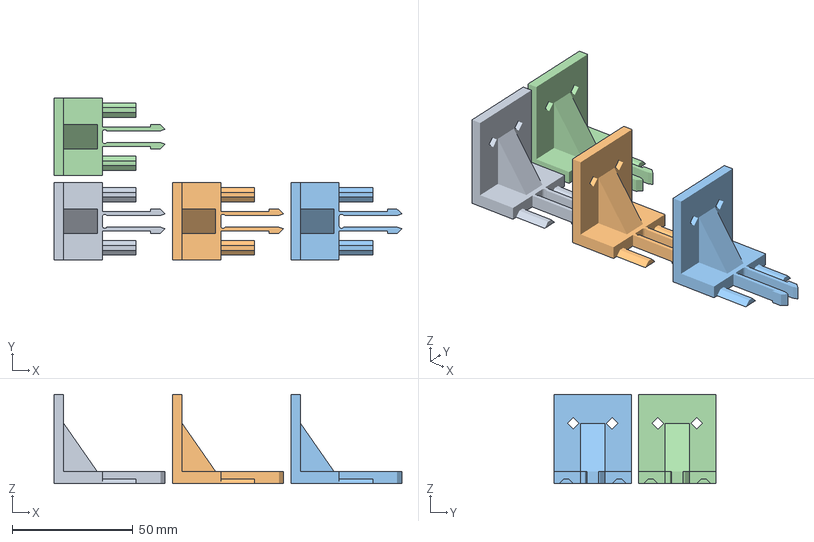
[picture p167: CAD file, 2026-09-18]
output/full_paper_gate/sliced/Q_DOCK_TONGUE_TAIL/Q_DOCK_TONGUE_TAIL_A1Mini_PETG.3mf
144.0 x 67.0 x 37.0 mm
DOCK_TONGUE x 4
