rboyd/fpv-drone-racing-gate/output/full_paper_gate/sliced/Q_EDGE_PLAIN_TAIL/Q_EDGE_PLAIN_TAIL_A1Mini_PETG.3mf

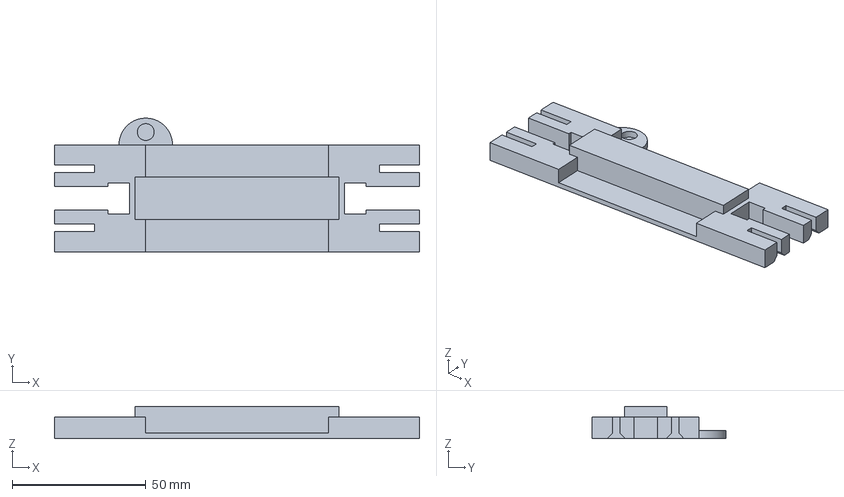
[picture p168: CAD file, 2026-09-18]
output/full_paper_gate/sliced/Q_EDGE_PLAIN_TAIL/Q_EDGE_PLAIN_TAIL_A1Mini_PETG.3mf
136.3 x 50.0 x 12.0 mm
