rboyd/fpv-drone-racing-gate/output/full_paper_gate/sliced/Q_PAPER_PAD_TAIL/Q_PAPER_PAD_TAIL_A1Mini_PETG.3mf

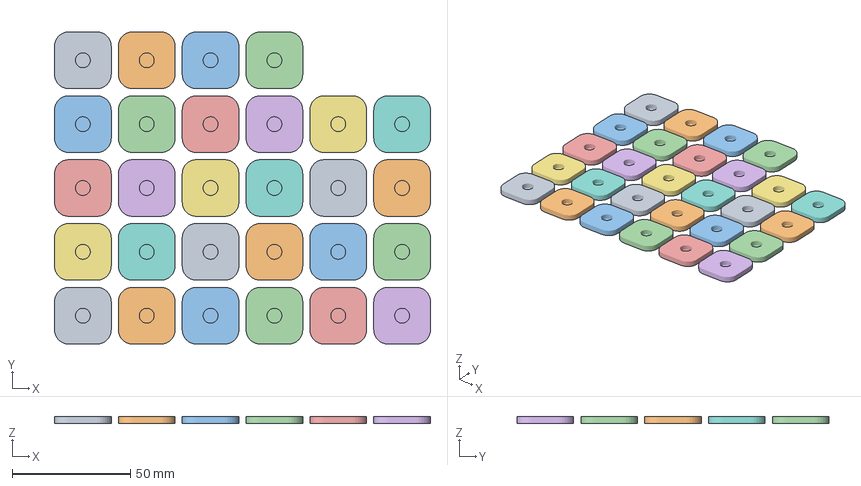
[picture p169: CAD file, 2026-09-18]
output/full_paper_gate/sliced/Q_PAPER_PAD_TAIL/Q_PAPER_PAD_TAIL_A1Mini_PETG.3mf
159.0 x 132.0 x 3.00 mm
PAPER_PAD x 28
