rboyd/fpv-drone-racing-gate/output/full_paper_gate/sliced/Q_PVC_HALF_33_TAIL/Q_PVC_HALF_33_TAIL_A1Mini_PETG.3mf

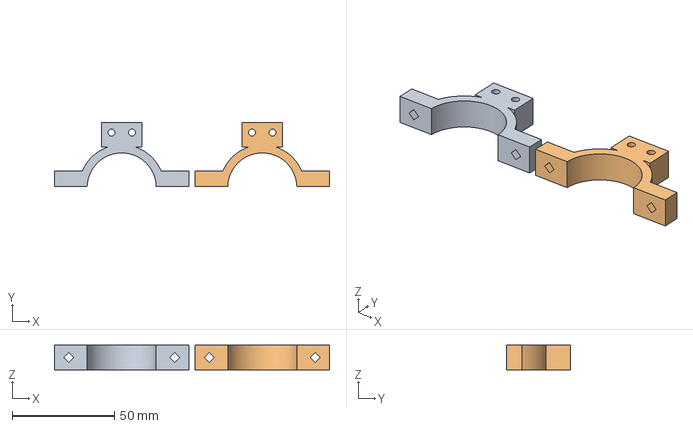
[picture p170: CAD file, 2026-09-18]
output/full_paper_gate/sliced/Q_PVC_HALF_33_TAIL/Q_PVC_HALF_33_TAIL_A1Mini_PETG.3mf
134.6 x 31.5 x 12.0 mm
PVC_HALF_33 x 2
