rboyd/fpv-drone-racing-gate/output/full_paper_gate/sliced/Q_V_BLOCK_TAIL/Q_V_BLOCK_TAIL_A1Mini_PETG.3mf

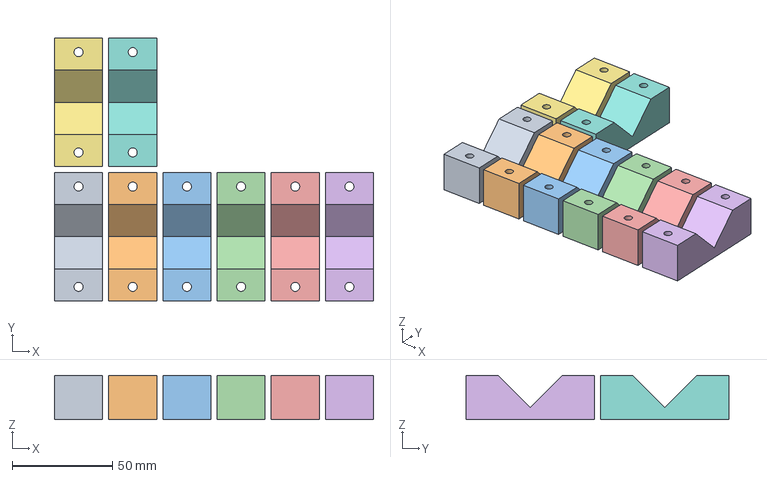
[picture p171: CAD file, 2026-09-18]
output/full_paper_gate/sliced/Q_V_BLOCK_TAIL/Q_V_BLOCK_TAIL_A1Mini_PETG.3mf
159.0 x 131.0 x 22.0 mm
V_BLOCK x 8
