rboyd/fpv-drone-racing-gate/output/full_paper_gate/sliced/T01_BRANCH/T01_BRANCH_A1Mini_PETG.3mf

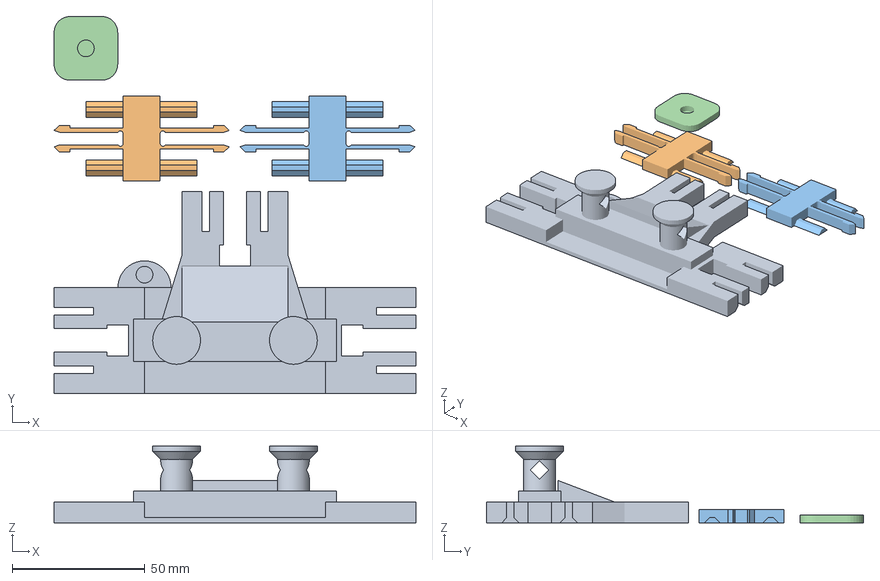
[picture p172: CAD file, 2026-09-18]
output/full_paper_gate/sliced/T01_BRANCH/T01_BRANCH_A1Mini_PETG.3mf
136.3 x 142.0 x 29.0 mm
EDGE_BRANCH
CLICK_KEY x 2
PAPER_PAD
