rboyd/fpv-drone-racing-gate/output/full_paper_gate/sliced/T03_PVC_DOCK/T03_PVC_DOCK_A1Mini_PETG.3mf

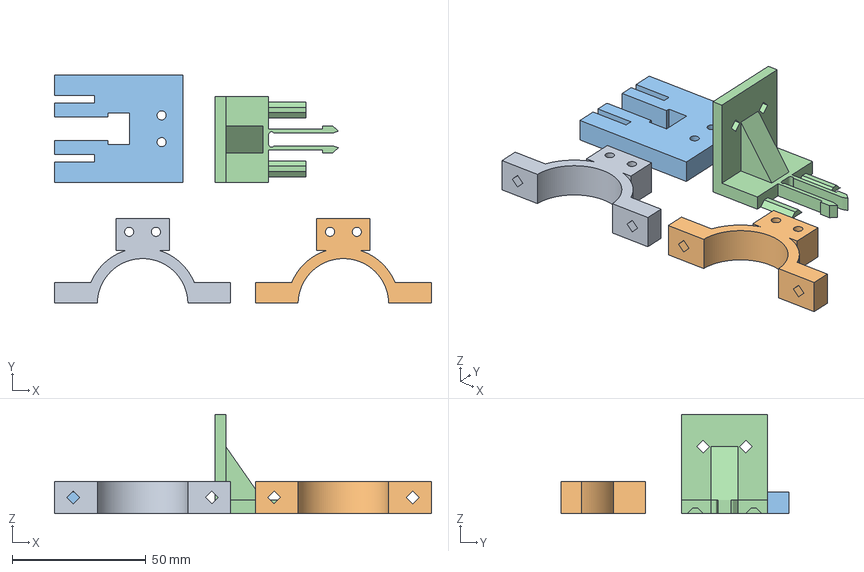
[picture p173: CAD file, 2026-09-18]
output/full_paper_gate/sliced/T03_PVC_DOCK/T03_PVC_DOCK_A1Mini_PETG.3mf
140.8 x 85.0 x 37.0 mm
PVC_HALF_33 x 2
DOCK_SOCKET
DOCK_TONGUE
