rboyd/fpv-drone-racing-gate/output/full_paper_gate/sliced/T04_BRACE/T04_BRACE_A1Mini_PETG.3mf

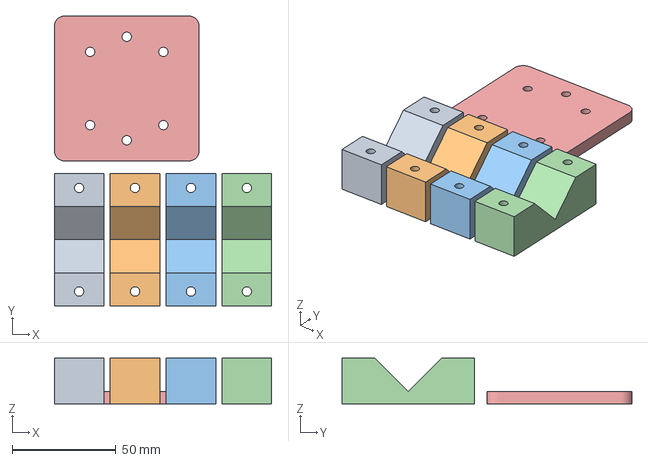
[picture p174: CAD file, 2026-09-18]
output/full_paper_gate/sliced/T04_BRACE/T04_BRACE_A1Mini_PETG.3mf
105.0 x 140.0 x 22.0 mm
V_BLOCK x 4
CROSS_PLATE
