rboyd/fpv-drone-racing-gate/output/full_paper_gate/sliced/T05_SINGLE_PLAIN/T05_SINGLE_PLAIN_A1Mini_PETG.3mf

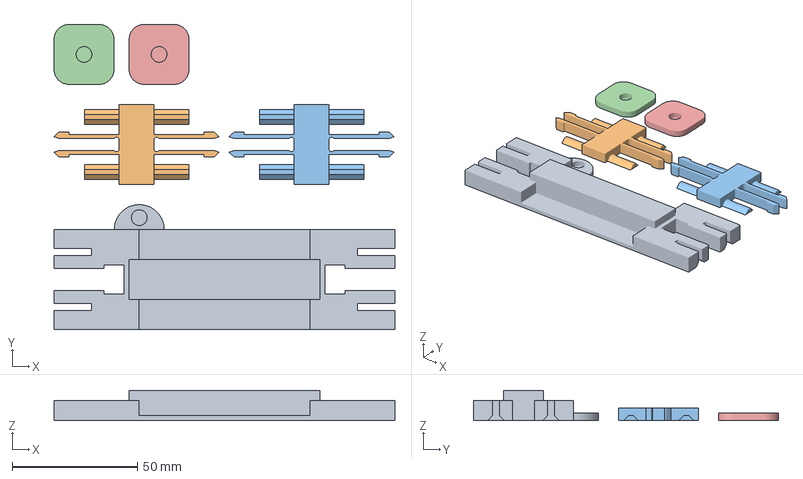
[picture p175: CAD file, 2026-09-18]
output/full_paper_gate/sliced/T05_SINGLE_PLAIN/T05_SINGLE_PLAIN_A1Mini_PETG.3mf
136.3 x 122.0 x 12.0 mm
EDGE_PLAIN
CLICK_KEY x 2
PAPER_PAD x 2
