rboyd/fpv-drone-racing-gate/output/full_width_demo/printable/FIT_SOCKET_25.3mf

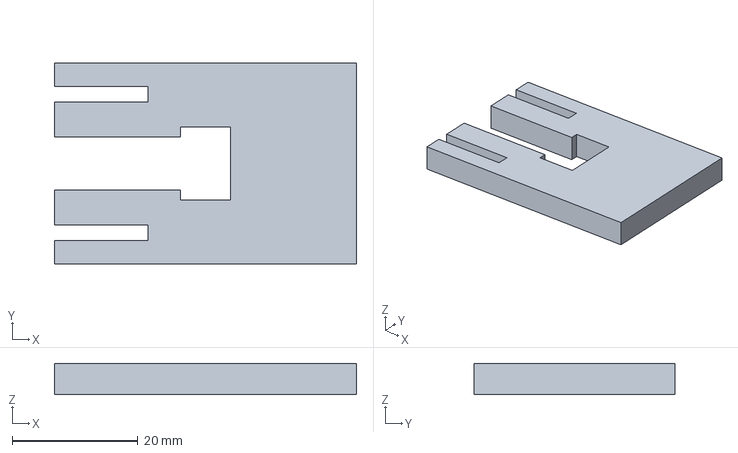
[picture p176: CAD file, 2026-09-18]
output/full_width_demo/printable/FIT_SOCKET_25.3mf
48.0 x 32.0 x 5.00 mm
