rboyd/fpv-drone-racing-gate/output/full_width_demo/sliced/00_FIT_CHECK/00_FIT_CHECK_A1Mini_PETG.3mf

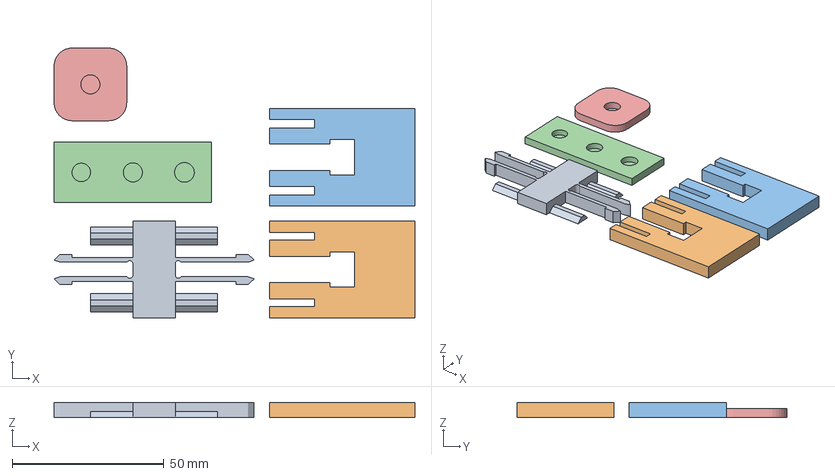
[picture p177: CAD file, 2026-09-18]
output/full_width_demo/sliced/00_FIT_CHECK/00_FIT_CHECK_A1Mini_PETG.3mf
119.0 x 89.0 x 5.00 mm
CLICK_KEY
FIT_SOCKET_25
FIT_SOCKET_40
MAGNET_GAUGE
PAPER_PAD
