rboyd/fpv-drone-racing-gate/output/full_width_demo/sliced/01_FRAME_REPEAT_4_TIMES/01_FRAME_REPEAT_4_TIMES_A1Mini_PETG.3mf

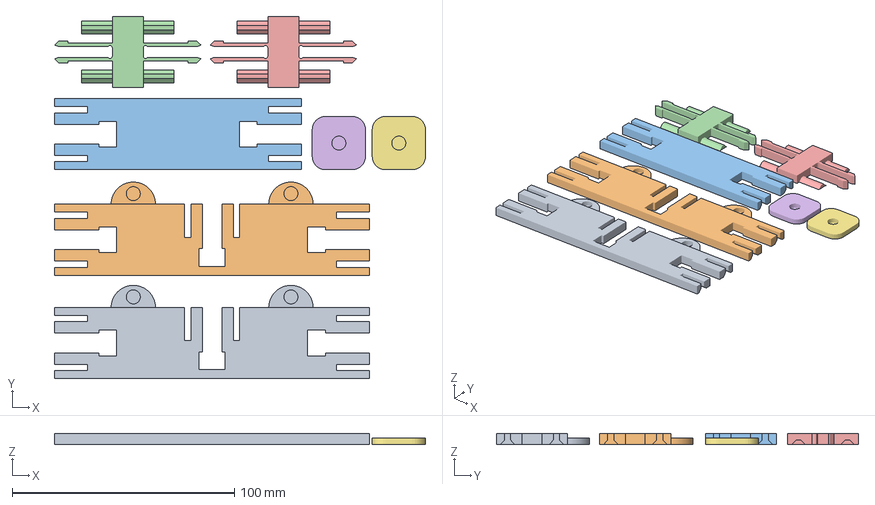
[picture p178: CAD file, 2026-09-18]
output/full_width_demo/sliced/01_FRAME_REPEAT_4_TIMES/01_FRAME_REPEAT_4_TIMES_A1Mini_PETG.3mf
167.0 x 163.0 x 5.00 mm
DEMO_EDGE x 2
DEMO_RUNG
CLICK_KEY x 2
PAPER_PAD x 2
