rboyd/fpv-drone-racing-gate/output/full_width_demo/sliced/02_KEYS_AND_PADS_ONCE/02_KEYS_AND_PADS_ONCE_A1Mini_PETG.3mf

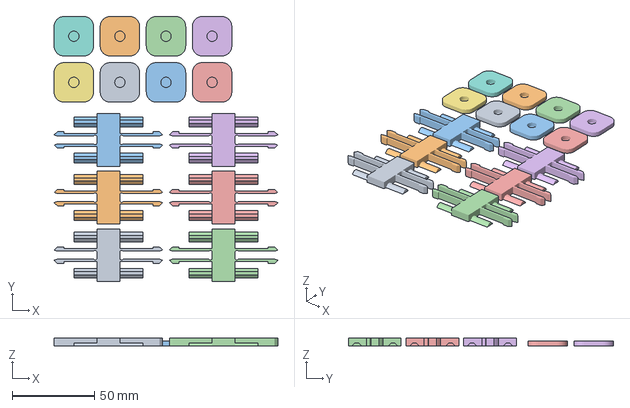
[picture p179: CAD file, 2026-09-18]
output/full_width_demo/sliced/02_KEYS_AND_PADS_ONCE/02_KEYS_AND_PADS_ONCE_A1Mini_PETG.3mf
136.0 x 161.0 x 5.00 mm
CLICK_KEY x 6
PAPER_PAD x 8
