rboyd/fpv-drone-racing-gate/output/full_width_demo/sliced/CLICK_KEY/CLICK_KEY_A1Mini_PETG.3mf

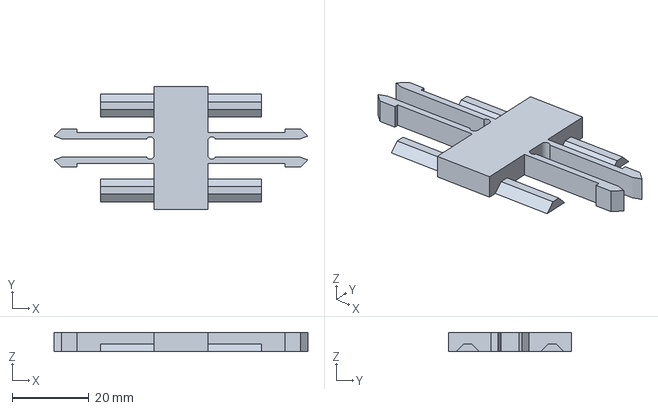
[picture p180: CAD file, 2026-09-18]
output/full_width_demo/sliced/CLICK_KEY/CLICK_KEY_A1Mini_PETG.3mf
66.0 x 32.0 x 5.00 mm
