rboyd/fpv-drone-racing-gate/output/full_width_demo/sliced/DEMO_EDGE/DEMO_EDGE_A1Mini_PETG.3mf

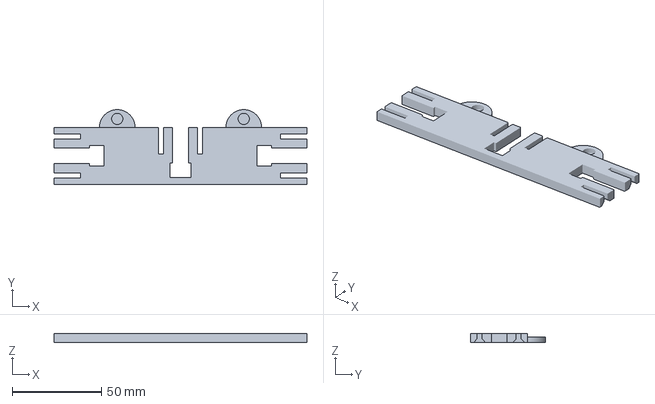
[picture p181: CAD file, 2026-09-18]
output/full_width_demo/sliced/DEMO_EDGE/DEMO_EDGE_A1Mini_PETG.3mf
141.9 x 42.0 x 5.00 mm
