rboyd/fpv-drone-racing-gate/output/full_width_demo/sliced/DEMO_RUNG/DEMO_RUNG_A1Mini_PETG.3mf

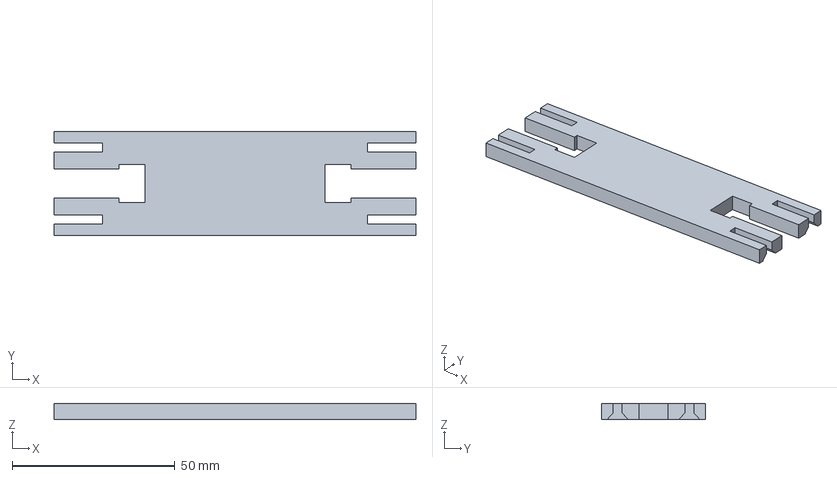
[picture p182: CAD file, 2026-09-18]
output/full_width_demo/sliced/DEMO_RUNG/DEMO_RUNG_A1Mini_PETG.3mf
111.2 x 32.0 x 5.00 mm
