rboyd/fpv-drone-racing-gate/output/full_width_demo/sliced/MAGNET_GAUGE/MAGNET_GAUGE_A1Mini_PETG.3mf

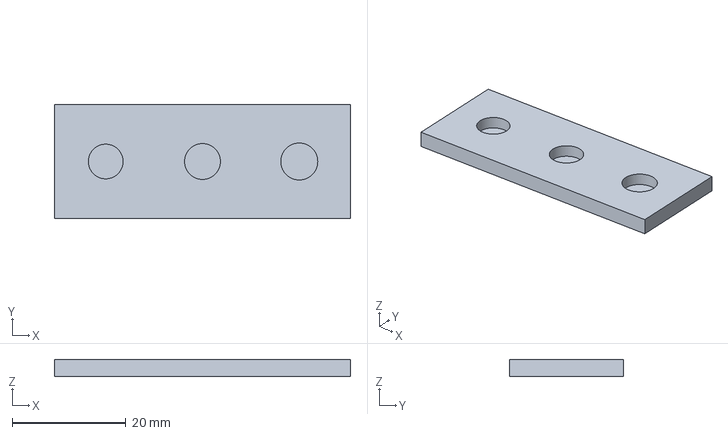
[picture p183: CAD file, 2026-09-18]
output/full_width_demo/sliced/MAGNET_GAUGE/MAGNET_GAUGE_A1Mini_PETG.3mf
52.0 x 20.0 x 3.00 mm
