rboyd/fpv-drone-racing-gate/output/full_width_demo/sliced/PAPER_PAD/PAPER_PAD_A1Mini_PETG.3mf

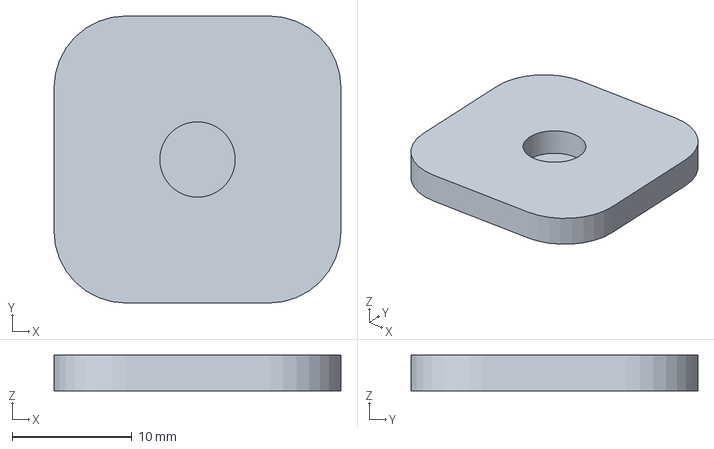
[picture p184: CAD file, 2026-09-18]
output/full_width_demo/sliced/PAPER_PAD/PAPER_PAD_A1Mini_PETG.3mf
24.0 x 24.0 x 3.00 mm
