rboyd/fpv-drone-racing-gate/output/orthogonal_pvc_gate/sliced/CROSS_AND_SLEEVE/CROSS_AND_SLEEVE_A1Mini_PETG.3mf

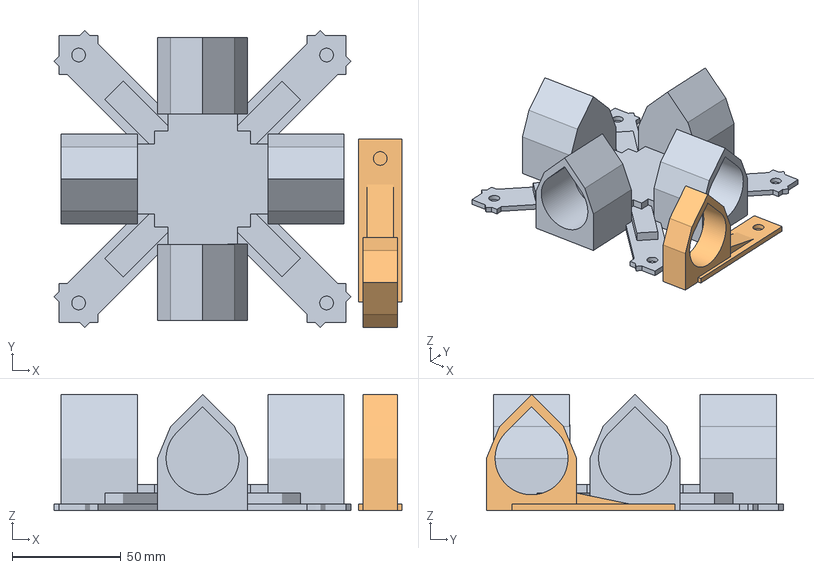
[picture p185: CAD file, 2026-09-19]
output/orthogonal_pvc_gate/sliced/CROSS_AND_SLEEVE/CROSS_AND_SLEEVE_A1Mini_PETG.3mf
160.0 x 136.6 x 53.3 mm
CROSS
MAG_SLEEVE
