rboyd/fpv-drone-racing-gate/output/orthogonal_pvc_gate/sliced/FIRST_FRICTION_FIT/FIRST_FRICTION_FIT_A1Mini_PETG.3mf

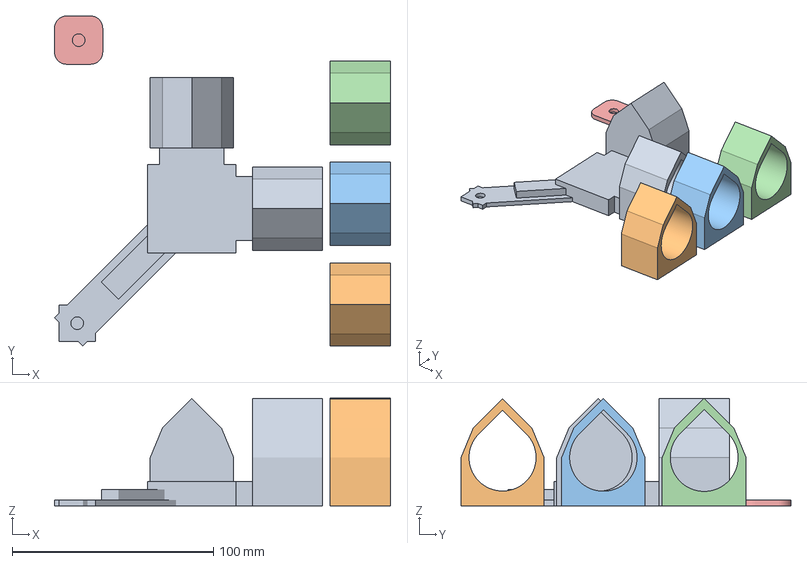
[picture p186: CAD file, 2026-09-19]
output/orthogonal_pvc_gate/sliced/FIRST_FRICTION_FIT/FIRST_FRICTION_FIT_A1Mini_PETG.3mf
167.0 x 164.0 x 53.5 mm
ELBOW
FIT_333
FIT_335
FIT_337
PAPER_PAD
