rboyd/fpv-drone-racing-gate/output/paper_roll_study/printable/05_D_MAGNET_AND_DOCK.3mf

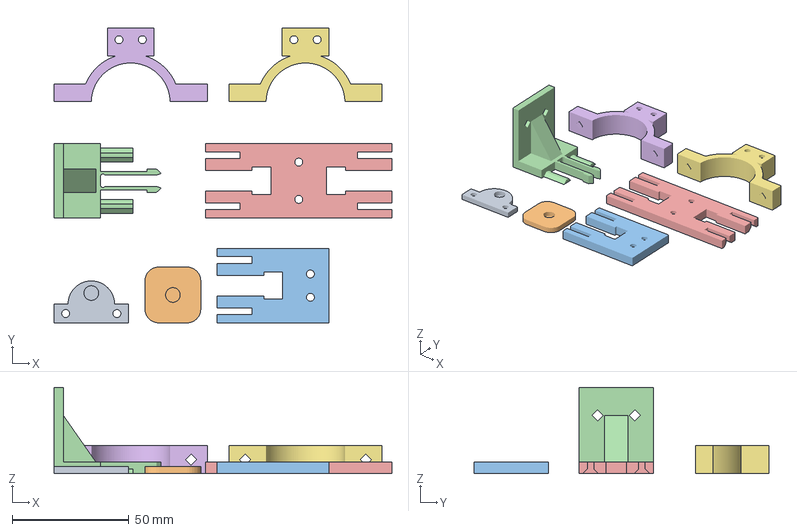
[picture p187: CAD file, 2026-09-18]
output/paper_roll_study/printable/05_D_MAGNET_AND_DOCK.3mf
145.0 x 126.5 x 37.0 mm
D_MAGNET_LUG
PAPER_PAD
DOCK_SOCKET
DOCK_TONGUE
FRAME_DOCK_NODE
PVC_HALF_33 x 2
