rboyd/fpv-drone-racing-gate/output/paper_roll_study/sliced/01_CLICK_AND_MAGNET_JOINTS/01_CLICK_AND_MAGNET_JOINTS_A1Mini_PETG.3mf

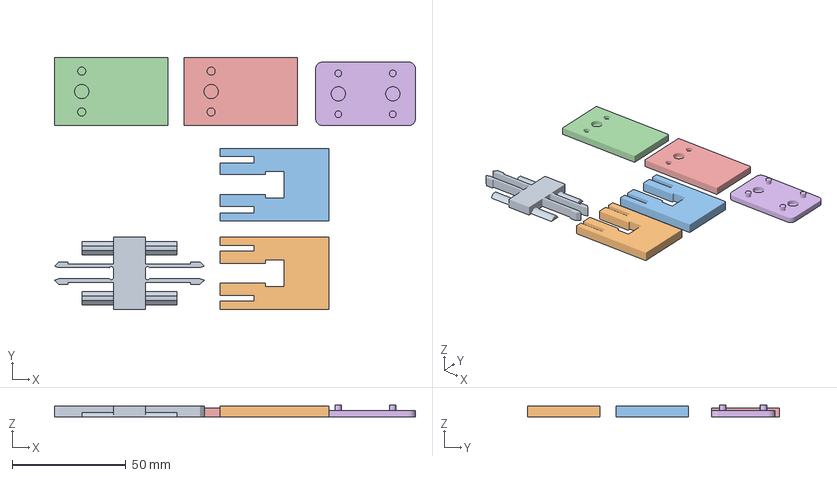
[picture p188: CAD file, 2026-09-18]
output/paper_roll_study/sliced/01_CLICK_AND_MAGNET_JOINTS/01_CLICK_AND_MAGNET_JOINTS_A1Mini_PETG.3mf
159.0 x 111.0 x 5.48 mm
CLICK_KEY
CLICK_SOCKET_25
CLICK_SOCKET_40
MAG_RAIL_END x 2
MAG_SPLICE_CAP
