rboyd/fpv-drone-racing-gate/output/paper_roll_study/sliced/02_PAPER_CLAMP_TESTS/02_PAPER_CLAMP_TESTS_A1Mini_PETG.3mf

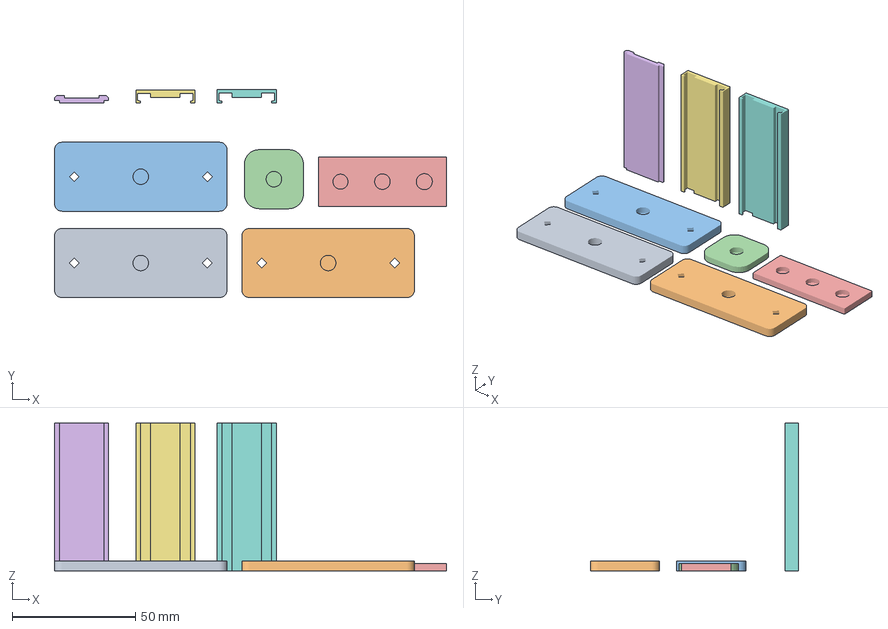
[picture p189: CAD file, 2026-09-18]
output/paper_roll_study/sliced/02_PAPER_CLAMP_TESTS/02_PAPER_CLAMP_TESTS_A1Mini_PETG.3mf
159.0 x 84.4 x 60.0 mm
PAPER_WINDOW_04
PAPER_WINDOW_08
PAPER_WINDOW_12
PAPER_PAD
MAGNET_POCKET_GAUGE
PAPER_SNAP_BASE
PAPER_SNAP_CAP_15
PAPER_SNAP_CAP_30
