rboyd/fpv-drone-racing-gate/output/paper_roll_study/sliced/03_STACK_SEPARATION_TESTS/03_STACK_SEPARATION_TESTS_A1Mini_PETG.3mf

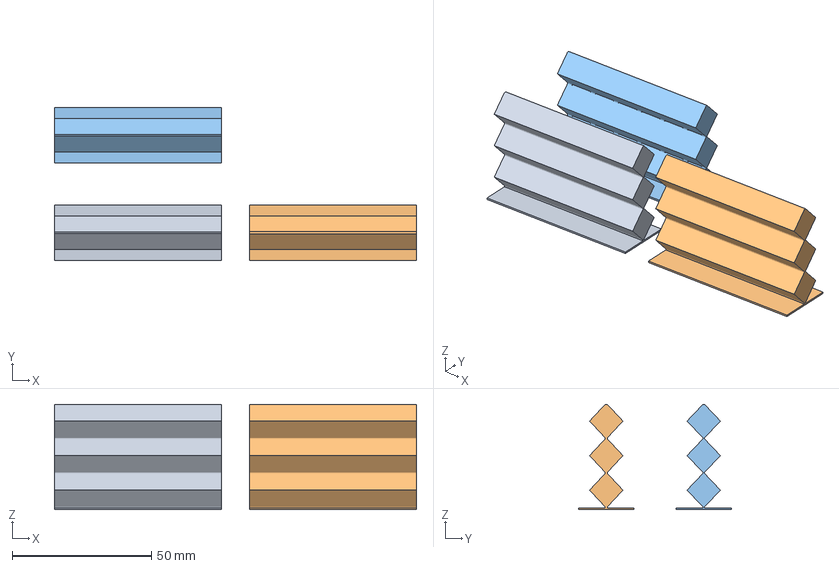
[picture p190: CAD file, 2026-09-18]
output/paper_roll_study/sliced/03_STACK_SEPARATION_TESTS/03_STACK_SEPARATION_TESTS_A1Mini_PETG.3mf
130.0 x 55.0 x 37.8 mm
STACK_TEST_06
STACK_TEST_08
STACK_TEST_TABS
