rboyd/fpv-drone-racing-gate/output/paper_roll_study/sliced/04_PVC_COLLAR_TEST/04_PVC_COLLAR_TEST_A1Mini_PETG.3mf

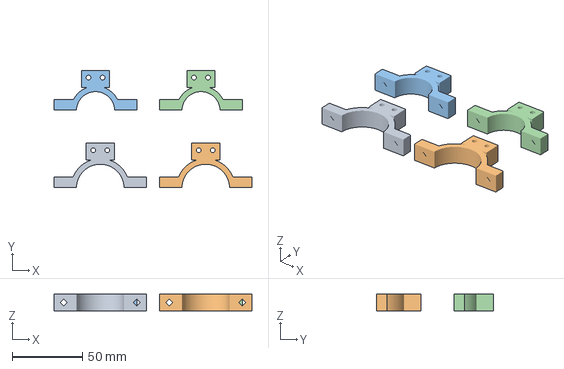
[picture p191: CAD file, 2026-09-18]
output/paper_roll_study/sliced/04_PVC_COLLAR_TEST/04_PVC_COLLAR_TEST_A1Mini_PETG.3mf
140.8 x 83.1 x 12.0 mm
PVC_HALF_33 x 2
PVC_HALF_27 x 2
