rboyd/fpv-drone-racing-gate/output/paper_roll_study/sliced/06_OVERNIGHT_26_RAILS/06_OVERNIGHT_26_RAILS_A1Mini_PETG.3mf

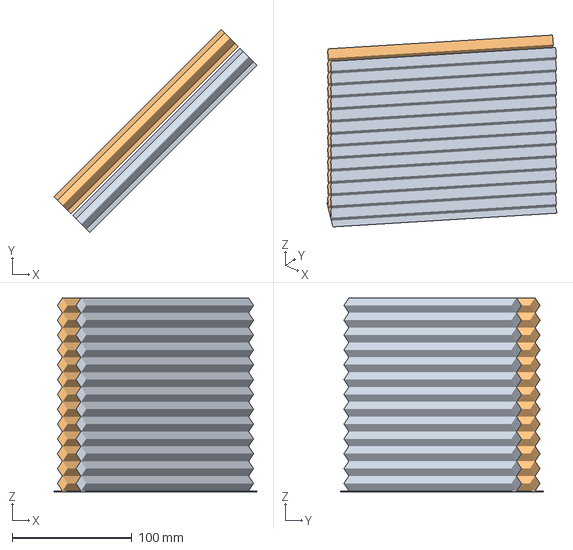
[picture p192: CAD file, 2026-09-18]
output/paper_roll_study/sliced/06_OVERNIGHT_26_RAILS/06_OVERNIGHT_26_RAILS_A1Mini_PETG.3mf
169.7 x 169.7 x 161.8 mm
DIAGONAL_13x198 x 2
