rboyd/fpv-drone-racing-gate/output/paper_roll_study/sliced/D_MAGNET_LUG/D_MAGNET_LUG_A1Mini_PETG.3mf

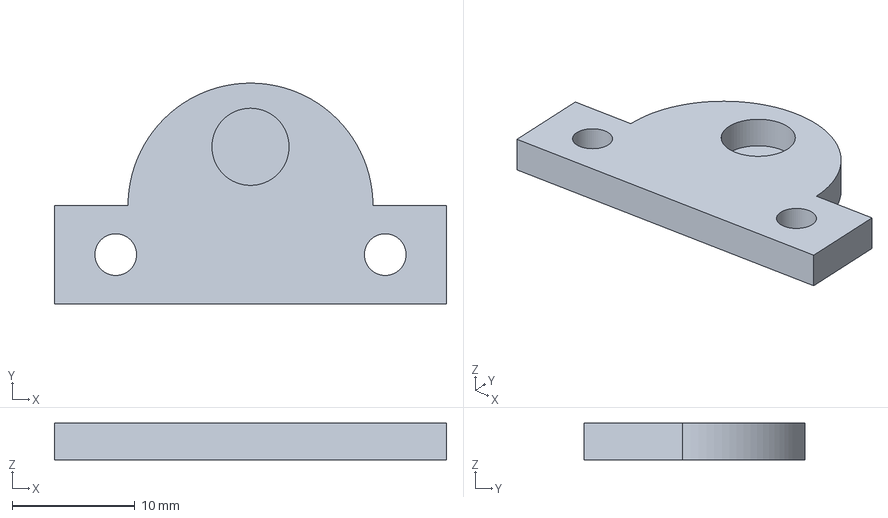
[picture p193: CAD file, 2026-09-18]
output/paper_roll_study/sliced/D_MAGNET_LUG/D_MAGNET_LUG_A1Mini_PETG.3mf
32.0 x 18.0 x 3.00 mm
