rboyd/fpv-drone-racing-gate/output/paper_roll_study/sliced/DIAGONAL_13x198/DIAGONAL_13x198_A1Mini_PETG.3mf

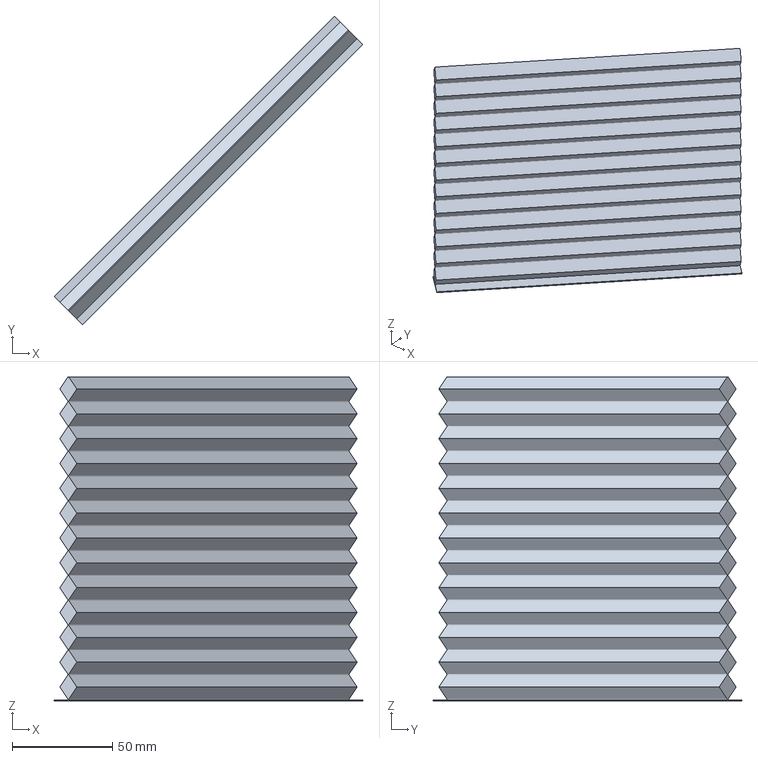
[picture p194: CAD file, 2026-09-18]
output/paper_roll_study/sliced/DIAGONAL_13x198/DIAGONAL_13x198_A1Mini_PETG.3mf
154.1 x 154.1 x 161.8 mm
