rboyd/fpv-drone-racing-gate/output/paper_roll_study/sliced/DIAGONAL_1x220/DIAGONAL_1x220_A1Mini_PETG.3mf

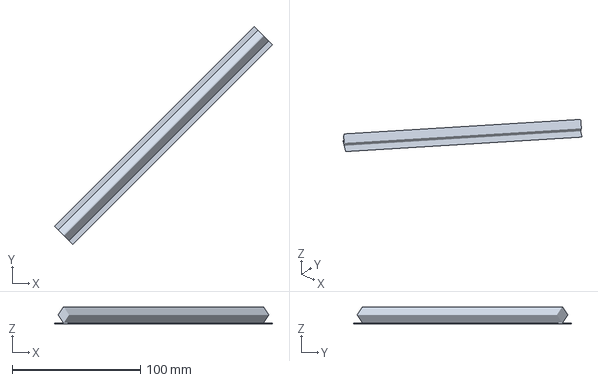
[picture p195: CAD file, 2026-09-18]
output/paper_roll_study/sliced/DIAGONAL_1x220/DIAGONAL_1x220_A1Mini_PETG.3mf
169.7 x 169.7 x 13.0 mm
