rboyd/fpv-drone-racing-gate/output/paper_roll_study/sliced/DOCK_SOCKET/DOCK_SOCKET_A1Mini_PETG.3mf

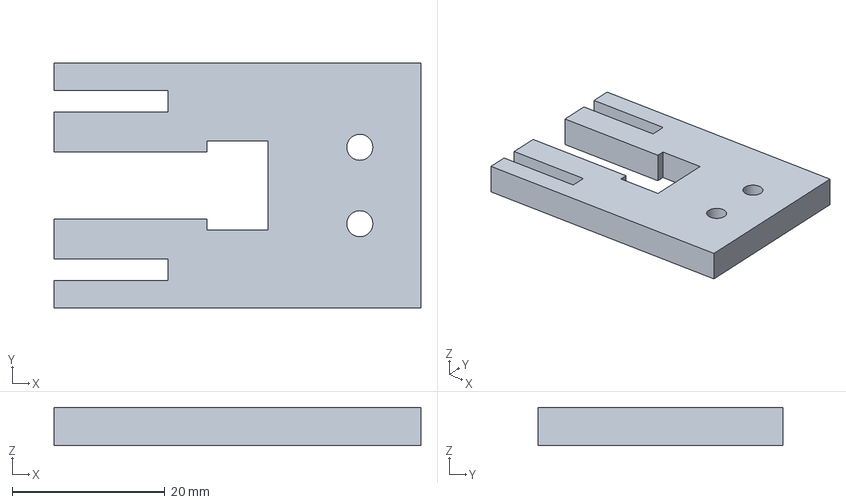
[picture p197: CAD file, 2026-09-18]
output/paper_roll_study/sliced/DOCK_SOCKET/DOCK_SOCKET_A1Mini_PETG.3mf
48.0 x 32.0 x 5.00 mm
