rboyd/fpv-drone-racing-gate/output/paper_roll_study/sliced/DOCK_TONGUE/DOCK_TONGUE_A1Mini_PETG.3mf

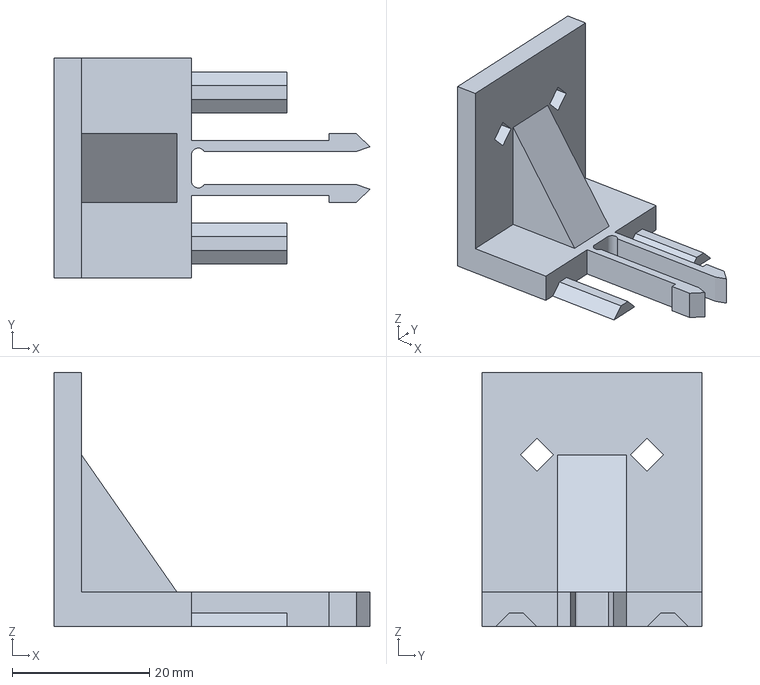
[picture p198: CAD file, 2026-09-18]
output/paper_roll_study/sliced/DOCK_TONGUE/DOCK_TONGUE_A1Mini_PETG.3mf
46.0 x 32.0 x 37.0 mm
