rboyd/fpv-drone-racing-gate/output/paper_roll_study/sliced/FRAME_DOCK_NODE/FRAME_DOCK_NODE_A1Mini_PETG.3mf

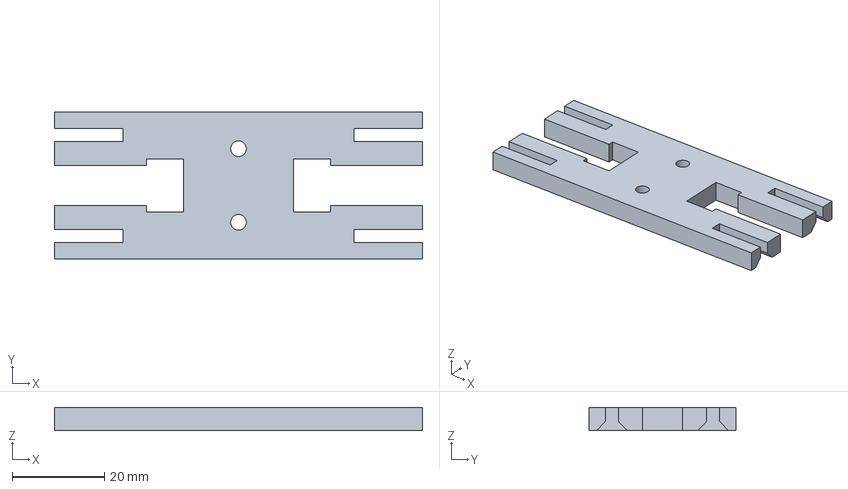
[picture p199: CAD file, 2026-09-18]
output/paper_roll_study/sliced/FRAME_DOCK_NODE/FRAME_DOCK_NODE_A1Mini_PETG.3mf
80.0 x 32.0 x 5.00 mm
