rboyd/fpv-drone-racing-gate/output/paper_roll_study/sliced/MAG_RAIL_END/MAG_RAIL_END_A1Mini_PETG.3mf

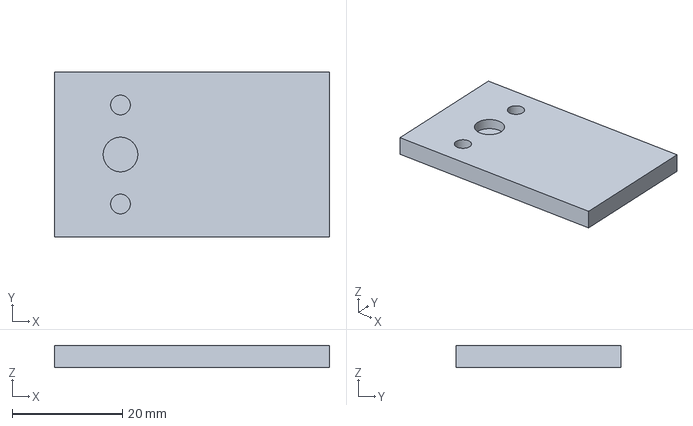
[picture p200: CAD file, 2026-09-18]
output/paper_roll_study/sliced/MAG_RAIL_END/MAG_RAIL_END_A1Mini_PETG.3mf
50.0 x 30.0 x 4.00 mm
