rboyd/fpv-drone-racing-gate/output/paper_roll_study/sliced/MAG_SPLICE_CAP/MAG_SPLICE_CAP_A1Mini_PETG.3mf

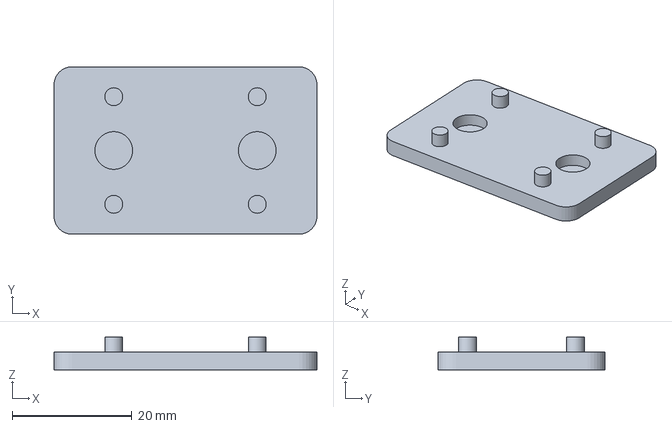
[picture p201: CAD file, 2026-09-18]
output/paper_roll_study/sliced/MAG_SPLICE_CAP/MAG_SPLICE_CAP_A1Mini_PETG.3mf
44.0 x 28.0 x 5.48 mm
