rboyd/fpv-drone-racing-gate/output/paper_roll_study/sliced/PAPER_SNAP_BASE/PAPER_SNAP_BASE_A1Mini_PETG.3mf

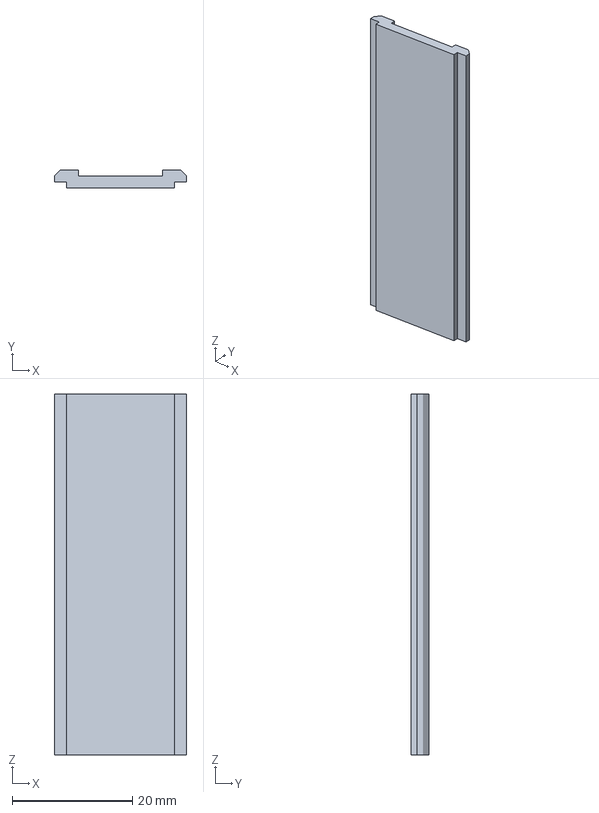
[picture p202: CAD file, 2026-09-18]
output/paper_roll_study/sliced/PAPER_SNAP_BASE/PAPER_SNAP_BASE_A1Mini_PETG.3mf
22.0 x 3.00 x 60.0 mm
