rboyd/fpv-drone-racing-gate/output/paper_roll_study/sliced/PAPER_SNAP_CAP_15/PAPER_SNAP_CAP_15_A1Mini_PETG.3mf

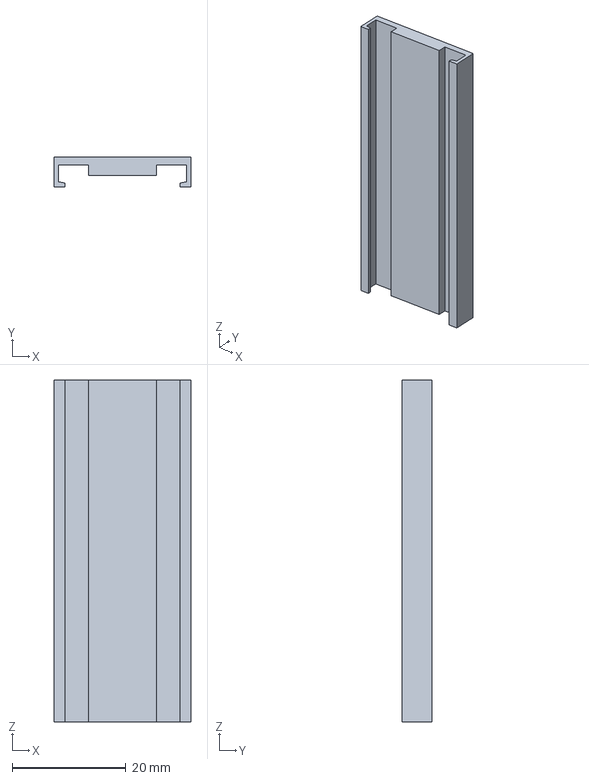
[picture p203: CAD file, 2026-09-18]
output/paper_roll_study/sliced/PAPER_SNAP_CAP_15/PAPER_SNAP_CAP_15_A1Mini_PETG.3mf
24.0 x 5.25 x 60.0 mm
