rboyd/fpv-drone-racing-gate/output/paper_roll_study/sliced/PAPER_SNAP_CAP_30/PAPER_SNAP_CAP_30_A1Mini_PETG.3mf

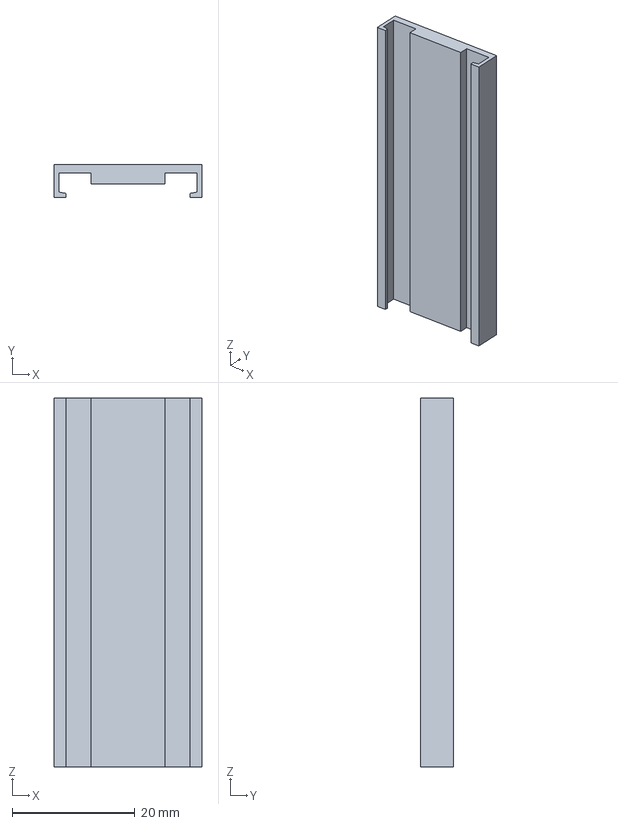
[picture p204: CAD file, 2026-09-18]
output/paper_roll_study/sliced/PAPER_SNAP_CAP_30/PAPER_SNAP_CAP_30_A1Mini_PETG.3mf
24.0 x 5.40 x 60.0 mm
