rboyd/fpv-drone-racing-gate/output/paper_roll_study/sliced/PAPER_WINDOW_04/PAPER_WINDOW_04_A1Mini_PETG.3mf

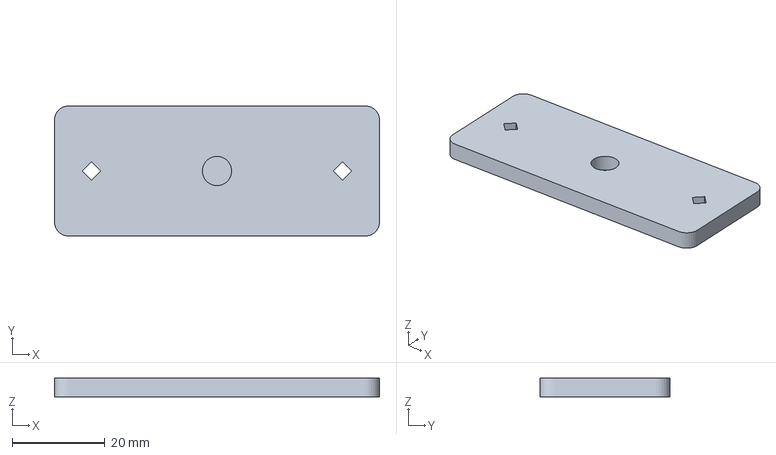
[picture p205: CAD file, 2026-09-18]
output/paper_roll_study/sliced/PAPER_WINDOW_04/PAPER_WINDOW_04_A1Mini_PETG.3mf
70.0 x 28.0 x 4.00 mm
