rboyd/fpv-drone-racing-gate/output/paper_roll_study/sliced/PVC_HALF_27/PVC_HALF_27_A1Mini_PETG.3mf

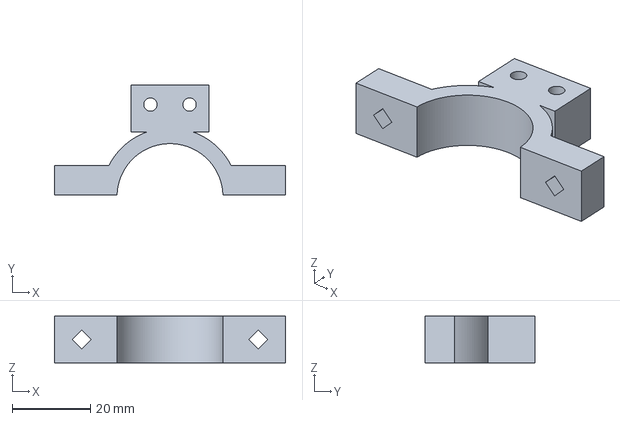
[picture p206: CAD file, 2026-09-18]
output/paper_roll_study/sliced/PVC_HALF_27/PVC_HALF_27_A1Mini_PETG.3mf
59.1 x 28.1 x 12.0 mm
