rboyd/fpv-drone-racing-gate/output/paper_roll_study/sliced/PVC_HALF_33/PVC_HALF_33_A1Mini_PETG.3mf

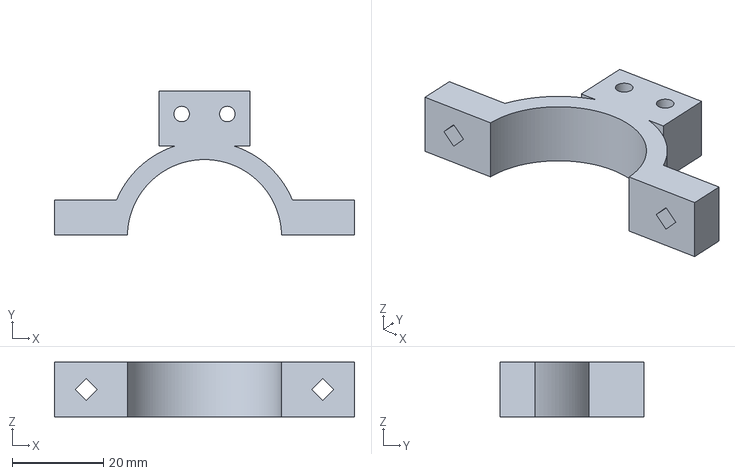
[picture p207: CAD file, 2026-09-18]
output/paper_roll_study/sliced/PVC_HALF_33/PVC_HALF_33_A1Mini_PETG.3mf
65.8 x 31.5 x 12.0 mm
