rboyd/fpv-drone-racing-gate/output/paper_roll_study/sliced/STACK_TEST_06/STACK_TEST_06_A1Mini_PETG.3mf

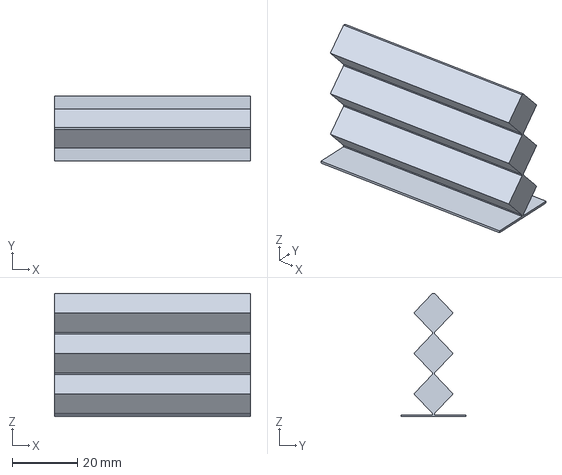
[picture p208: CAD file, 2026-09-18]
output/paper_roll_study/sliced/STACK_TEST_06/STACK_TEST_06_A1Mini_PETG.3mf
60.0 x 20.0 x 37.8 mm
