rboyd/fpv-drone-racing-gate/output/posterboard_concepts/prototype_coupons/hinge_knuckle_flat_mm.stl

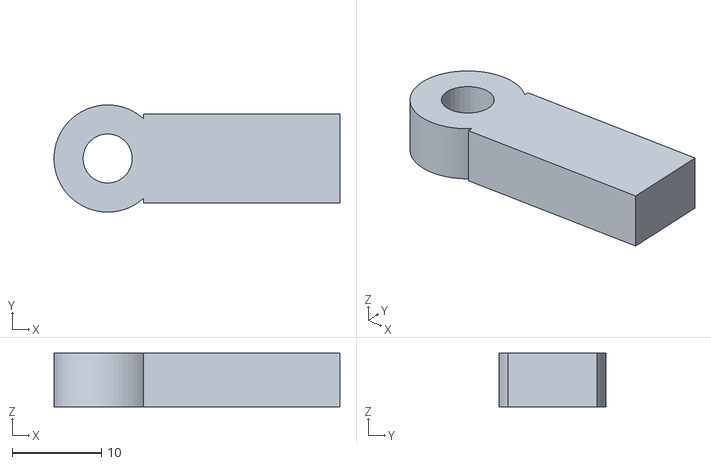
[picture p210: CAD file, 2026-09-17]
output/posterboard_concepts/prototype_coupons/hinge_knuckle_flat_mm.stl
32.0 x 12.0 x 6.00
