rboyd/fpv-drone-racing-gate/output/printable/jig_45_degree_mm.stl

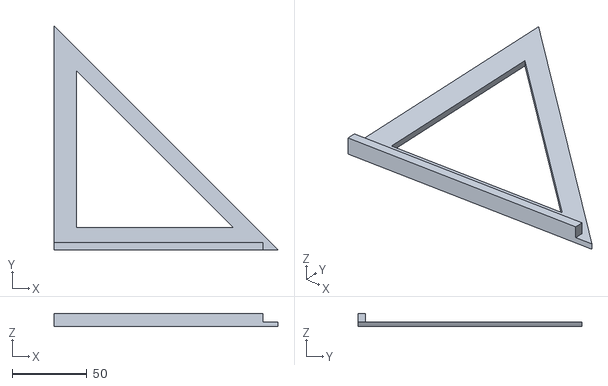
[picture p211: CAD file, 2026-09-17]
output/printable/jig_45_degree_mm.stl
150.0 x 150.0 x 9.00
