rboyd/fpv-drone-racing-gate/output/pvc_paper_gate/printable/FIRST_FIT.3mf

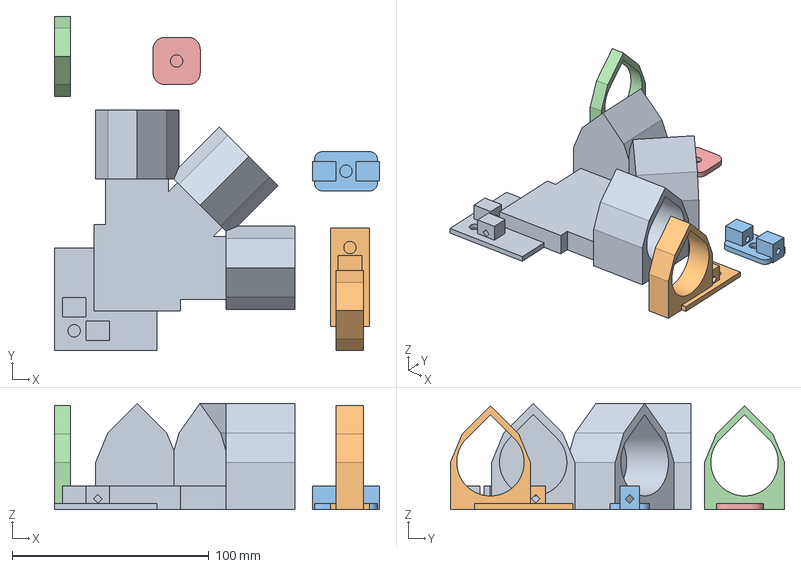
[picture p212: CAD file, 2026-09-19]
output/pvc_paper_gate/printable/FIRST_FIT.3mf
165.0 x 169.6 x 53.8 mm
OUTER_90_45
EDGE_SLEEVE
CORD_SADDLE
FIT_GAUGE
PAPER_PAD
