rboyd/fpv-drone-racing-gate/output/pvc_paper_gate/sliced/BATCH_CORD_SADDLE/BATCH_CORD_SADDLE_A1Mini_PETG.3mf

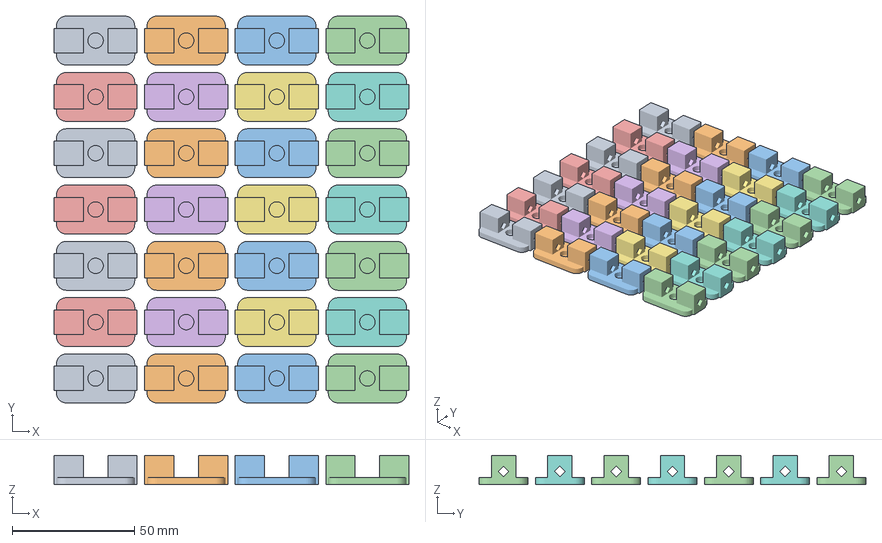
[picture p213: CAD file, 2026-09-19]
output/pvc_paper_gate/sliced/BATCH_CORD_SADDLE/BATCH_CORD_SADDLE_A1Mini_PETG.3mf
145.0 x 158.0 x 12.0 mm
CORD_SADDLE x 28
