rboyd/fpv-drone-racing-gate/output/pvc_paper_gate/sliced/BATCH_EDGE_SLEEVE/BATCH_EDGE_SLEEVE_A1Mini_PETG.3mf

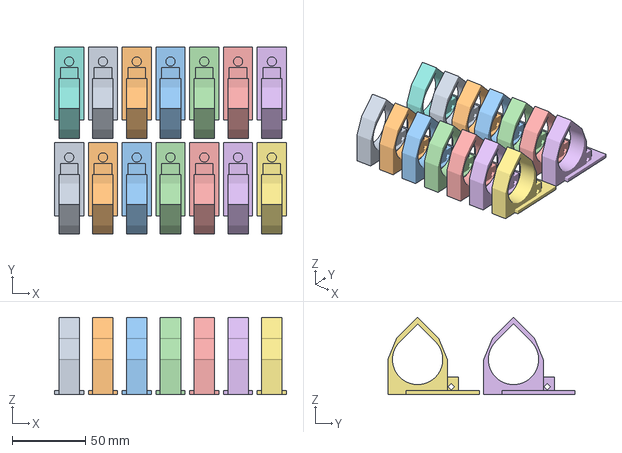
[picture p214: CAD file, 2026-09-19]
output/pvc_paper_gate/sliced/BATCH_EDGE_SLEEVE/BATCH_EDGE_SLEEVE_A1Mini_PETG.3mf
158.0 x 127.6 x 52.7 mm
EDGE_SLEEVE x 14
