rboyd/fpv-drone-racing-gate/output/full_paper_gate/Full_Gate_Assembly.pdf

FPV paper gate / reinforced frame + integrated cord cleats / fabrication prototype | 1

# Reinforced paper gate

## Assembly, cord adjustment and complete A1 Mini print queue

624 pieces / 10 types / 7.13 kg PETG / 295.0 printer-hours / 112 plate runs. Buy eight 1 kg spools including a 10% allowance. The earlier weak demo rail is superseded. Test the new braced bay first; this digital prototype is not yet physically validated.

Full-size face 2700 mm square; 1480.8 mm opening. Four rigid 2090.4 x 609.6 mm paper borders mount to one PVC square. Integral cleats retain pre-threaded 2.4 mm paracord. No zip ties or folding hinges. Upper PVC extensions route front guys above the paper.

FPV paper gate / reinforced frame + integrated cord cleats / fabrication prototype | 2

## Decision and cost

The complete reinforced design needs 7.13 kg PETG, 295.0 printer-hours, 112 manual plate runs, 624 pieces and 10 unique printed types. These are actual local Bambu Studio estimates, not solid-volume guesses. At a planning price of $20/kg, deposited PETG costs about $143; buying eight 1 kg spools is $160. A 10% allowance gives 7.84 kg, so eight spools are appropriate. One or two spools cannot make this design. Shipping, electricity, paper, magnets, PVC and hardware are additional.

This is a large printing commitment. The reinforced frame is not yet a compelling low-cost gate compared with a simpler PVC/Coroplast construction. The value of this iteration is a complete, inspectable load path and reusable test parts. Print the first bay before buying all gate materials. Keep optimization separate from an unproven reduction in the material around the sockets. At 12 printing hours/day the production queue alone takes about 25 days, plus plate handling/retries; continuous time is about 12.3 days.
The selected profile is A1 Mini, 0.4 mm nozzle, 0.20 mm layers, Generic PETG, textured PEI, 4 walls / 20% infill / supports off / no brim. All 21 supplied plate recipes sliced without warnings. Every mesh and plate fits 180 x 180 x 180 mm with at least 5 mm XY plate margin. Largest individual height is 37 mm. Ordinary flat plates are the production baseline. The earlier diagonal sacrificial stacks remain experiments; their separation and joint preservation have not been validated, so their overnight counts are not used in these estimates.

## What changed at the weak junction

The old cross socket left a nominal 4 x 5 mm neck. The new branch socket projects inward, with its rear pocket ending at local Y=28 mm; the continuous spine spans Y=-8..8 mm and is 12 mm deep. End receiver pads are 8 mm deep and 40 mm wide. A wide triangular root distributes the branch load. The 16 x 12 mm geometric section is not a tested strength multiplier. The replaceable key remains a deliberately small, physically unverified flexure; repeated click and load tests still matter.

Two raised cord-eye posts form a permanent two-horn cleat on every branch rail. Their 45-degree expanding caps and diamond through-holes are designed for support-free printing. Smooth the cord-contact edges. The updated holes accept 2.4 mm cord; this version is not specified for ordinary 4 mm 550 paracord.

## Print a test first

1. T01_BRANCH once: one reinforced branch, two click keys and one pad. Check both end and side sockets. Pull through the chosen cord, wrap the cleat and check release. The previous 0.40 mm fit coupon and magnet gauge remain useful, but this receiver has taller walls.
2. A full-width I-shaped member: T01 twice plus T02 once gives two branches, three rungs, four keys and two pads (11 pieces). The three rungs and four exposed 14 mm key middles join the two branches across a true 609.6 mm paper width.
3. One X-braced bay: T01 four times, T02 twice and T05 twice = 32 pieces: four branch rails, two plain rails, six rungs, twelve keys and eight pads. This is 436.943 x 609.6 mm. Add sixteen magnets, a 609.6 x 436.943 mm paper rectangle and one 3.3 m cord.
4. Add a PVC dock: T03 once adds two collar halves, one receiver and one tongue (36 total printed pieces). Add four M3 x 25 cap/pan bolts, two M3 x 25 flat-head bolts, six nuts and ten washers; use a 33.4 mm OD PVC offcut. Test-bay plus dock: 426.7 g, 18.79 h, nine plate runs.
5. Test a corner brace: T04 once supplies four V blocks and one crossing plate. Add two M4 x 80 and two M4 x 70 bolts, four nuts, eight washers, main/brace pipe offcuts. Try both +/-45 hole pairs.
6. Build one complete 2090.4 mm border only after the bay and dock behave well. Then finish the other three borders and the backbone. Test parts are production parts and can be reused. Full production queue

FPV paper gate / reinforced frame + integrated cord cleats / fabrication prototype | 3

quantities are gross: subtract accepted test pieces from it; do not print both queues blindly.

## Cord choice, threading and tightening

Use 2.4 mm 275 paracord as the handling-oriented prototype choice. Micro cord (about 1.18 mm) or braided polyester kite line is the lighter option. Supplier fiber recipes vary; 'paracord' is not a precise stretch specification. A line's advertised breaking load is not a working load for our printed cleat. The thicker cord makes threading and gripping easier, but knots and wraps consume more length than the earlier kite-line estimate.
Cut twenty identical 3.3 m lengths for the face and four 4 m lengths for the guys. Total 82 m; three 100-ft hanks provide 91.44 m. Face alone uses 66 m; calculated routes plus 600 mm knot/wrap allowance would use 63 m, but uniform 3.3 m cuts reduce assembly mistakes. Use a 3.3 m measuring mark on the bench, cut all twenty, and finish ends as appropriate for the purchased material. Do not cut only the visible diagonals.

Each bay uses one continuous cord and one tensioning station. Viewed from the rear with its long dimension horizontal, label its eyes LL (lower left), UR (upper right), LR (lower right), UL (upper left). Use the inward-facing post on each branch: the right post at the left end of the bay and the left post at the right end.

- Tie a double-overhand stopper larger than the eye at the starting end. Thread LL -> UR -> LR -> UL -> LL. This makes two crossing diagonals and two short return legs along the bay ends. At LL the two strands share the eye; keep them side-by-side. Leave the other end as the adjustment tail. For thinner kite/micro line, a stopper may pull through: use an appropriately sized backing washer or tie a fixed anchor loop around the post, then verify the anchor under load.
- Thread through the transverse holes, then turn outside the post; do not drag the line over the magnet pocket or across an exposed click hook. At the X crossing let one cord rest over the other, without a knot. Both cords remain behind the paper.
- Lay the border flat. Measure its two overall diagonals; make them equal before tensioning. Hand-feed slack through all four eyes, beginning at the stopper, then pull the tail. Friction at the bends means simply pulling hard on the last end does not tension every span evenly.
- Hold the tail with one hand. With the other, make two figure-eight turns around the two posts of the lower-left branch rail. Finish with a locking half-hitch around the last post: take the tail around the post, pass it under its own turn and snug it. Leave at least 100 mm tail, tucked under a wrap. The posts are the tensioning fixture; no separate screw, ratchet or loose part is required.
- Use only enough tension to remove slack. Stop if the rail bows or click gaps close unevenly. To adjust, hold the tail, lift off the half-hitch, unwrap, feed slack around the bay, and rewrap. Keep cords installed and lightly tensioned during transport.

There are five independent adjustments per border, twenty per gate. Independence prevents one long, friction-loaded lace from being difficult to balance. It also confines a slipped cord to one bay. Four purchased mini guy-line tensioners can simplify external setup; their cord range must include 2.4 mm. They are separate from the integral face cleats.

## Bench acceptance before scaling

Use the actual printer, PETG, magnets, paper and cord. Smooth burrs rather than enlarging latch shoulders. Seat the rigid guide runners and verify both catches; pinch both spring tips to release straight. Cycle representative joints 50 times, checking for whitening, cracks, missing hooks and growing play. A warning-free slice does not prove snap life or strength.

FPV paper gate / reinforced frame + integrated cord cleats / fabrication prototype | 4

For a cleat check, hang about 0.5 kg from a cord test tail, secure the wraps, mark the cord at the eye, and observe for 30 minutes and again after an overnight hold. Test ten releases/re-tensions. Reject visible sliding, groove damage, fraying or a bent post. On the full bay, apply modest diagonal hand loads in both directions; joints must remain seated and the rectangle must return square. This is a fit/slip screen, not a structural load certification. Recheck after warm outdoor exposure because PETG and cord can relax.

Check the dock on real pipe for axial sliding and rotation before it supports a border. The collar has 0.4 mm diametral clearance and an ear gap for clamping. Tighten evenly with washers, without crushing the plastic. Verify the brace V clamps grip both ODs. If either clamp slips before adequate grip is obtained, revise its seat/liner and repeat the test rather than overtightening.

Test magnet polarity before bonding. Rear magnet -> 0.4 mm rail skin -> paper -> 0.4 mm pad skin -> front magnet. Magnetic attraction depends on that complete gap and coating; 6 x 2 mm dimensions alone do not specify holding force. Test peeling, sideways slip, a fan and repeated pad removal. The paper is replaceable and can tear or soften when wet; it is not a structural brace.

## Assemble each full border on the bench

Make two 2090.4 mm long edges. Each uses fourteen 136.314 mm rail bodies and thirteen keys, whose exposed central spacers are 14 mm. At zero-based positions 0, 2, 5, 8, 11, 13 use EDGE_BRANCH; all other positions use EDGE_PLAIN. Turn the second long edge 180 degrees so all branches and D lugs face inward. The symmetric index pattern keeps the six branch axes aligned.

Join three identical 133.867 mm RUNG pieces for each of six crossmembers. Use four keys per crossmember: two internal and one at each end. Crossmember axes are 68.157, 368.786, 819.729, 1270.671, 1721.614 and 2022.243 mm from the panel end. Seat the second long edge evenly across all six members. Check overall dimensions 2090.4 x 609.6 mm and equal diagonals. Thread/tension the five X bays as above.

At the middle segment of crossmembers 2, 3, 4 and 5, attach a DOCK_TONGUE with two M3 x 25 flat-head screws through the paper face, flush in the countersinks. Nuts and washers sit behind the tongue flange. The outer two crossmembers have no dock. Keep all open latches accessible from the back.

Load 28 rear magnets into the long-edge D lugs and six into the middle-rung D lugs. Leave the twelve outer-rung pockets empty. Bond 34 matching magnets into 34 front pads. Cut one 2090.4 mm strip from the full 609.6 mm roll width, lay it against the smooth flat face and apply the pads without stretching the paper. Repeat for four identical borders. Magnets and cord stay with each transport border.

## PVC backbone and cut list

One square has 2090.4 mm centerline spacing. It lies about 98.9 mm behind the paper; four 3/4-inch corner braces lie another 60.475 mm behind it. Its lower centerline is 354.8 mm above ground and upper centerline 2445.2 mm. Paper bottom is 50 mm, top 2750 mm. Two guy masts extend the PVC to 3100 mm, so front guys clear the paper's upper edge. Masts are extensions of the single backing frame, not a second square.

Use 1-inch Schedule 40 PVC (33.4 mm OD), 3/4-inch braces (26.67 mm OD), four main-corner tees and two foot tees. Printed collars require these outside diameters, not 1-inch-OD tubing. Purchased fitting envelopes in Blender are illustrative; actual fitting engagement must be measured before cutting.

The example below assumes g=17.4625 mm from each fitting center to the fully seated pipe end. For a rail between two fittings, cut = center spacing - 2g. For a mast or foot with one fitting, cut = end-to-center length
- g. Mark seating depths, test a corner, and update cuts if the purchased fittings differ. Leave allowance for

FPV paper gate / reinforced frame + integrated cord cleats / fabrication prototype | 5

saw kerf; all listed stock nests have spare length.

- 4 x 2055.48 mm 1-inch Schedule 40 PVC, 33.4 mm OD: Square rails.
- 2 x 294.88 mm 1-inch Schedule 40 PVC: Lower legs.
- 2 x 637.34 mm 1-inch Schedule 40 PVC: Upper guy masts.
- 4 x 582.54 mm 1-inch Schedule 40 PVC: Grass half-feet.
- 4 x 1182.54 mm 1-inch Schedule 40 PVC: Hard-surface half-feet (swap for grass).
- 4 x 645.69 mm 3/4-inch Schedule 40 PVC, 26.67 mm OD: Corner braces.

For BOTH foot sets, buy six 10-ft sticks of 1-inch PVC: sticks 1-2 each yield one square rail + one mast + one leg; sticks 3-4 each yield one square rail + one grass half-foot; sticks 5-6 each yield two hard half-feet + one grass half-foot. One 10-ft stick of 3/4-inch yields all four braces. Grass-only can use five 1-inch sticks with the hard-foot cuts omitted.

Dry-assemble square and foot tees. Fully seat and mark each joint, square the frame, then drill 4.5 mm retention holes through each structural fitting/pipe interface for an M4 x 60 bolt and wingnut (18 occupied ports total). Orient bolts so they clear other sockets and feet. No solvent welding is required for this prototype. Add one M4 cross-bolt at about 3085 mm height on each mast; guy loops tie around the pipe below this stop. Six caps finish the four feet and two masts. Model hardware shows positional envelopes rather than thread detail.

## Corner braces: positively clamped at both ends

Each brace connects points 400 mm along the two adjoining square sides, with 40 mm pipe overhang past each crossing. Cut length is sqrt(400²+400²)+80 = 645.69 mm. Four braces need eight joints.

Each joint uses one 6 mm CROSS_PLATE and four identical V_BLOCKs. Put two V blocks around the 33.4 mm main pipe on one face of the plate; their flat outer faces and plate holes align. Use the plate's straight hole pair and two M4 x 80 bolts, washers and nuts. On the other face, rotate another V-block pair +/-45 degrees, align its holes with the appropriate diagonal pair, and clamp the 26.67 mm brace with two M4 x 70 bolts. The other diagonal holes stay empty. Tighten alternately until gripping; do not crush the pipe. Check both ends for rotation and axial slip. The main/brace axes are about 60.475 mm apart in depth. This replaces the earlier cross-lashing entirely.

## Align the sixteen face docks

Each dock uses two PVC_HALF_33 halves, one DOCK_SOCKET and one DOCK_TONGUE already fitted to the middle rung. Bolt the receiver's two base holes to the mounting pad on the inward collar half (two M3 x 25 cap/pan bolts, washers, nuts). Assemble the halves loosely around the appropriate square rail with two more M3 x 25 cap/pan bolts. The receiver mouth faces toward the gate front.

Use the finished border as the alignment jig: engage all four tongues in their receivers, place the paper rectangle at its intended pinwheel position, and slide/rotate the collars until all docks sit without strain. Then tighten the collar bolts evenly and label their positions. Do not independently measure and tighten sixteen collars and expect all four-panel interfaces to register perfectly.

Each face border snaps to the common PVC square at four points; neighboring face borders meet at butt seams. They do not need separate frame-to-frame corner snaps: the shared backbone locates them. The four 2090.4 x 609.6 rectangles rotate 90 degrees successively in a pinwheel, producing the 2700 mm outside / 1480.8 mm opening with no corner paper patches.

## Field setup and teardown

FPV paper gate / reinforced frame + integrated cord cleats / fabrication prototype | 6

Assemble marked PVC square rails and tees with retention bolts. Fit feet and masts, clamp the four corner braces, and check the square. On soil use the 1200 mm fore-aft foot set and four appropriate ground anchors. On hard ground use the 2400 mm foot set, rubber pads, and four weighed 15 kg ballast bags secured to the feet with straps. This 60 kg arrangement is a test starting point, not a certified wind limit or universal ballast prescription.

Tie front/rear guy pairs below the mast stop bolts and run them to stakes or the far foot ends. Start guy attachment at about 3075 mm: for the front hard-surface anchor 1150 mm from the pipe plane, the straight guy crosses the paper plane above 2810 mm, clearing the 2750 mm face top. Do not instead tie front guys to the 2445 mm upper square rail, which routes them through the paper. Keep guys outside the flight opening, tension evenly with optional mini line runners, and verify stakes/ballast do not move.

With two people, hold each rigid border against its four receivers, press the tongues home and visually check all hooks. Keep paper in the pinwheel layout. Adjust only slack X bays, check feet, all PVC fasteners, paper pads and the clear flight opening. Start testing in calm conditions, then controlled mild airflow; withdraw the paper face if it flaps, slips or destabilizes the frame. No wind rating is claimed for this prototype. As a sizing screen only, the 5.097 m² paper face at 5 m/s, air density 1.225 kg/m³ and assumed drag coefficient 1.3 gives about 101 N drag using the NASA drag equation. Doubling that force for a simple allowance gives about 284 N·m at 1.4 m height. Ideal centered 60 kg ballast with a 1.2 m lever arm gives 706 N·m, but this ignores joint flexibility and depends on ballast attachment; sliding would require friction coefficient above about 0.35. These assumptions are not a measured wind limit. Verify actual ground grip and assembly behavior.

For teardown, support a border, pinch both spring tips of each dock from behind and pull it forward evenly. Never pull against a still-latched dock. Leave each border's rails, X cords, tongue flanges and magnetic paper clamps assembled. Protect paper/pads for transport. Release guys and remove marked PVC bolts/brace clamps as needed. Stored borders are roughly 2.09 m long, 0.61 m wide and about 0.10 m deep with tongues; they are not intended to fold.

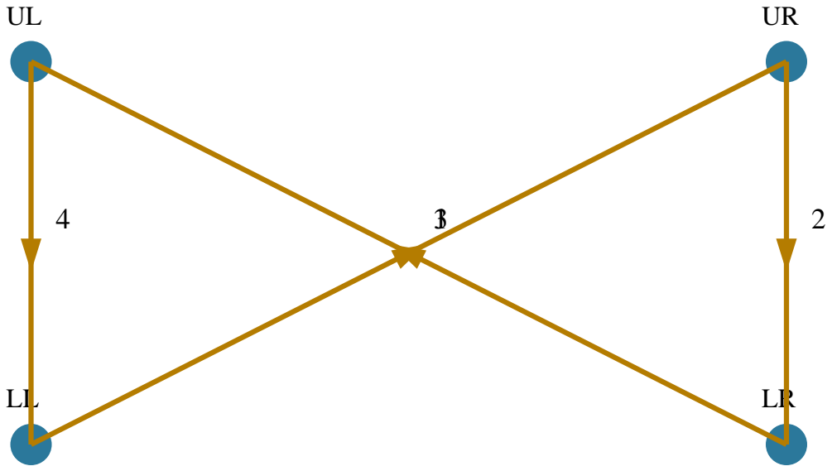
[picture p224: figure]

FPV paper gate / reinforced frame + integrated cord cleats / fabrication prototype | 7

# Thread one bay; repeat five times per border

Stopper at LL. Return tail to LL; pull, figure-eight twice, then lock with half-hitch.

The paths are schematic: feed through the transverse eyes, turn outside each post, and pass one diagonal over the other. Work slack around the loop before pulling the tail. The larger 3.3 m uniform cuts include cord for the cleat wraps, knots and a usable tail.

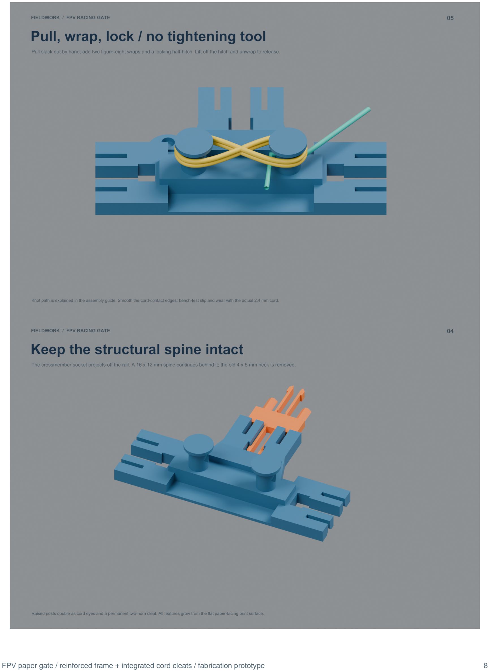
[picture p225: page 8]

FPV paper gate / reinforced frame + integrated cord cleats / fabrication prototype | 8

FPV paper gate / reinforced frame + integrated cord cleats / fabrication prototype | 9

# Printed parts and exact quantities

Part | Quantity | Print bounds mm
EDGE_PLAIN | 64 | 136.314 x 49.95 x 12.0
EDGE_BRANCH | 48 | 136.314 x 76.0 x 29.0
RUNG | 72 | 133.867 x 49.95 x 12.0
CLICK_KEY | 200 | 66.0 x 32.0 x 5.0
PAPER_PAD | 136 | 24.0 x 24.0 x 3.0
PVC_HALF_33 | 32 | 65.8 x 31.5 x 12.0
DOCK_SOCKET | 16 | 48.0 x 40.0 x 8.0
DOCK_TONGUE | 16 | 46.0 x 32.0 x 37.0
V_BLOCK | 32 | 24.0 x 64.0 x 22.0
CROSS_PLATE | 8 | 70.0 x 70.0 x 6.0
Every listed master fits the A1 Mini. Counts are for one complete gate; test parts can be credited against these quantities. The optional brace prototype also uses the same production pieces.

FPV paper gate / reinforced frame + integrated cord cleats / fabrication prototype | 10

# Purchased hardware and stock

Item | Qty | Use
6 x 2 mm neodymium magnets | 272 | 136 matched pairs; 34 pairs per border
M3 x 25 cap/pan-head bolts | 64 | 32 collar-ear + 32 receiver-pad bolts
M3 x 25 flat-head bolts | 32 | 2 through each of 16 rung-to-tongue joints
M3 nuts | 96 | Workshop attachment
M3 washers | 160 | Two per cap/pan bolt, one at nut per flat-head bolt
M4 x 80 bolts | 16 | Two per main-pipe V clamp
M4 x 70 bolts | 16 | Two per brace-pipe V clamp
M4 nuts | 32 | For V clamps
M4 washers for V clamps | 64 | One under each head and nut
M4 x 60 bolts + wingnuts | 20 | 18 PVC fitting ports + 2 guy-loop stop bolts
M4 washers for PVC bolts | 40 | One under each head and nut
1-inch socket PVC tees | 6 | 4 square corners and 2 feet
1-inch PVC end caps | 6 | 4 feet and 2 upper masts
1-inch PVC, 10 ft stock | 6 | Enough for both foot sets with nesting described below
3/4-inch PVC, 10 ft stock | 1 | Four 645.69 mm corner braces
2.4 mm 275 paracord, 100 ft | 3 | 20 x 3.3 m face cords + 4 x 4 m guys = 82 m; 9.44 m spare
Purchased 1-2.5 mm guy-line tensioners | 4 | Optional CL266 or equivalent; face cleats are integral
24-inch x 100-ft paper roll | 1 | Four 2090.4 mm pieces/gate; three gates plus two spare strips/roll
Ground stakes | 4 | Soil setup; suitable holding depends on actual ground
15 kg weighed ballast bags | 4 | Hard surface starting test configuration, 60 kg total
Ballast retaining straps | 4 | Secure bags to feet; no zip ties
Rubber foot pads | 4 | Hard-surface friction protection
Magnet-retaining adhesive | 1 | Compatible with PETG and magnet coating; use manufacturer cure time

FPV paper gate / reinforced frame + integrated cord cleats / fabrication prototype | 11

# Complete print queue

Open the identically named prepared 3MF in sliced/. This table lists 16 production recipes; Every_Plate_Run.csv expands them into all 112 manual plate runs. Test plate files begin T, and are additional until their pieces are credited to the production quantities.

Recipe | Runs | Parts/run | g/run | min/run
Q_EDGE_PLAIN_FULL | 21 | 3 | 73.2 | 170
Q_EDGE_PLAIN_TAIL | 1 | 1 | 24.5 | 62
Q_EDGE_BRANCH_FULL | 24 | 2 | 73.4 | 180
Q_RUNG_FULL | 24 | 3 | 73.4 | 175
Q_CLICK_KEY_FULL | 25 | 8 | 26.9 | 86
Q_PAPER_PAD_FULL | 3 | 36 | 53.6 | 140
Q_PAPER_PAD_TAIL | 1 | 28 | 41.7 | 110
Q_PVC_HALF_33_FULL | 3 | 10 | 72.3 | 200
Q_PVC_HALF_33_TAIL | 1 | 2 | 14.5 | 46
Q_DOCK_SOCKET_FULL | 1 | 12 | 106.7 | 256
Q_DOCK_SOCKET_TAIL | 1 | 4 | 35.6 | 90
Q_DOCK_TONGUE_FULL | 1 | 12 | 101.8 | 278
Q_DOCK_TONGUE_TAIL | 1 | 4 | 34.0 | 100
Q_V_BLOCK_FULL | 2 | 12 | 194.4 | 441
Q_V_BLOCK_TAIL | 1 | 8 | 129.6 | 297
Q_CROSS_PLATE_FULL | 2 | 4 | 70.8 | 155


FPV paper gate / reinforced frame + integrated cord cleats / fabrication prototype | 12

# Assembly views

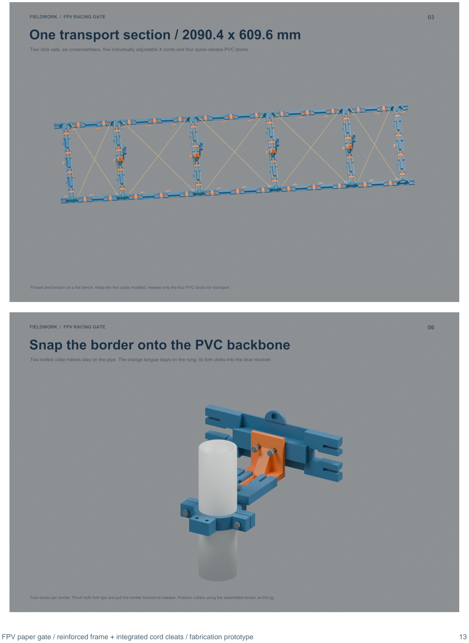
[picture p226: page 13]

FPV paper gate / reinforced frame + integrated cord cleats / fabrication prototype | 13


FPV paper gate / reinforced frame + integrated cord cleats / fabrication prototype | 14

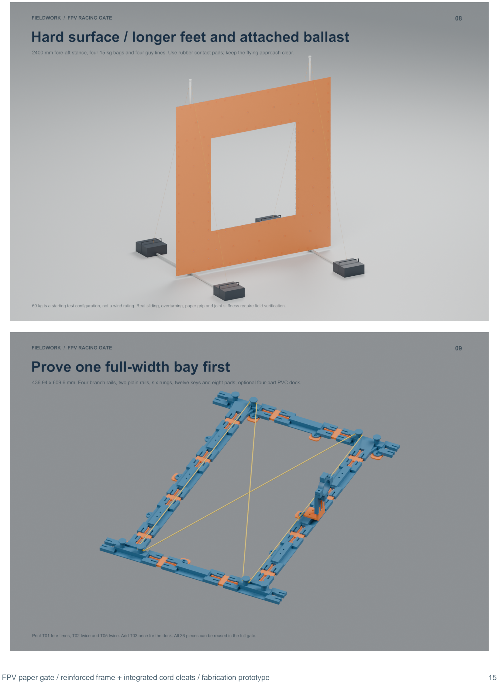
[picture p227: page 15]

FPV paper gate / reinforced frame + integrated cord cleats / fabrication prototype | 15

FPV paper gate / reinforced frame + integrated cord cleats / fabrication prototype | 16

## Validation and sources

See README.md for complete source links, the physical test procedure and verification limits. All supplied slices are support-free and warning-free. Scene counts match the printed bill of materials. No physical fatigue, wind or magnetic-holding tests have been performed.
