rboyd/fpv-drone-racing-gate/output/a1_full_size/Assembly_and_Test_Instructions.pdf

FIELDWORK / FPV RACING GATE | ASSEMBLY & TEST MANUAL

# Whole-sheet FPV racing gate

Part 1: nine-piece concept print / Part 2: complete gate

A1 Mini · Two-channel revision · Prototype instructions · 17 Sep 2026 | 01
A1 | A2 | A3 | B1

D3

B2

B3

C3 | C2 | C1

D1

D2

Current design
12 whole 22 × 28 inch sheets
4 rigid borders, about 2.15 m long
1 PVC backing frame + 4 braces
2 channel types; 19 printed types total

Start small. Print the nine-piece plate, check the interfaces, then build one complete sheet bay before producing the remaining bays.

Geometry fits the A1 Mini. Snap durability, assembled stiffness and outdoor performance still need physical testing.

### Use this manual at the workbench

Part 1 — Print, assemble and test nine pieces | 2
Part 2 — Full gate: inventory and workshop assembly | 7
PVC frame, printed brace joints and both bases | 13
Field setup, inspection and teardown | 16

All dimensions are millimeters unless stated otherwise. Illustrations are not cutting templates. Printed part names match the STL filenames.

Orange = channel/rib/snap/pipe-saddle parts. Blue = locating nodes, caps and links. Exact CAD illustrations are identified in captions; flat diagrams explain layout and tie routing.

Companion files: BOM.csv, PVC_CUT_LIST.csv, CHANNEL_ASSEMBLY_MAP.json and MINIMAL_TEST_PARTS.csv in output/a1_full_size. This manual uses the current LONG / SHORT channels, not the retired CHANNEL_01–09 files.

FIELDWORK / FPV RACING GATE | PART 1 / PREPARE

# Print nine pieces

One of each part. Reuse the channels between the straight and corner tests.

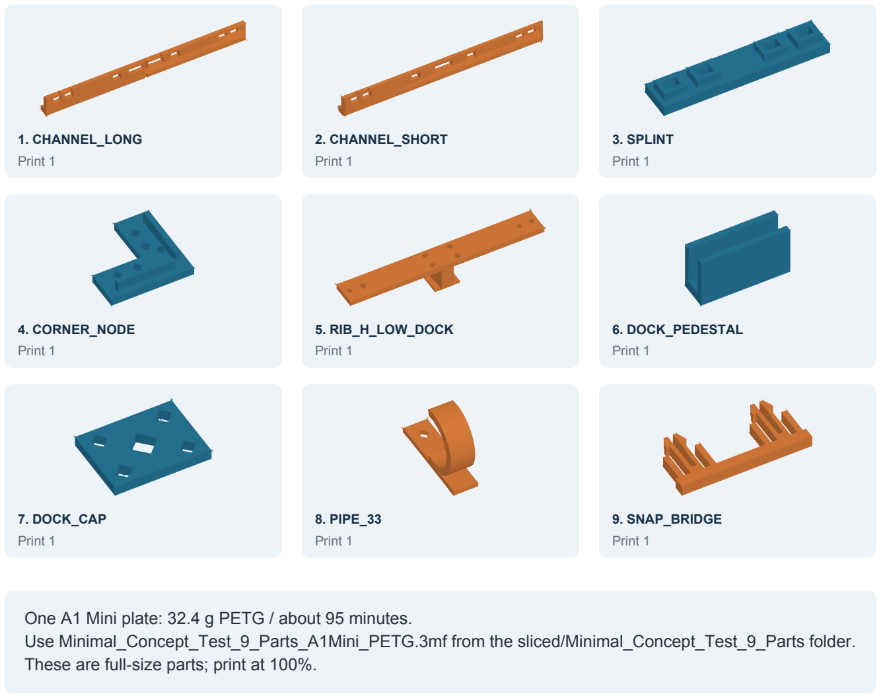
[picture p228: figure]
1. CHANNEL_LONG; Print 1; 2. CHANNEL_SHORT; 3. SPLINT; 4. CORNER_NODE; 5. RIB_H_LOW_DOCK; 6. DOCK_PEDESTAL; 7. DOCK_CAP; 8. PIPE_33; 9. SNAP_BRIDGE

A1 Mini · Two-channel revision · Prototype instructions · 17 Sep 2026 | 02

One A1 Mini plate: 32.4 g PETG / about 95 minutes.
Use Minimal_Concept_Test_9_Parts_A1Mini_PETG.3mf from the sliced/Minimal_Concept_Test_9_Parts folder. These are full-size parts; print at 100%.

Settings: A1 Mini, 0.4 mm nozzle, 0.20 mm layers, 3 walls, 15% infill, Generic PETG, Textured PEI Plate, supports off. Keep the supplied orientations. Check the printer, filament and plate before starting.

Bring: actual posterboard; a short 1-inch nominal PVC offcut (33.40 mm OD); six 2.5 mm-wide ties; one roughly 3.6 × 250 mm keeper tie; ruler or calipers; flush cutters; a deburring tool. Releasable ties help when reusing the channels.

After printing: clear strings and brim/first-layer burrs from slots, windows and snap hooks. Keep the original sizes. Do not scale the whole kit to correct one tight interface.

FIELDWORK / FPV RACING GATE | PART 1 / TEST 1–2

# Paper fit, then a straight splice

Use CHANNEL_LONG + CHANNEL_SHORT + SPLINT. Two narrow ties.

A1 Mini · Two-channel revision · Prototype instructions · 17 Sep 2026 | 03

### 0.8 mm paper slot

Front lips face the flying side. The deep spine and mounting windows sit behind the paper. Slot shown with approximately 0.4 mm stock.

1

Slide a sheet edge into each channel. It should enter without creasing or forcing the lips apart. Check the paper near both ends. Use the actual sheet; no cutting or punching is needed.

2

Align the channels end-to-end, with slots facing the same way and a 0.2 mm gap. A long-to-short joint is only a test combination; production joins equal-length pieces.

Exact CAD: splint lifted away to show the four hollow locating bosses.

3

Seat all four splint bosses in the end windows. The flat splint body sits on the inward side of the rail spine. Thread one tie through the two bosses on the left, and one through the two on the right. Keep ties out of the paper slot.

One tie per side | Joint gap

Pass: bosses seat fully; ties snug the splint without crushing the spine; gentle hand bending/sliding does not open the joint or release a boss. Recheck that paper still slides.

If it binds: remove burrs and inspect the boss/window fit. Do not force or trim away a locating shoulder. Record the mismatch on page 6.

FIELDWORK / FPV RACING GATE | PART 1 / TEST 3

# Reconfigure as a frame corner

Remove the splint. Reuse the two channels with CORNER_NODE and two fresh/reusable ties.

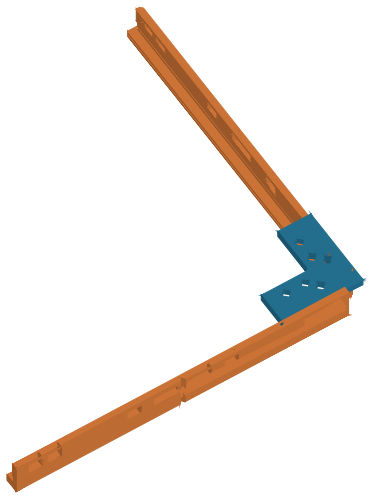
[picture p229: figure]

A1 Mini · Two-channel revision · Prototype instructions · 17 Sep 2026 | 04

Exact CAD: the node is behind the paper, inside the corner.

1

Place the rails at 90° with both slots opening into the paper area. Align their outside spine lines to define a virtual corner. Each channel begins 6.1 mm from that corner; do not jam the two channel tips together.

2

Put the blue L-shaped node on the rear of the rails, inside the corner. Its locating fences point toward the paper and sit against the inward faces of the rail spines.

3

Tie one arm of the node to each rail. Use the node hole about 14.1 mm from the virtual corner and the matching spine window. The other paired holes are reserved for full-gate bridges.

4

Fit a posterboard corner into both slots. Check squareness with a ruler or square, then gently try to rack the joint. Keep tie heads and cut tails behind the paper.

Pass: the corner remains square under gentle handling; paper fits both grooves without folding; the node stays seated. This checks a sheet-frame corner, not the removable seam between full borders.

If the node will not seat, check rail orientation and the 6.1 mm setback first. Loosen ties and align the fences before retightening; do not use tie tension to force misaligned parts into place.

FIELDWORK / FPV RACING GATE | PART 1 / TEST 4

# Build the complete PVC dock

Five parts: docking rib, pedestal, cap, pipe saddle and snap bridge.

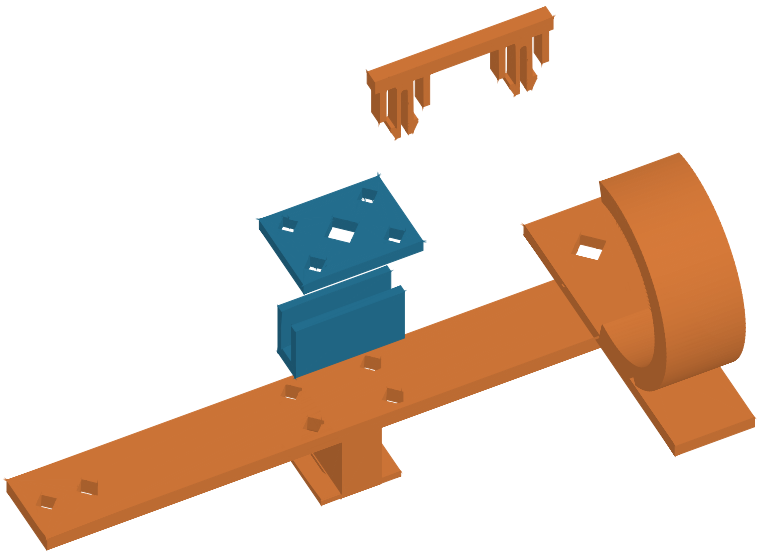
[picture p230: figure]

A1 Mini · Two-channel revision · Prototype instructions · 17 Sep 2026 | 05

### 9 SNAP_BRIDGE

### 7 DOCK_CAP

### 6 DOCK_PEDESTAL

### 8 PIPE_33

### 5 RIB_H_LOW_DOCK

Numbers match page 2

Exact CAD, exploded for clarity. Pipe saddle shifted aside; final socket spacing is 24 mm.

1

Hold RIB_H_LOW_DOCK with its small paper-contact shoe pointing toward the future paper face. Use this rib, which has four extra holes around its center; the ordinary low rib does not.

2

Center DOCK_PEDESTAL on the back of the rib: its solid base on the rib, two walls upward. Put DOCK_CAP on those walls. The cap’s diamond socket must open into the hollow space beneath it.

3

Use two narrow ties through the cap and rib’s matching holes—one at each end of the pedestal. Tighten evenly. Do not run a strap through the central snap opening.

4

Seat PIPE_33 around the actual PVC offcut. Add the long keeper tie around pipe and saddle, near an axial edge so it clears the snap socket and hooks. Keep its head out of the release path. The open C shape alone is not the retainer.

5

Bring the cap and saddle socket centers 24 mm apart, with their rear faces level. Insert SNAP_BRIDGE from the rear. Press its solid crossbar until both rigid stop pairs seat and the hooks emerge through the sockets.

Pass: both ends latch, the cap stays on its pedestal, and the fork tips have free space behind the socket plates. Gentle pulls do not release the dock or rotate the saddle on the pipe.

FIELDWORK / FPV RACING GATE | PART 1 / TEST & RECORD

# Release it, repeat it, record it

A fit-and-handling check—not a structural load or wind rating.

A1 Mini · Two-channel revision · Prototype instructions · 17 Sep 2026 | 06

Release one end at a time. Pinch that fork’s two prongs inward so the hooks clear the socket. Lift that end slightly, then release the other. Hold the nearby rigid parts; do not lever the crossbar until a prong bends.

Check access in the assembled dock, not just loose parts. Blunt tweezers can diagnose tight clearance, but record if tools are needed. Do not claim quick hand release until it works physically.

1

As an initial screening exercise, try 20 insert/release cycles. This is a chosen workshop check, not a certified durability threshold. Stop for cracks, whitening, permanent bend, binding or unintended release.

2

After cycling, repeat a gentle hand pull and the pipe-slip check. Run paper over the rib’s contact shoe and inspect for catching or scratching. Recheck every tie and its clearance.

### Fill in after printing

Check | Pass / issue / measurement
Filament / nozzle / layer height | _____________________________________
Measured sheet thickness / pipe OD | _____________________________________
Paper slides in both channels | _____________________________________
Splice bosses seat; joint stays together | _____________________________________
Corner fits; remains square by hand | _____________________________________
Dock seats; pipe does not rotate/slip | _____________________________________
Snap cycles completed / release by hand? | _____________________________________
Cracks / permanent bend / paper marking | _____________________________________

Next: correct any fit failure, then make one complete sheet bay (pages 9–11) and check paper flutter, cap removal and racking. The nine pieces cannot test a full border’s stiffness.

Optional samples: add BRACE_LINK_45 + PIPE_27 for a brace end (reuse PIPE_33). Add RIB_H_HIGH, RIB_V_HIGH, RIB_CROSS and RIB_ANCHOR for rib-joint tests; reuse the docking rib between those checks.

# The full gate at a glance

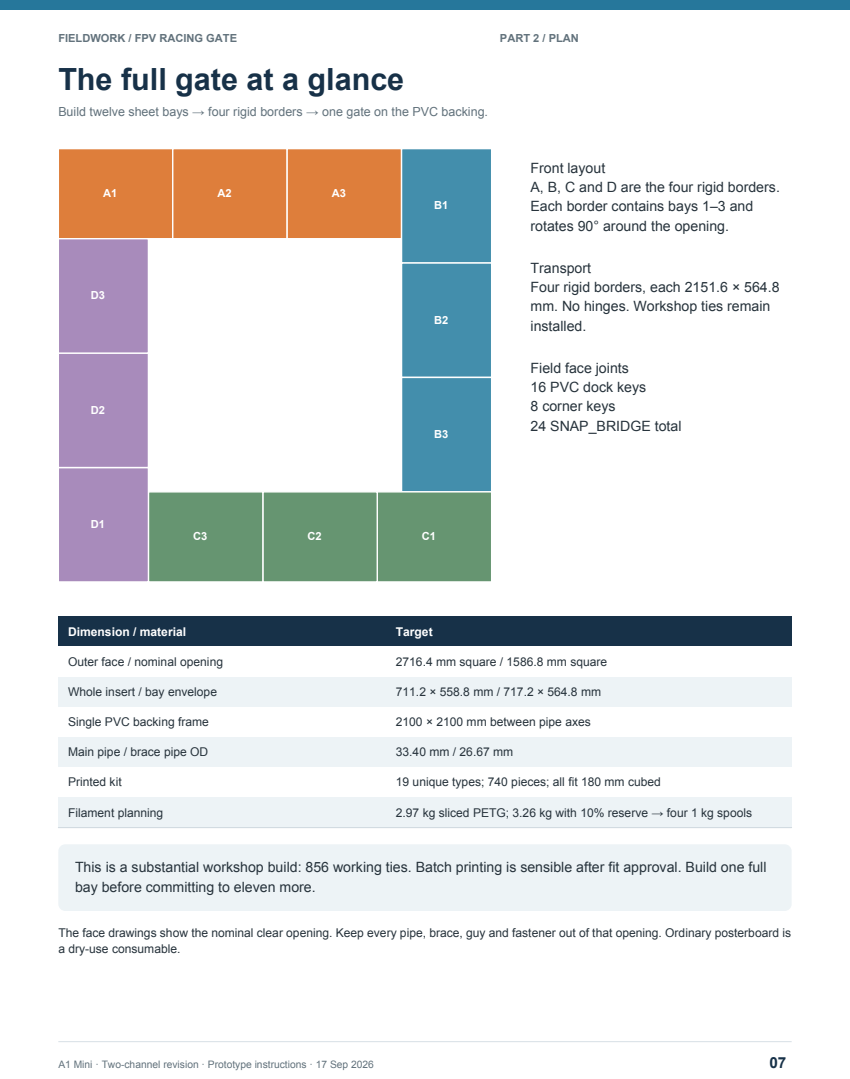
[picture p231: page 7]
FIELDWORK / FPV RACING GATE; PART 2 / PLAN; A1 Mini · Two-channel revision · Prototype instructions · 17 Sep 2026; Dimension / material; Target; Outer face / nominal opening; 2716.4 mm square / 1586.8 mm square; Whole insert / bay envelope; Single PVC backing frame; 2100 × 2100 mm between pipe axes; Main pipe / brace pipe OD; Printed kit; 19 unique types; 740 pieces; all fit 180 mm cubed; Filament planning; 2.97 kg sliced PETG; 3.26 kg with 10% reserve → four 1 kg spools

Build twelve sheet bays → four rigid borders → one gate on the PVC backing.

Front layout
A, B, C and D are the four rigid borders.
Each border contains bays 1–3 and
rotates 90° around the opening.

Transport
Four rigid borders, each 2151.6 × 564.8
mm. No hinges. Workshop ties remain
installed.

Field face joints
16 PVC dock keys
8 corner keys
24 SNAP_BRIDGE total

This is a substantial workshop build: 856 working ties. Batch printing is sensible after fit approval. Build one full
bay before committing to eleven more.

The face drawings show the nominal clear opening. Keep every pipe, brace, guy and fastener out of that opening. Ordinary posterboard is
a dry-use consumable.

FIELDWORK / FPV RACING GATE | PART 2 / INVENTORY

# Print and purchase checklist

Totals are per gate, including all printed face, dock and brace connectors.

A1 Mini · Two-channel revision · Prototype instructions · 17 Sep 2026 | 08
STL name | Qty | Print X × Y × Z (mm)
CHANNEL_LONG | 120 | 140.84 × 14 × 6
CHANNEL_SHORT | 96 | 138 × 14 × 6
SPLINT | 168 | 40 × 8 × 4.4
CORNER_NODE | 48 | 34 × 34 × 7
RIB_ANCHOR | 48 | 40 × 26 × 7
RIB_CROSS | 12 | 48 × 48 × 6
BORDER_BRIDGE | 16 | 60 × 12 × 3
FIELD_RECEIVER | 16 | 40 × 24 × 6.4
SNAP_BRIDGE | 24 | 36 × 16.8 × 3
RIB_H_LOW | 32 | 126.867 × 17.825 × 12
RIB_H_LOW_DOCK | 16 | 126.867 × 17.825 × 16
RIB_H_HIGH | 24 | 126.867 × 20.825 × 12
RIB_V_LOW | 24 | 144.2 × 17.825 × 12
RIB_V_HIGH | 24 | 144.2 × 20.825 × 12
PIPE_33 | 24 | 61 × 43.899 × 16
PIPE_27 | 8 | 44 × 35.8 × 16
DOCK_CAP | 16 | 24 × 18 × 2.4
DOCK_PEDESTAL | 16 | 7 × 12.35 × 22
BRACE_LINK_45 | 8 | 103.51 × 127.51 × 3

Face supplies: 12 whole posterboard sheets; 744 standard 2.5 mm ties; 48 narrow releasable ties (or removable cord loops); 32 pipe keeper ties about 3.6 × 250 mm; 32 brace-link ties about 3.6 × 150 mm; 20 m of smooth 0.8 mm front cord. Buy spare ties.

PVC fittings: 2 upper elbows, 2 lower frame tees, 2 foot tees and 4 end caps, all 1 inch nominal. Pipe cuts are on page 13. Retain working sockets positively; fittings must not pull apart during handling.

Anchoring supplies: four guy lines (about 4 m each), suitable ground anchors for soil; or four strapped ballast bags with anti-slip pads for hard surfaces. The base arrangement and test limits are on page 15.

FIELDWORK / FPV RACING GATE | PART 2 / WORKSHOP 1

# Build one sheet-frame perimeter

Work face-down on a flat surface. The same two channel types serve every bay.

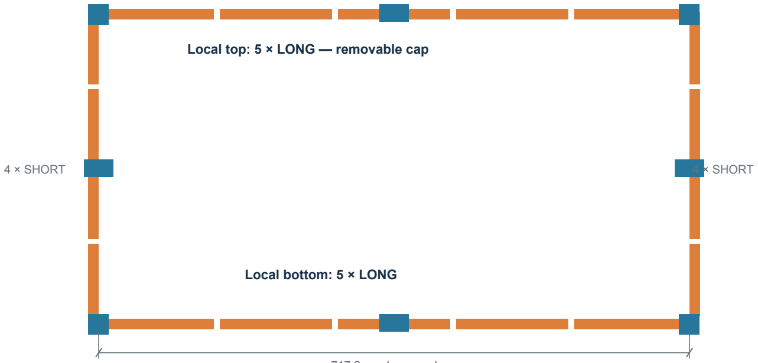
[picture p232: figure]
5 × CHANNEL_LONG; 5 × CHANNEL_LONG — removable top cap; Local top: 5 × LONG — removable cap; Local bottom: 5 × LONG; 4 × SHORT

A1 Mini · Two-channel revision · Prototype instructions · 17 Sep 2026 | 09

717.2 mm bay envelope

1

Make two long edge chains of five LONG channels and two short chains of four SHORT channels. Fit a SPLINT and two ties at every straight joint. Keep a 0.2 mm body gap. Per bay: 18 channels, 14 splints, 28 splice ties.

2

Fit four CORNER_NODE parts as on page 4. Set the outside reference rectangle to 717.2 × 564.8 mm. Each channel chain starts 6.1 mm from its virtual corner. Face lips point toward the tabletop; spine and nodes face you.

3

Add one RIB_ANCHOR at the midpoint of each edge: 358.6 mm on long edges, 282.4 mm on short edges. Its fence locates against the rail’s inward face. Use two rail ties per anchor.

4

Use releasable fasteners at the top cap’s two corner-to-top-rail joints and the top anchor’s two rail ties: four releasable ties per bay. The corner nodes remain attached to the side rails when the cap is lifted.

Check: square corners, continuous paper slots, fully seated splice bosses and no tie across the paper groove. Ordinary ties may be cut for the first test; use removable fasteners for routine paper changes.

FIELDWORK / FPV RACING GATE | PART 2 / WORKSHOP 2

# Add the stepped rear ribs

“Horizontal” and “vertical” refer to a bay lying landscape on the bench.

A1 Mini · Two-channel revision · Prototype instructions · 17 Sep 2026 | 10
LOW → HIGH → LOW | LOW ← HIGH ← LOW

Outer edge → LOW → HIGH → center

Outer edge → LOW → HIGH → center

Raised vertical seats

1

Set RIB_CROSS at the bay center (358.6, 282.4). Its horizontal seats are lower; its vertical seats are 3 mm higher. The ribs cross at different heights and must not be forced into one plane.

2

Each horizontal half, from edge to center, is H_LOW → H_HIGH → H_LOW. Each vertical half is V_LOW → V_HIGH. Keep all contact shoes pointing toward the paper. Substitute docking low ribs only at the stations on page 12.

3

Overlap adjacent beam ends by 16 mm. Align the two hole pairs and thread one tie through both layers, returning through the second hole. Repeat at each anchor and each cross-node attachment. The holes are 8 mm apart.

16 mm overlap (schematic)

Per bay: six horizontal pieces + four vertical pieces, four anchors, one cross. Rib connections use 14 ties: 6 intermediate laps, 4 outer endpoints and 4 cross-node attachments.

Check: both holes align at every lap; low/high shoes reach the same paper plane; opposing ends stop short of each other at the center. A tightly tied joint must not crush or bow the beam.

FIELDWORK / FPV RACING GATE | PART 2 / WORKSHOP 3

# Insert the paper and retention cord

Keep every 22 × 28 inch sheet whole. No holes through the posterboard.

A1 Mini · Two-channel revision · Prototype instructions · 17 Sep 2026 | 11

Lift top cap

Two front cord spans

Rear ribs and shoes sit behind this sheet

1

Open the four releasable top-cap ties and lift off the complete five-piece cap chain. Keep its four internal splints tied. The top rib anchor may stay on its rib; it clears the paper plane.

2

Slide the whole sheet down the two side grooves and into the bottom groove. Support the sheet to avoid buckling. Refit the top cap and its four releasable ties. Do not tighten so hard that the paper slot closes.

3

Run smooth 0.8 mm cord across the front in both directions, through the edge midpoints. At each end, use the V-notch, wrap around the outside edge, and tie off at a rear-spine window. The short-edge notch lies at the central channel joint.

4

Tension only enough to retain the sheet toward the rear contact shoes. Do not bow the frame or indent the paper. Keep knots and tie tails behind the face. Leave the top-cap cord end easy to undo for replacement.

One-bay test before production: lift and gently rack the framed sheet; check that it stays square, paper remains captured, cords do not cut the edge, and the top cap removes/refits without damage. Record any flutter or slack.

Contact shoes and front cord oppose movement in both directions. This does not make the paper weatherproof. Let the one-bay result determine whether to continue with the full gate.

FIELDWORK / FPV RACING GATE | PART 2 / WORKSHOP 4

# Join three bays into a rigid border

Repeat this border four times. All coordinates below are viewed from the rear, face-down.

A1 Mini · Two-channel revision · Prototype instructions · 17 Sep 2026 | 12
BAY 1 | BAY 2 | BAY 3
Green: field receivers | Blue: fixed cell bridges

1

Lay out bays 1–3 side by side. At each seam, fit a BORDER_BRIDGE near the top and another near the bottom, across the neighboring corner nodes. Thread two ties per bridge through the spare paired node holes. Per border: four bridges, eight ties.

2

Install four docking ribs at the stations below. Fit a pedestal and cap to each as on page 5 (two ties per dock). The cap socket centers lie on the bay midline, 282.4 mm from its bottom edge.

Bay / horizontal half-rib | Replace this LOW piece | Socket X from border left
1 / right half | Innermost, next to cross | 424.03 mm
2 / left half | Outermost, next to anchor | 788.63 mm
2 / right half | Outermost, next to anchor | 1362.97 mm
3 / left half | Innermost, next to cross | 1727.57 mm

3

Add four FIELD_RECEIVER parts: two on bay 1’s bottom edge at X = 64 and 500.8 mm; two on bay 3’s right edge at Y = 64 and 500.8 mm. Seat fences inward and use two rail ties each. These are positions along a 564.8 mm field seam—not the full 717.2 mm bay width.

Check: border size 2151.6 × 564.8 mm; three sheets remain removable; all four dock sockets align to one straight line; all four field receivers face rearward. Do not remove the fixed bridge ties for transport.

FIELDWORK / FPV RACING GATE | PART 2 / PVC 1

# Build the single backing frame

All main-frame and foot fittings are purchased 1-inch nominal PVC fittings.

A1 Mini · Two-channel revision · Prototype instructions · 17 Sep 2026 | 13

2100 mm between axes

Upper elbows × 2

Lower tees × 2

Legs continue down

Foot tees × 2

Cut item | Qty | Example length | Nominal PVC
Frame sides | 4 | 2065.08 mm | 1 inch
Legs | 2 | 298.28 mm | 1 inch
Grass half-feet | 4 | 582.54 mm | 1 inch
Hard-floor half-feet | 4 | 1182.54 mm | 1 inch; instead of short feet
Diagonal braces | 4 | 425.69 mm | 3/4 inch

Measure fittings before cutting. For socketed pipes: cut length = required fitting-center span − take-up at each end. Take-up = center-to-mouth distance − actual pipe engagement. Examples use 17.4625 mm per fitting end; actual dry engagement may differ.

Square the 2100 mm frame, then positively retain working sockets with the established screw/pin or permanent-joint method. The lower tees continue to two legs; foot tees turn across the frame plane and receive two half-feet each. Add four end caps.

Keep the feet centered under the frame. With foot axes 25 mm below face datum, the leg center span is 333.2 mm. The main pipe axes are 55 mm behind the front face. The example cuts are not permission to substitute an unmeasured fitting.

FIELDWORK / FPV RACING GATE | PART 2 / PVC 2

# Install all eight printed brace joints

Each of the four diagonal braces has this connection at both ends.

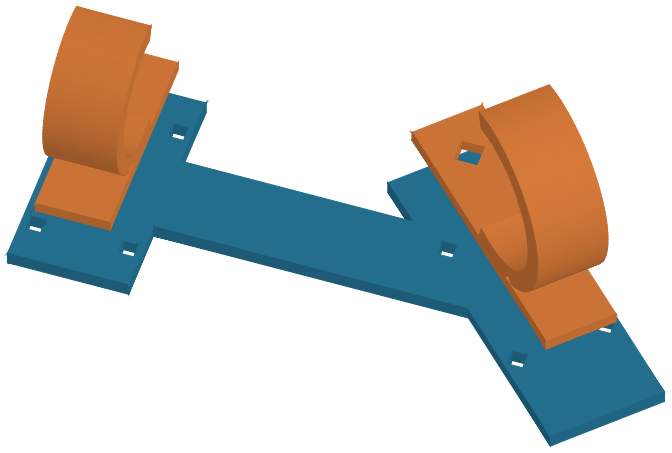
[picture p233: figure]

A1 Mini · Two-channel revision · Prototype instructions · 17 Sep 2026 | 14

Exact CAD, saddles lifted off the link. Main-pipe saddle is larger; brace saddle is smaller.

1

Mark points 400 mm from each theoretical main-frame corner along its two pipe axes. Those points define the diagonal centerline. The 400 × 400 mm diagonal is 565.7 mm long.

2

Trim the brace tube 70 mm back from each theoretical endpoint: 425.7 mm actual tube length. At either end, its saddle center lies 90 mm from the theoretical main-pipe intersection, or 20 mm from the trimmed tube end.

3

Put PIPE_33 and PIPE_27 on the same face of BRACE_LINK_45, over its two pads. Use two heavy ties per pad—four link ties total—through the pad slots and around each saddle foot. Flip the reversible flat link as required at mirrored corners.

4

Seat the main pipe and brace pipe in their saddles. Add one keeper tie around each saddle and its pipe. Check pipe seating and the frame’s squareness before tightening. A finished endpoint has four link ties plus two pipe keepers.

Gate totals: 8 links + 8 main-pipe saddles + 8 brace saddles + 32 link ties + 16 brace pipe keepers. The other 16 PIPE_33 saddles and 16 keepers belong to the removable face docks.

Use releasable pipe keepers if the PVC square must break down for transport. Retain the link-to-saddle ties. The printed joints position the brace; verify resistance to pipe sliding and joint rotation physically.

FIELDWORK / FPV RACING GATE | PART 2 / BASES

# Set up for grass or hard surfaces

Anchor the PVC structure before attaching the paper face. These are prototype base arrangements.

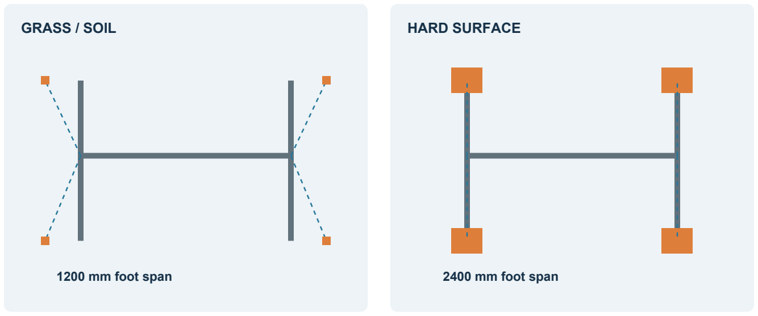
[picture p234: figure]
GRASS / SOIL; 1200 mm foot span; HARD SURFACE; 2400 mm foot span

A1 Mini · Two-channel revision · Prototype instructions · 17 Sep 2026 | 15

### Grass: short feet + four opposing guys

Use four short half-feet, giving 1200 mm fore–aft span at each foot. Tie four guys around the upper PVC corner fittings, two forward and two rearward. Put anchors outside the opening and away from the flight line; the prior layout uses X ≈ ±1600 mm and ±1200 mm fore–aft from the frame plane.

Use suitable anchors for the actual soil. Check each installed anchor in its guy direction for movement. Keep lines only taut enough to brace the frame; do not bow the PVC. Mark the lines and anchors visibly.

### Hard surface: long feet + strapped ballast + guys

Swap in the long half-feet for 2400 mm fore–aft span. Put a weighed 15 kg bag near each foot end (four bags / 60 kg as an initial trial arrangement), with anti-slip material beneath. Strap each bag to its actual foot pipe. Attach its guy to the same foot end, about 1150 mm from the center.

60 kg is a starting test arrangement, not a validated wind rating. Check sliding, foot lift, bag/strap movement, socket retention and frame distortion under gentle load in both directions. A loose bag placed nearby is not an anchored foot.

Both setups need physical site checks. If the frame moves, an anchor loosens, or paper/joins start to fail, stop and lower the gate. No operating wind-speed limit has been established for this revision.

FIELDWORK / FPV RACING GATE | PART 2 / FIELD

# Attach, inspect and pack away

Four rigid face borders. Twenty-four removable snap bridges.

A1 Mini · Two-channel revision · Prototype instructions · 17 Sep 2026 | 16

1 With the PVC backing supported and anchored, use two people to position a rigid border. Seat its four PIPE_33 saddles on the corresponding pipe and install/verify their keeper ties. Align the four cap/saddle sockets, then install four SNAP_BRIDGE keys as on page 5.

2

Repeat for the other three borders in the pinwheel layout on page 7. Adjacent border receivers meet at each field seam. Fit two SNAP_BRIDGE keys per seam, at 64 mm from each end of the 564.8 mm seam. Total: 16 dock keys + 8 seam keys.

### Before the first flight

All 24 keys fully seated; no cracked, permanently bent or partly engaged snap prongs.

All 32 pipe keeper ties installed; eight brace links secure; PVC sockets retained.

Every sheet captured; top caps secure; front cord lightly tensioned; no sharp tails toward the opening.

Face approximately 2716.4 mm square; nominal opening 1586.8 mm square. Check equal diagonals and that pipes, braces and guys stay outside the flight opening.

Gentle front/back and side loading causes no anchor creep, foot lift, slipping or joint movement. Start a monitored low-wind trial only after these checks.

### Teardown and maintenance

1. Support the face with two people. Release the eight seam keys and the dock keys one border at a time. Pinch/release each fork rather than prying a locked bridge. Put keys in a labeled pouch.
2. Carry and store four rigid borders flat or well supported. Leave the channel splints, rib laps, cell bridges and other workshop ties installed. Release backing-frame keepers/socket retainers only if breaking the PVC structure down.
3. Remove guys/ballast only after the structure is supported or lowered. Inspect keys, pipe clips, ties and paper before the next setup. Replace damaged prints and wet or torn paper.

Paper replacement: loosen the appropriate cord and four top-cap ties; lift the five-piece cap chain, slide out the sheet, fit a new whole sheet, then refit and retension. The bay’s corner nodes and rear ribs can remain attached.

Record: first-build date __________ location/surface __________ observed fit or movement ______________________________ parts revised ______________________________
