rboyd/fpv-drone-racing-gate/output/full_width_demo/renders/03_ASSEMBLY_SEQUENCE.png

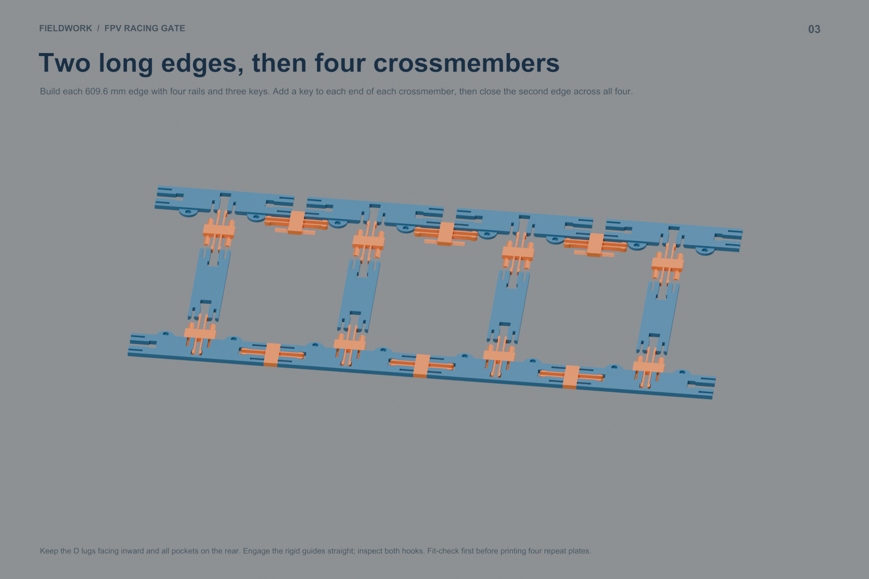
output/full_width_demo/renders/03_ASSEMBLY_SEQUENCE.png
