rboyd/fpv-drone-racing-gate/output/full_width_demo/renders/04_REPEAT_PRINT_PLATE.png

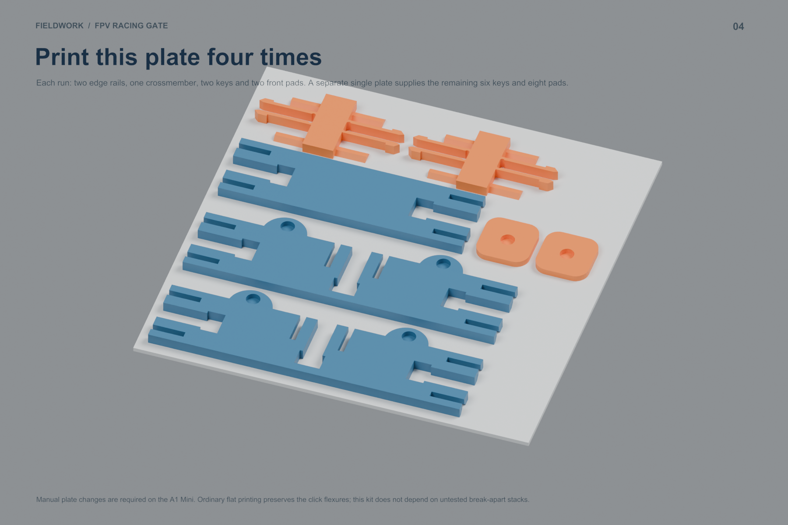
output/full_width_demo/renders/04_REPEAT_PRINT_PLATE.png
