rboyd/fpv-drone-racing-gate/output/renders/01_ASSEMBLED.png

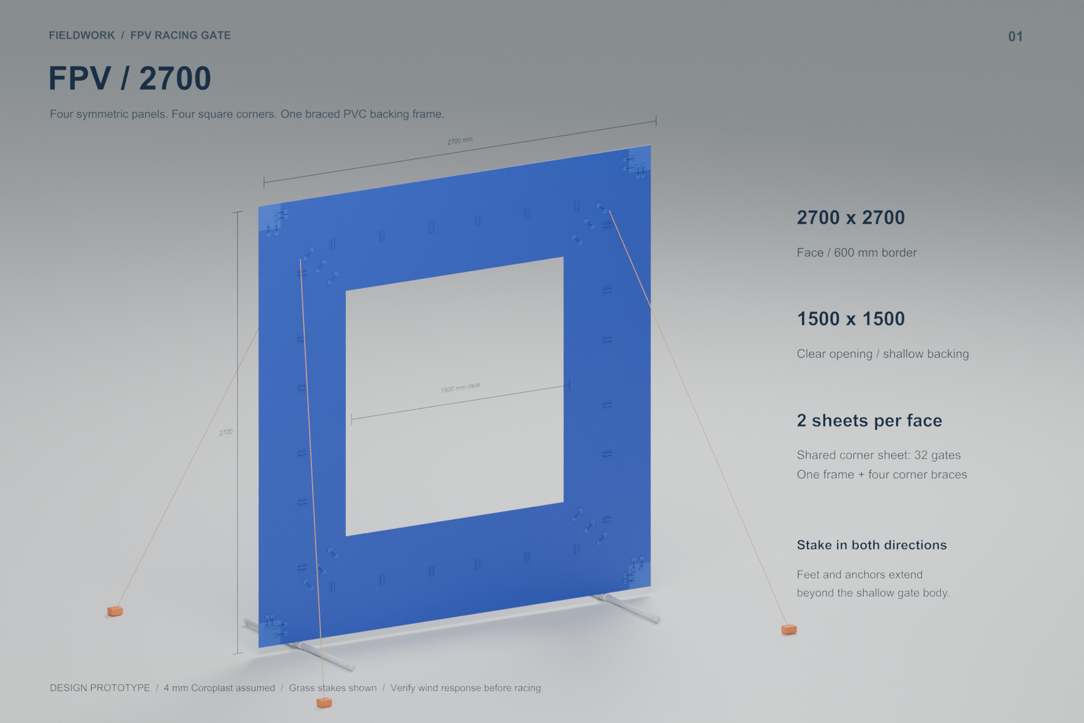
output/renders/01_ASSEMBLED.png
