rboyd/fpv-drone-racing-gate/output/rigid_whole_sheet/renders/04_MINI_ASSEMBLY.png

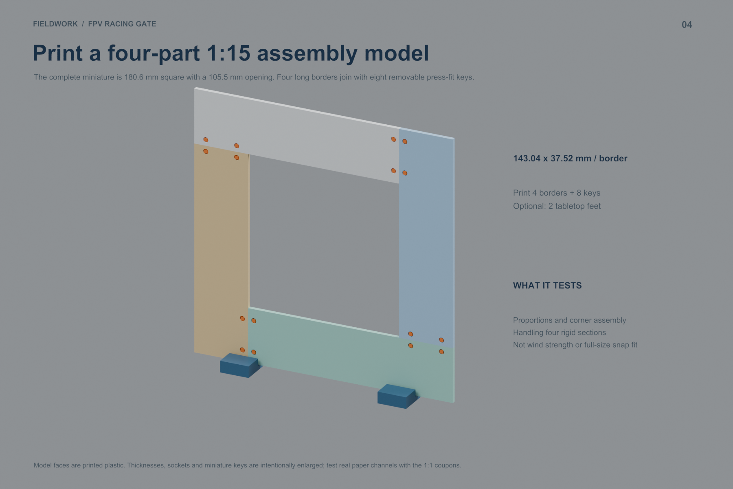
output/rigid_whole_sheet/renders/04_MINI_ASSEMBLY.png
