rboyd/fpv-drone-racing-gate/output/rigid_whole_sheet/renders/05_A1_MINI_PRINT_LAYOUT.png

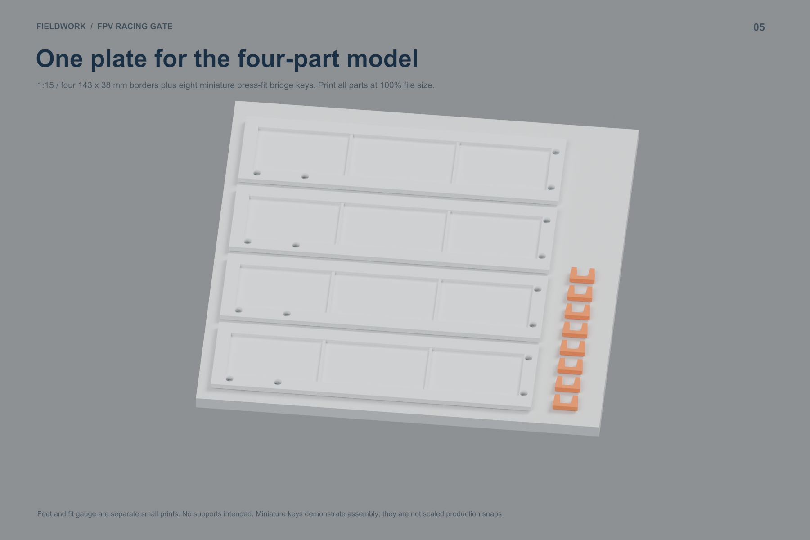
output/rigid_whole_sheet/renders/05_A1_MINI_PRINT_LAYOUT.png
