rboyd/fpv-drone-racing-gate/output/rigid_whole_sheet/renders/06_MINI_KEY_AND_TEST.png

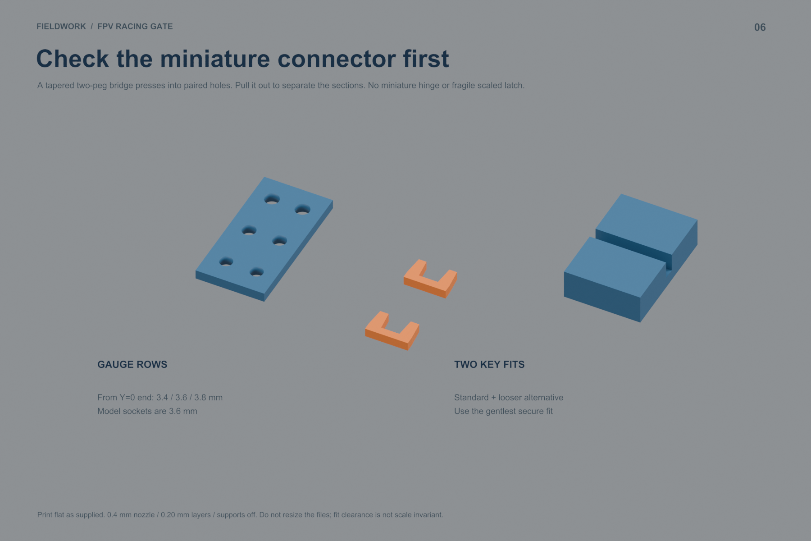
output/rigid_whole_sheet/renders/06_MINI_KEY_AND_TEST.png
